ronheywood/PiTrac/docs/3dprint/3dprint_base_layer_piside_floor.md

---
title: 3d Print Base Layer Pi Side Floor
layout: home
parent: 3D Print
nav_order: 3
---

3D Pi Side Floor.. search keyword 123

----
