ronheywood/PiTrac/docs/camera/cameras.md

---
title: Cameras
layout: home
nav_order: 2
---

Camera Parent page..

----
