ronheywood/PiTrac/docs/assets/images/camera/image5.jpg

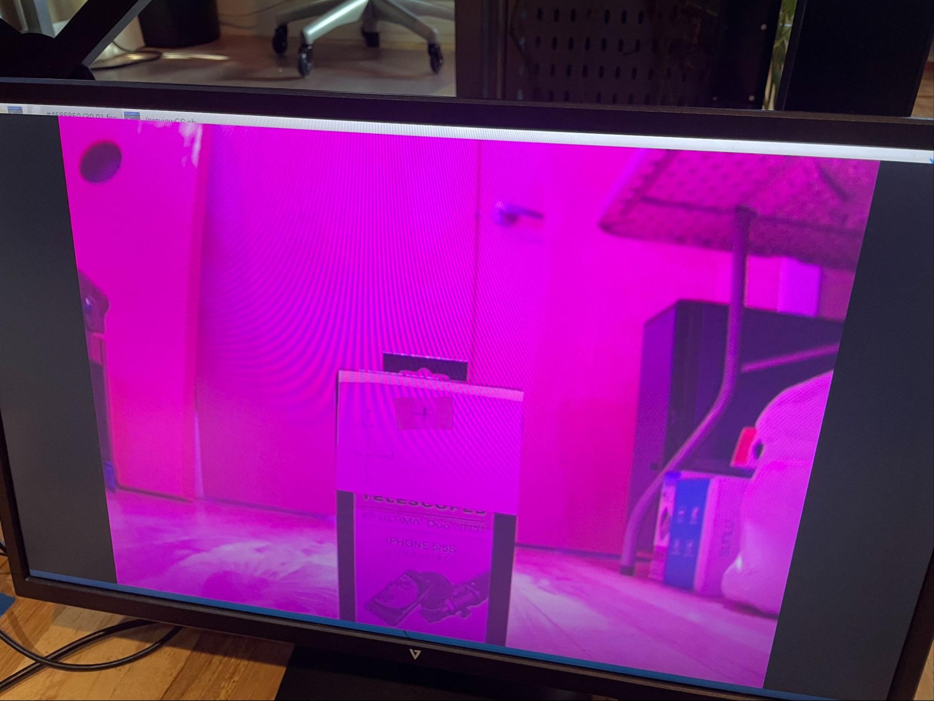
docs/assets/images/camera/image5.jpg
