ronheywood/PiTrac/Documentation/snapshots/index_replace_name.png

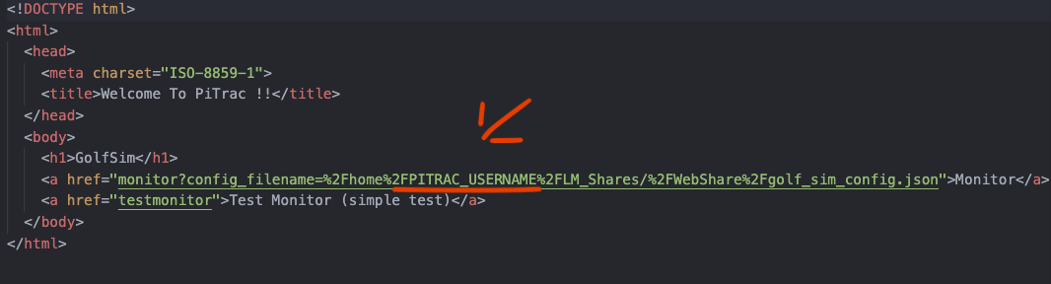
Documentation/snapshots/index_replace_name.png
