ronheywood/PiTrac/Hardware/Connector Board/PCB Board Picture (Both Layers).png

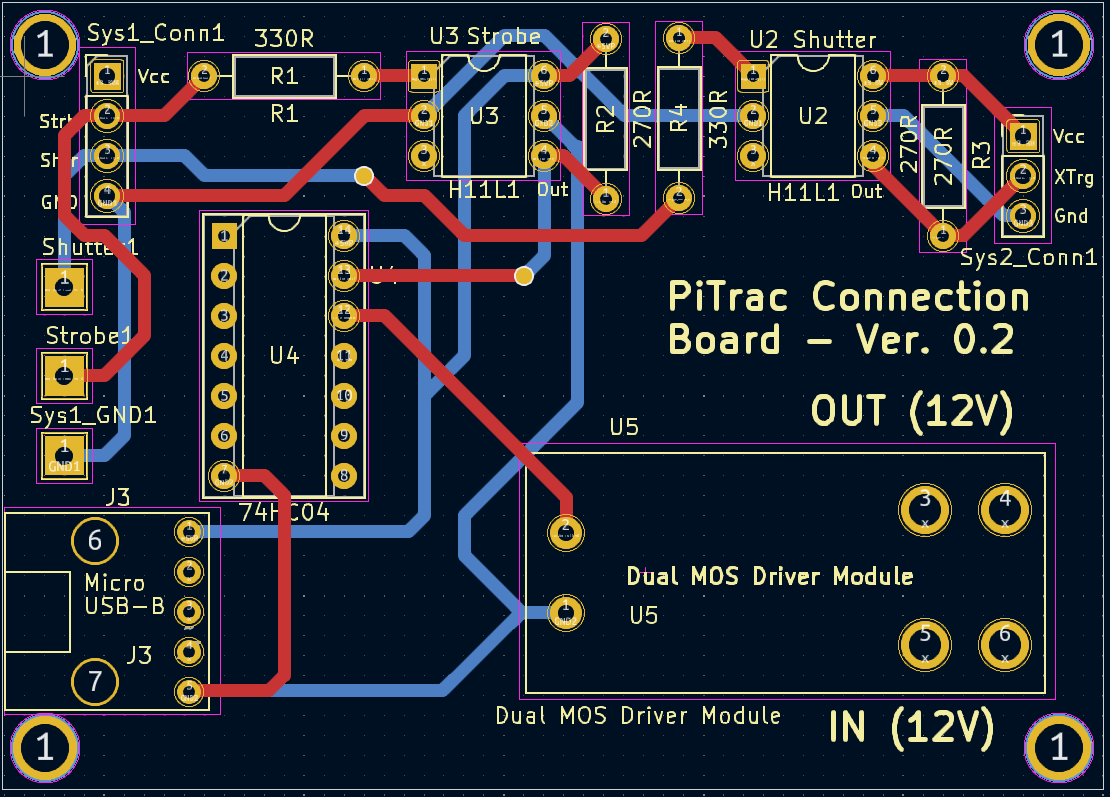
Hardware/Connector Board/PCB Board Picture (Both Layers).png
