ronheywood/PiTrac/Hardware/Connector Board/PiTrac Connector Board - Back.jpg

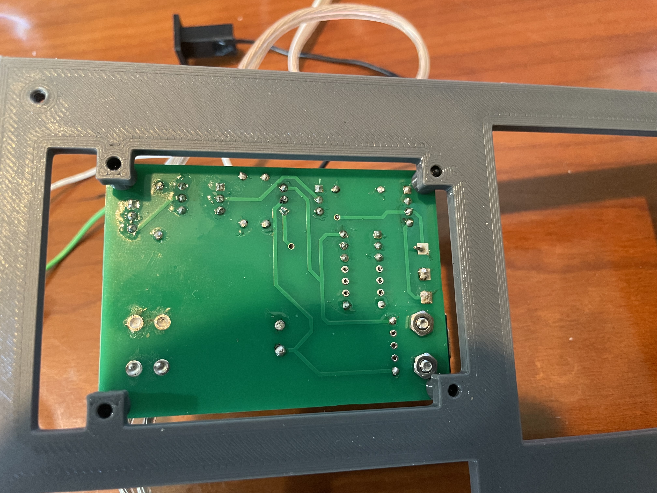
Hardware/Connector Board/PiTrac Connector Board - Back.jpg
