ronheywood/PiTrac/Hardware/Connector Board/PiTrac Connector Board - Front.jpg

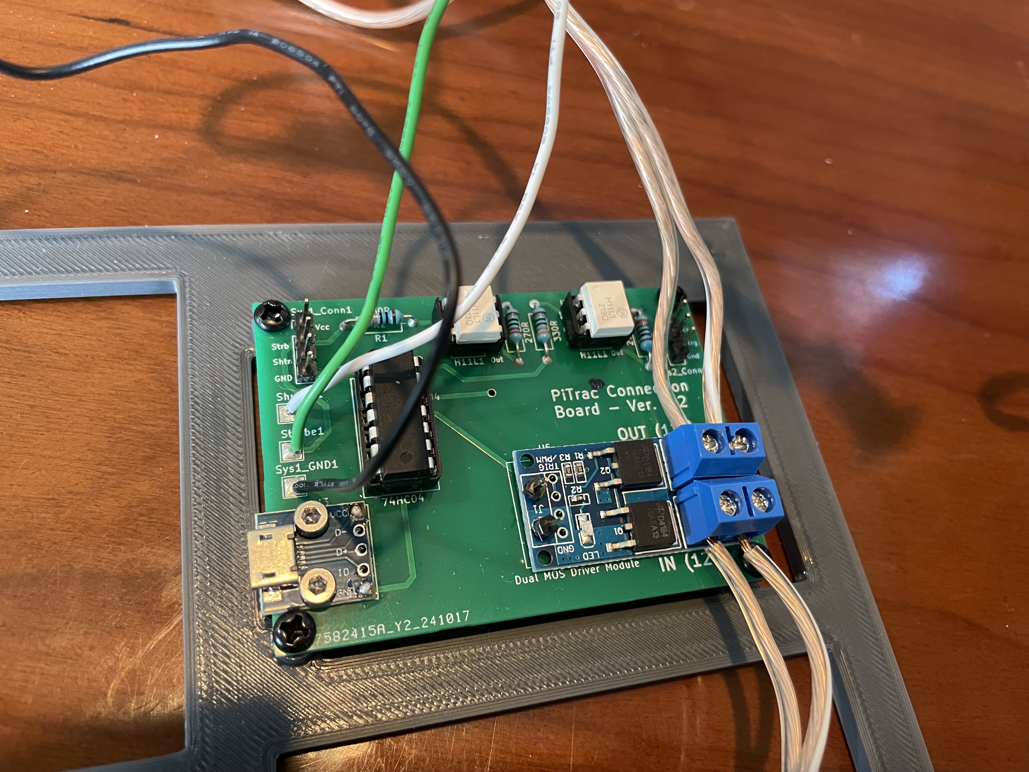
Hardware/Connector Board/PiTrac Connector Board - Front.jpg
