ronheywood/PiTrac/Software/LMSourceCode/Images/gs_log_img__log_ball_final_found_ball_img.png

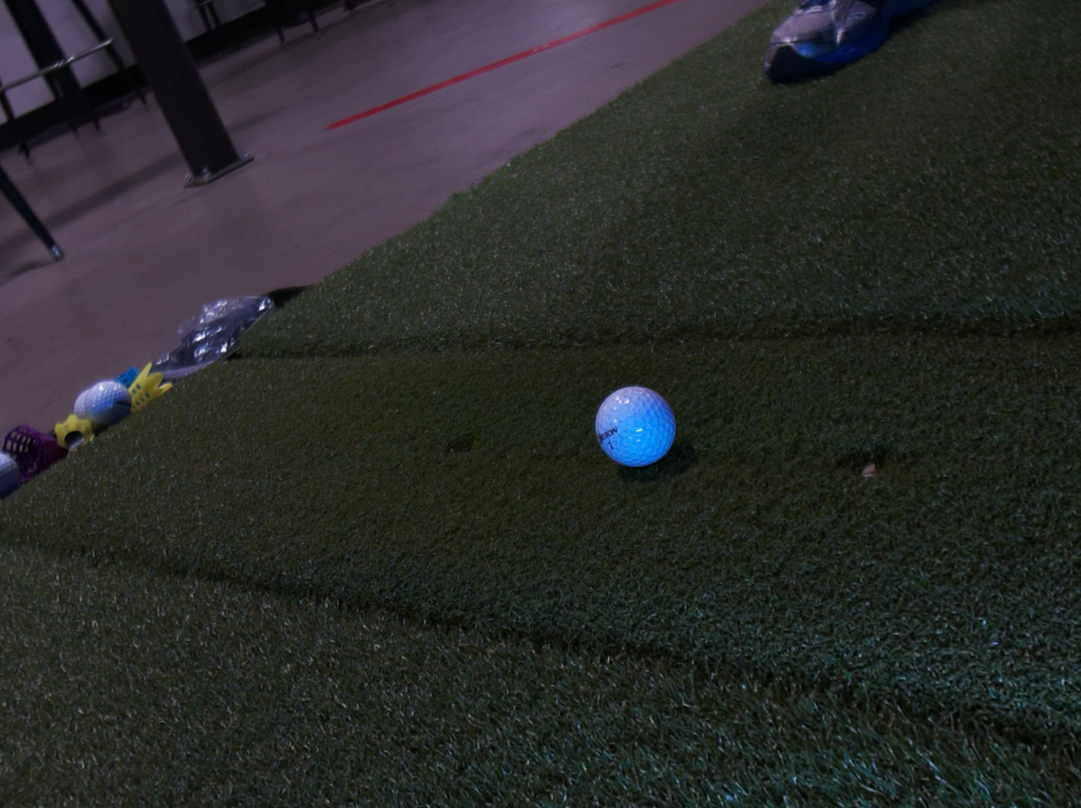
Software/LMSourceCode/Images/gs_log_img__log_ball_final_found_ball_img.png
