ronheywood/PiTrac/Software/LMSourceCode/Images/log_ball_final_found_ball_img.png

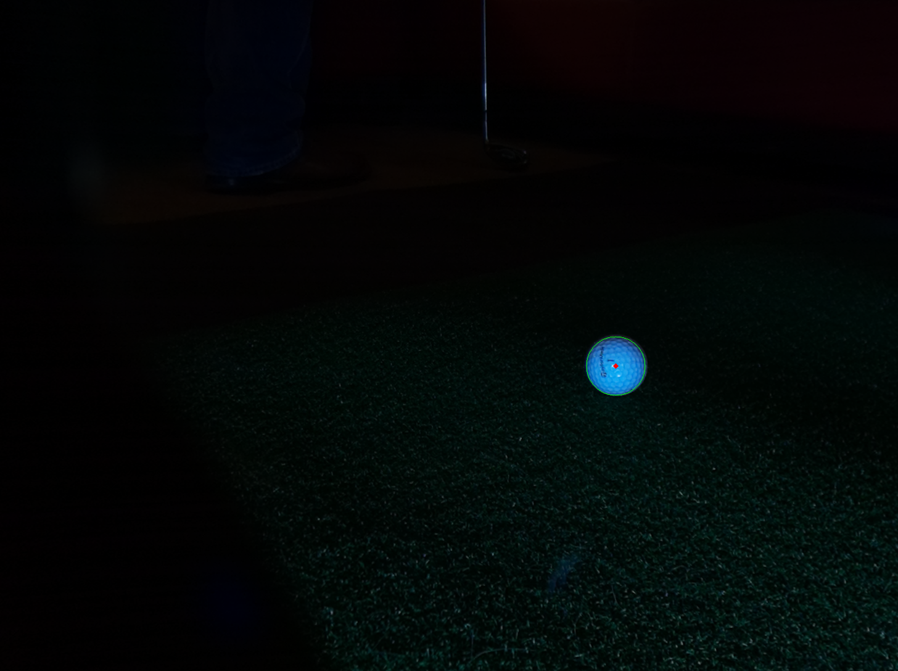
Software/LMSourceCode/Images/log_ball_final_found_ball_img.png
