ronheywood/PiTrac/Software/LMSourceCode/Images/log_ball_final_found_ball_img_232_fast.png

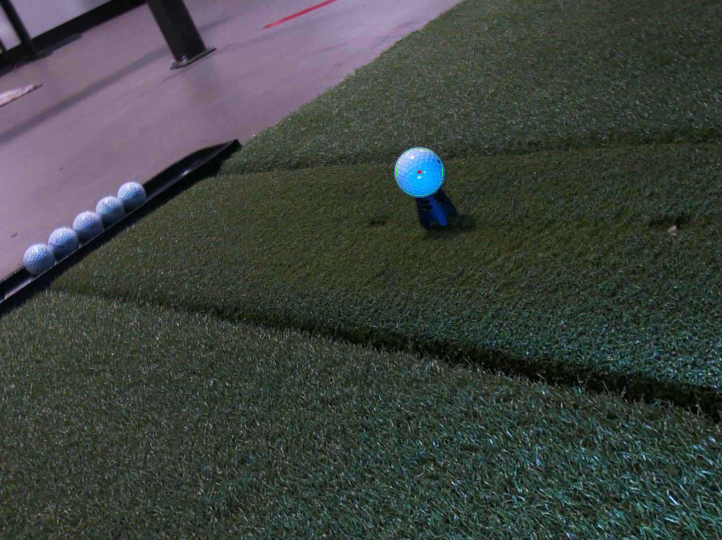
Software/LMSourceCode/Images/log_ball_final_found_ball_img_232_fast.png
