ronheywood/PiTrac/Software/LMSourceCode/Images/log_cam2_last_strobed_img.png

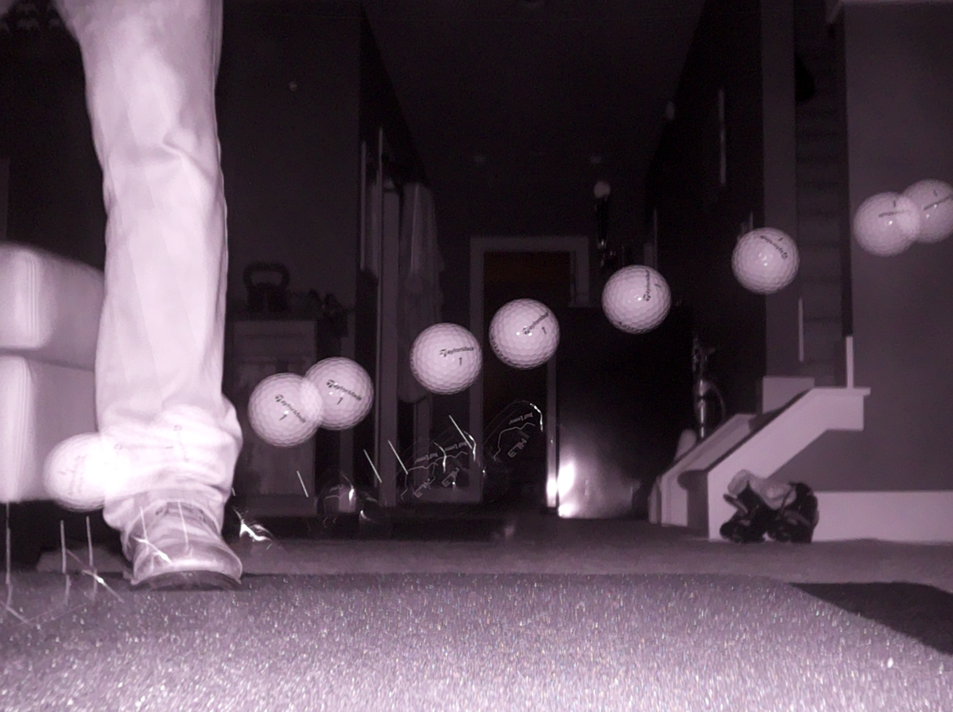
Software/LMSourceCode/Images/log_cam2_last_strobed_img.png
