ronheywood/PiTrac/Software/LMSourceCode/Images/log_cam2_last_strobed_img_232_fast.png

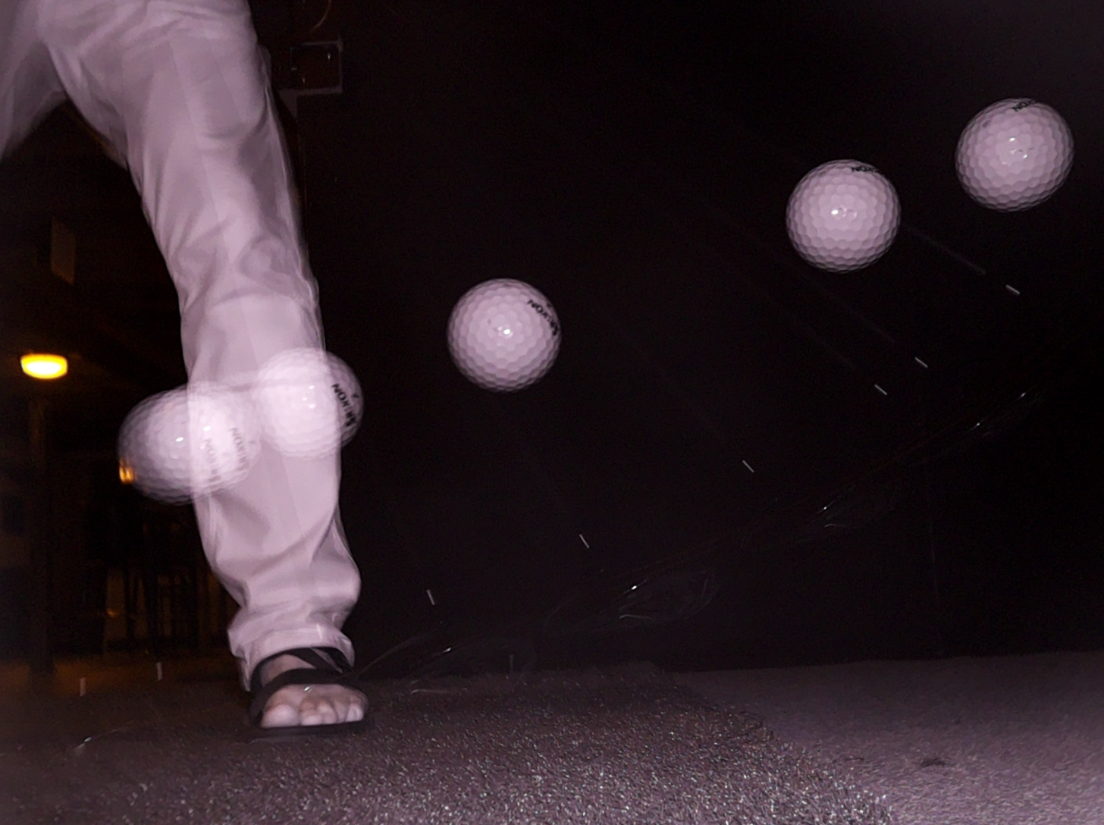
Software/LMSourceCode/Images/log_cam2_last_strobed_img_232_fast.png
