ronheywood/PiTrac/3D Printed Parts/Enclosure Models/Middle Layer - Power Side - Lower Floor/README.md

**Middle Layer – Power Side – Floor - Description:**

Please see the main Enclosure Assembly instructions in the Documentation folder for additional information on this part.

This is the middle-left-most floor portion of the PiTrac Launch Monitor. A [FreeCAD 1.0](https://www.freecad.org/downloads.php) compatible parameterized model is included here along with .stl files. This part a wall to prevent the power supplies and associated wiring from spilling into the area on the Pi side that is reserved for the Pi Camera. There is no “Upper” floor on the power-side in the middle layer.

The model is parameterized for ease of modifications, though the part is complex enough that any changes can sometimes lead to issues in FreeCAD. Modifiable parameters are in the “Master Document” spreadsheet, which is assumed to be in the directory immediately above wherever this part’s FreeCAD file exists.

Please consider supporting this work and the DIY LM project here: <https://ko-fi.com/PiTrac>

**Printing Notes:**

Both PLA or PETG can work for this part. It is a fairly simple part to print successfully.

Recommended print settings: 4 perimeter layers), 15% infill, grid infill patterns, no supports (see Prusa Slicer .3mf file for details).
