ronheywood/PiTrac/3D Printed Parts/Enclosure Models/Base Layer - Pi Side - Floor/Base Layer - Pi Side - Floor - 3D View.png

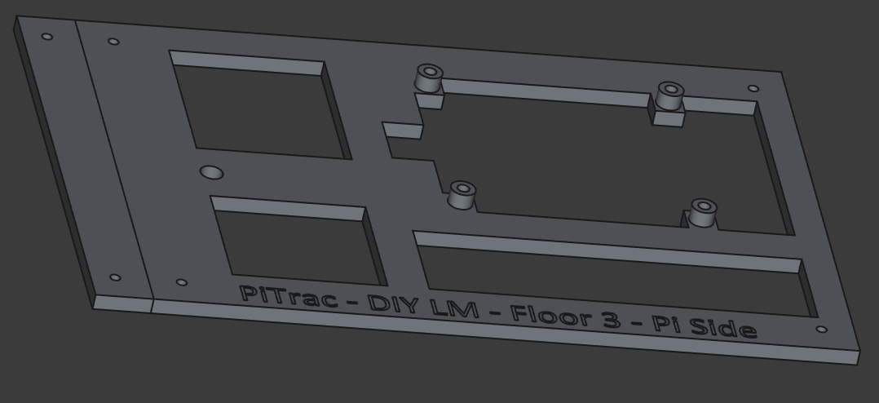
3D Printed Parts/Enclosure Models/Base Layer - Pi Side - Floor/Base Layer - Pi Side - Floor - 3D View.png
