ronheywood/PiTrac/3D Printed Parts/Enclosure Models/Base Layer - Pi Side - Wall/Base Layer - Pi Side - Wall - 3D View.png

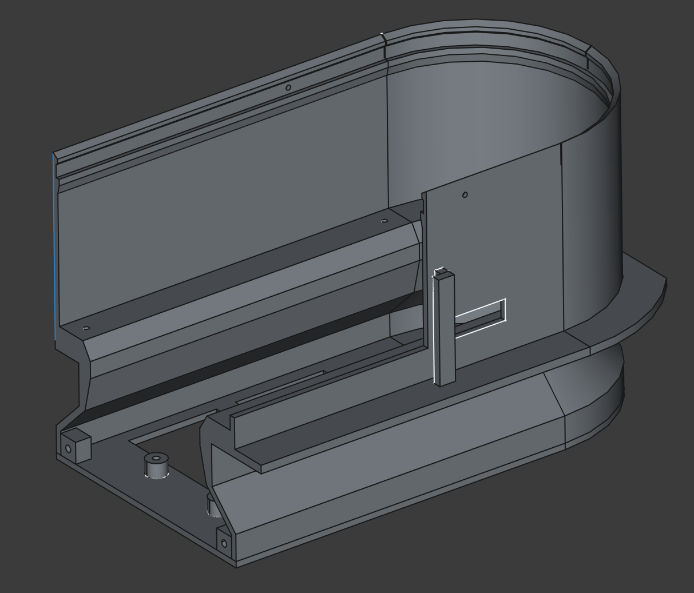
3D Printed Parts/Enclosure Models/Base Layer - Pi Side - Wall/Base Layer - Pi Side - Wall - 3D View.png
