ronheywood/PiTrac/3D Printed Parts/Enclosure Models/Base Layer - Pi Side - Wall/Base Layer - Pi Side - Wall - Slicer Output.png

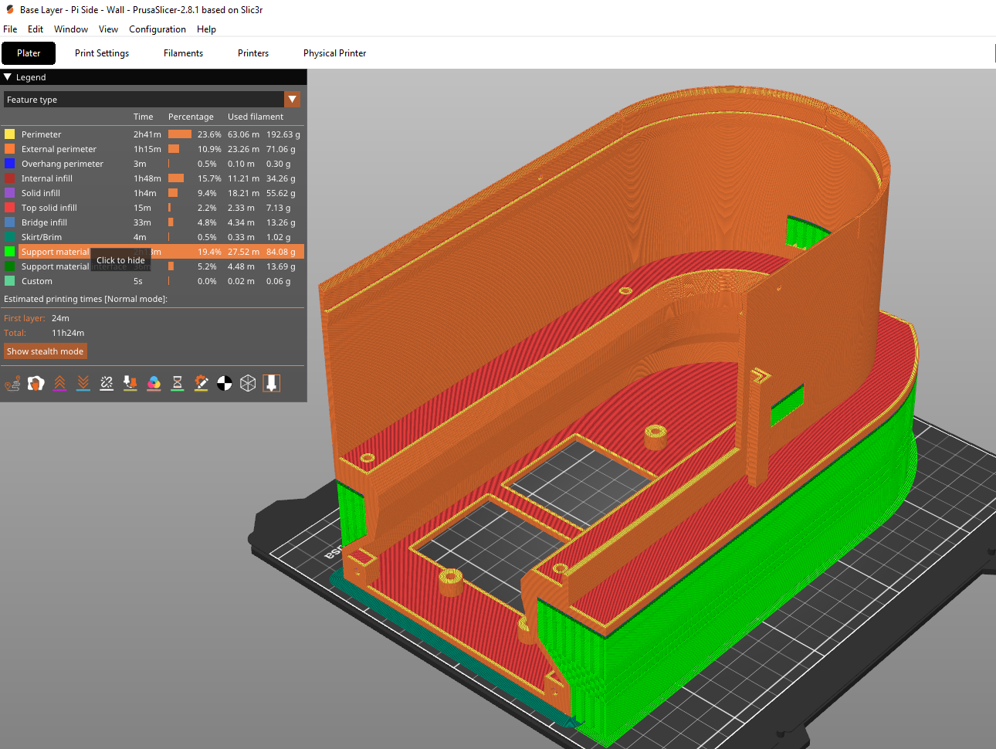
3D Printed Parts/Enclosure Models/Base Layer - Pi Side - Wall/Base Layer - Pi Side - Wall - Slicer Output.png
