ronheywood/PiTrac/3D Printed Parts/Enclosure Models/Base Layer - Power Side - Floor/Base Layer - Power Side - Lower Floor - Slicer Output.png

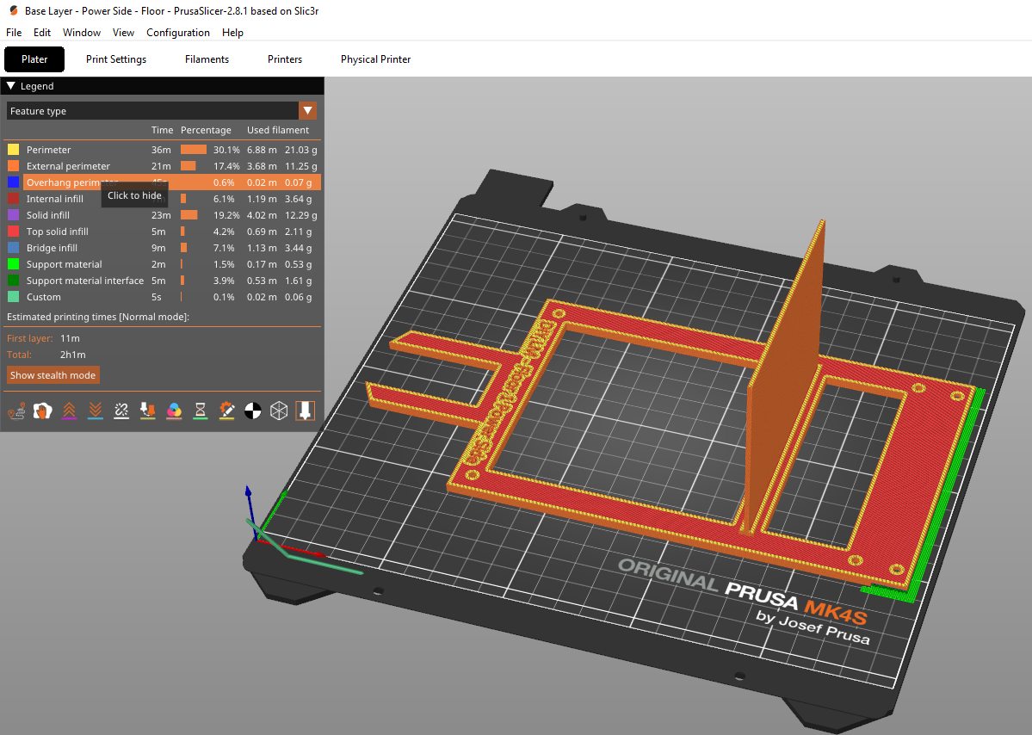
3D Printed Parts/Enclosure Models/Base Layer - Power Side - Floor/Base Layer - Power Side - Lower Floor - Slicer Output.png
