ronheywood/PiTrac/3D Printed Parts/Enclosure Models/Base Layer - Power Side - Wall/Base Layer - Power Side - Wall - 3D View.png

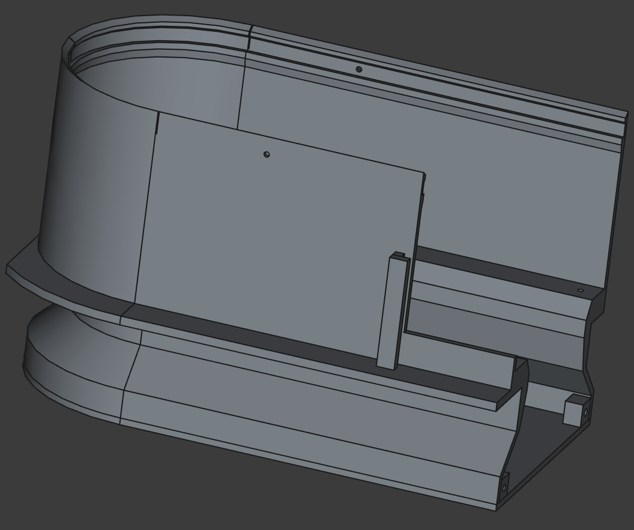
3D Printed Parts/Enclosure Models/Base Layer - Power Side - Wall/Base Layer - Power Side - Wall - 3D View.png
