ronheywood/PiTrac/3D Printed Parts/Enclosure Models/Base Layer - Power Side - Wall/Base Layer - Power Side - Wall - Slicer Output.png

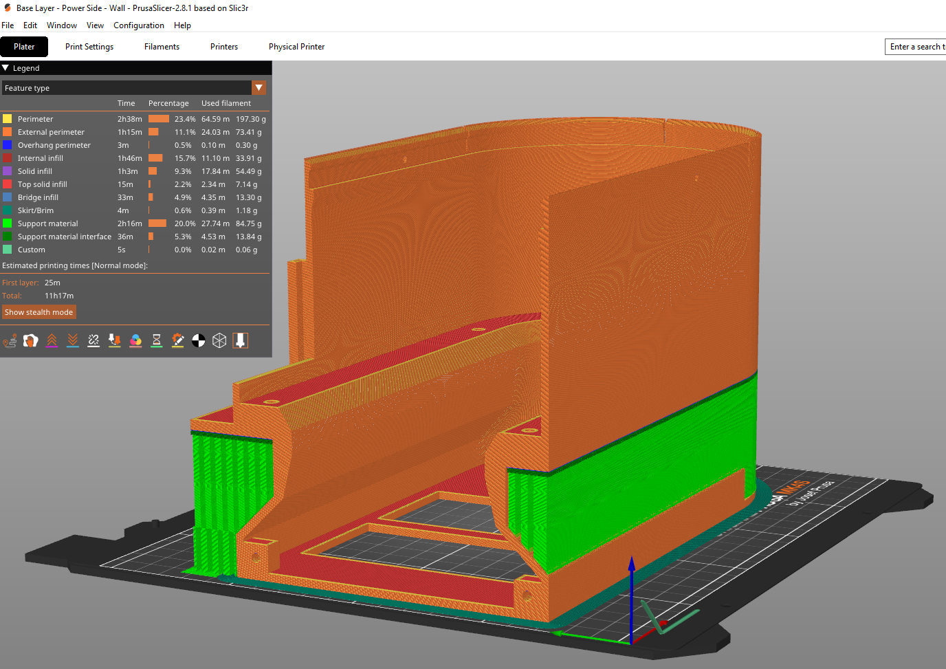
3D Printed Parts/Enclosure Models/Base Layer - Power Side - Wall/Base Layer - Power Side - Wall - Slicer Output.png
