ronheywood/PiTrac/3D Printed Parts/Enclosure Models/Middle Layer - Pi Side - Lower Floor/Middle Layer - Pi Side - Lower Floor - 3D View.png

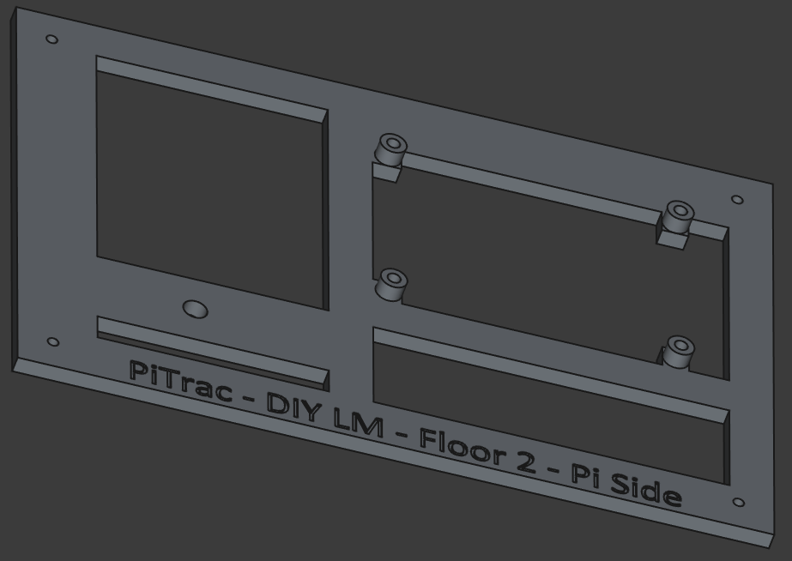
3D Printed Parts/Enclosure Models/Middle Layer - Pi Side - Lower Floor/Middle Layer - Pi Side - Lower Floor - 3D View.png
