ronheywood/PiTrac/3D Printed Parts/Enclosure Models/Middle Layer - Pi Side - Lower Floor/Middle Layer - Pi Side - Lower Floor - Slicer Output.png

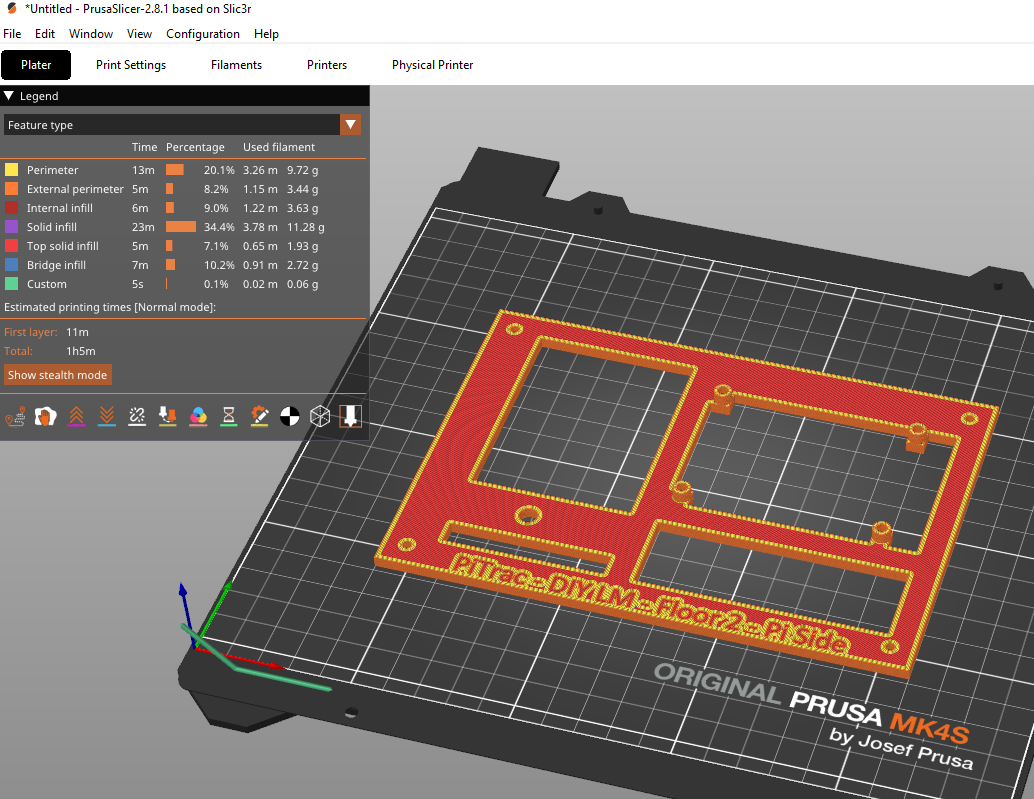
3D Printed Parts/Enclosure Models/Middle Layer - Pi Side - Lower Floor/Middle Layer - Pi Side - Lower Floor - Slicer Output.png
