ronheywood/PiTrac/3D Printed Parts/Enclosure Models/Middle Layer - Pi Side - Upper Floor/Middle Layer - Pi Side - Upper Floor - 3D View.png

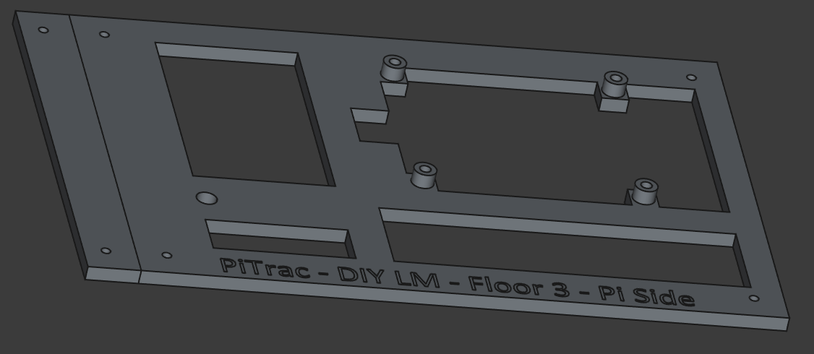
3D Printed Parts/Enclosure Models/Middle Layer - Pi Side - Upper Floor/Middle Layer - Pi Side - Upper Floor - 3D View.png
