ronheywood/PiTrac/3D Printed Parts/Enclosure Models/Middle Layer - Pi Side - Wall/Middle Layer - Pi Side - Wall - 3D View.png

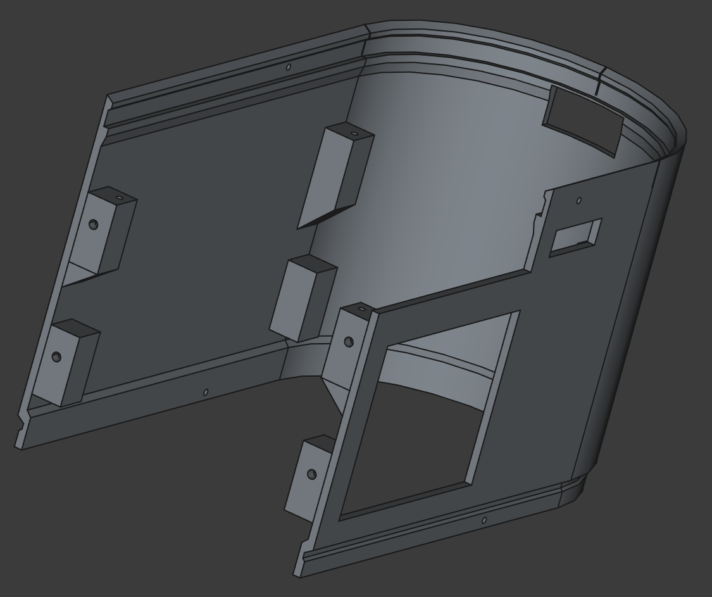
3D Printed Parts/Enclosure Models/Middle Layer - Pi Side - Wall/Middle Layer - Pi Side - Wall - 3D View.png
