ronheywood/PiTrac/3D Printed Parts/Enclosure Models/Middle Layer - Pi Side - Wall/Middle Layer - Pi Side - Wall - Slicer Output.png

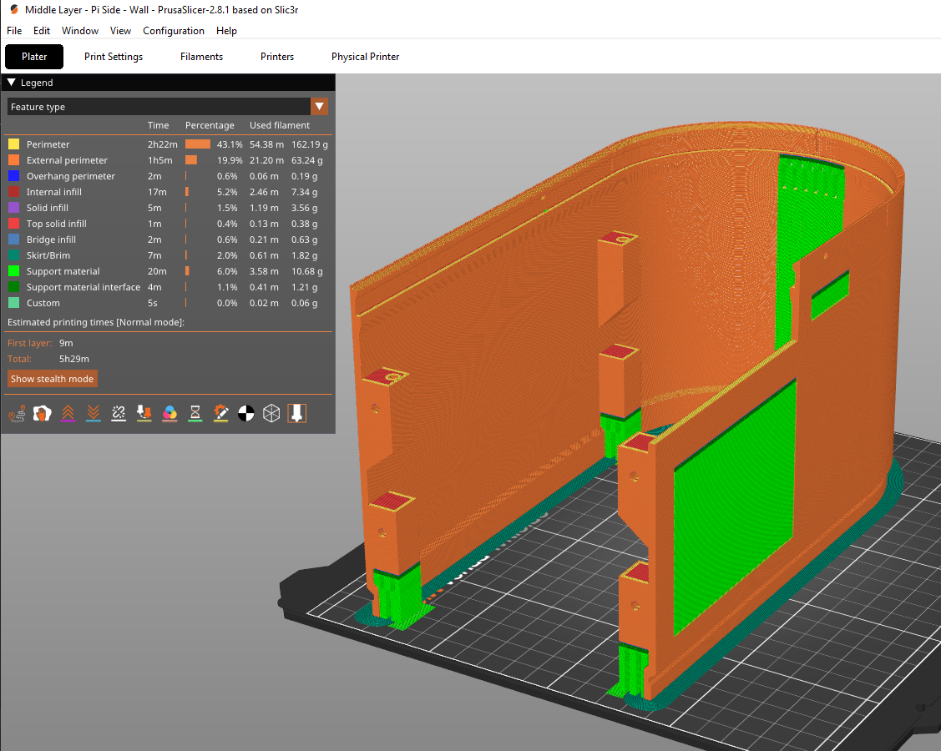
3D Printed Parts/Enclosure Models/Middle Layer - Pi Side - Wall/Middle Layer - Pi Side - Wall - Slicer Output.png
