ronheywood/PiTrac/3D Printed Parts/Enclosure Models/Middle Layer - Power Side - Lower Floor/Middle Layer - Power Side - Lower - Slicer Output.png

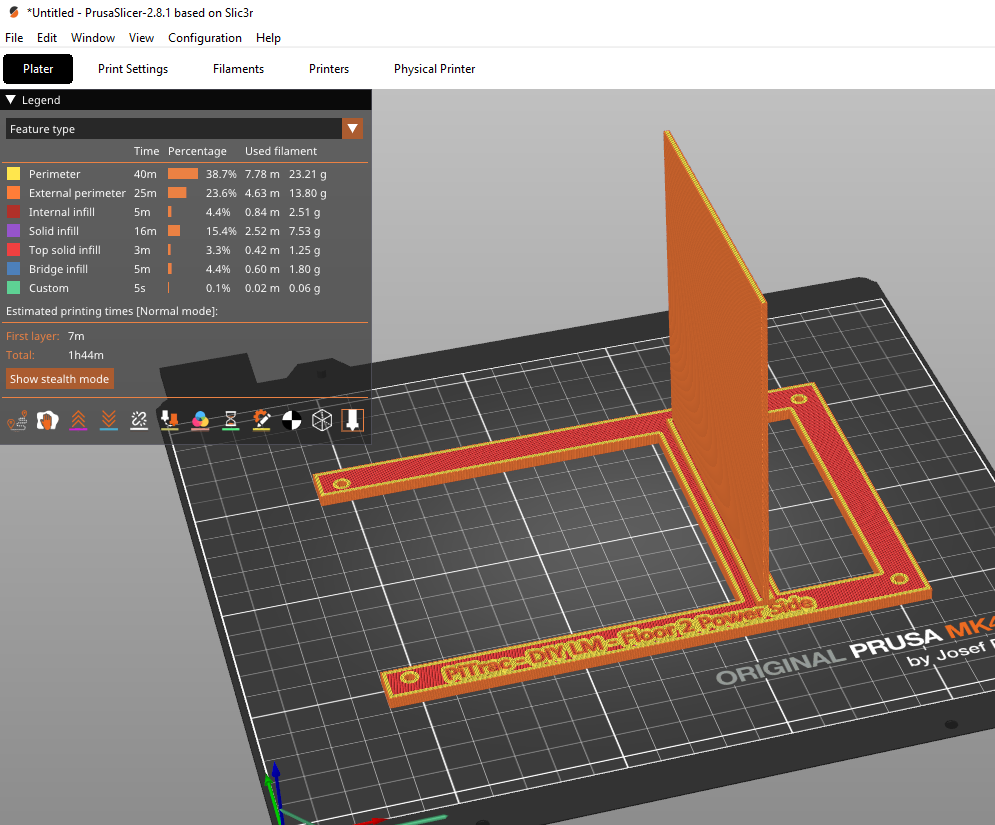
3D Printed Parts/Enclosure Models/Middle Layer - Power Side - Lower Floor/Middle Layer - Power Side - Lower - Slicer Output.png
