ronheywood/PiTrac/3D Printed Parts/Enclosure Models/Middle Layer - Power Side - Wall/Middle Layer - Power Side - Wall - 3D View.docx.png

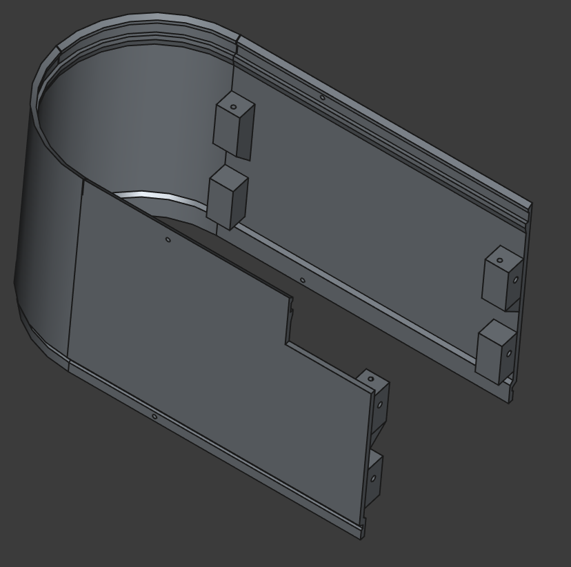
3D Printed Parts/Enclosure Models/Middle Layer - Power Side - Wall/Middle Layer - Power Side - Wall - 3D View.docx.png
