ronheywood/PiTrac/3D Printed Parts/Enclosure Models/Middle Layer - Power Side - Wall/Middle Layer - Power Side - Wall -Slicer Output.png

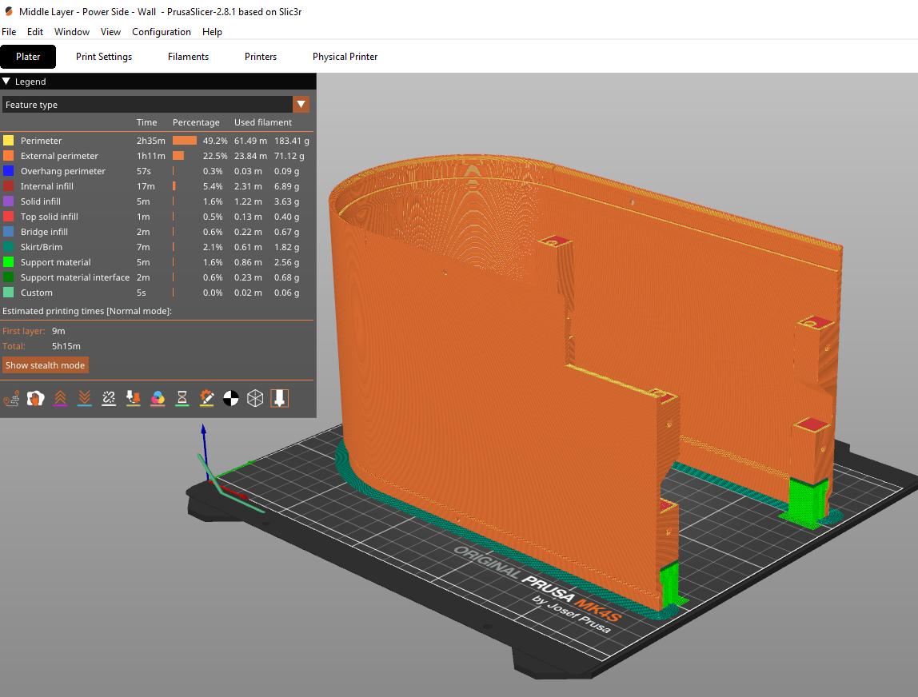
3D Printed Parts/Enclosure Models/Middle Layer - Power Side - Wall/Middle Layer - Power Side - Wall -Slicer Output.png
