ronheywood/PiTrac/3D Printed Parts/Enclosure Models/Top Layer - Pi Side - Wall/Top Layer - Pi Side - Wall - 3D View.png

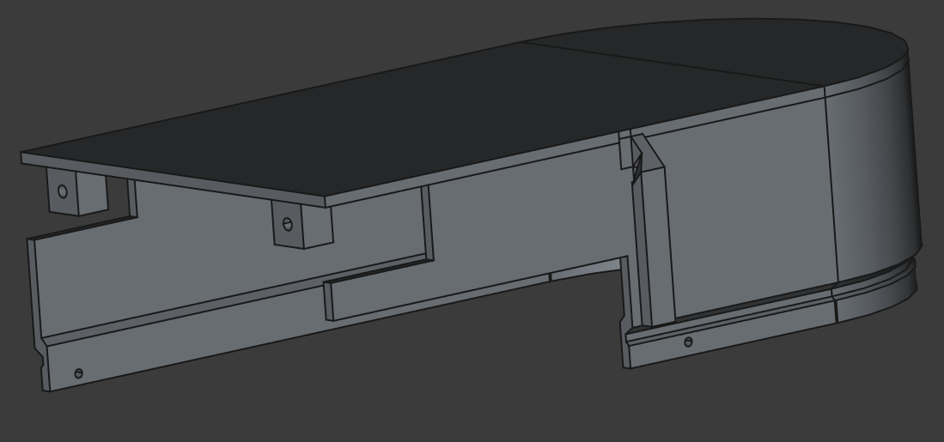
3D Printed Parts/Enclosure Models/Top Layer - Pi Side - Wall/Top Layer - Pi Side - Wall - 3D View.png
