ronheywood/PiTrac/3D Printed Parts/Enclosure Models/Top Layer - Pi Side - Wall/Top Layer - Pi Side - Wall - Slicer Output.png

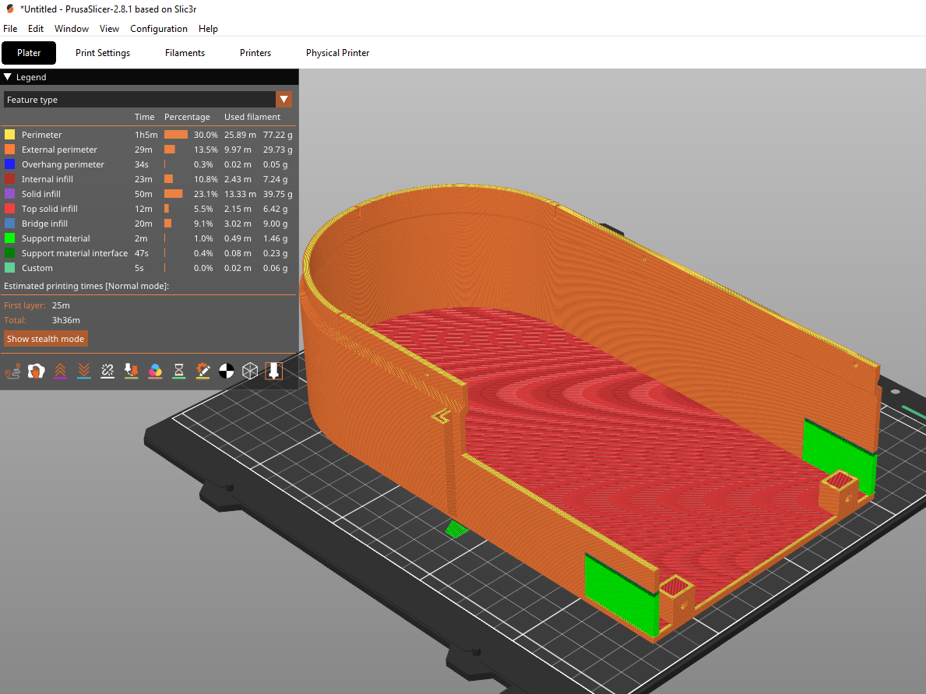
3D Printed Parts/Enclosure Models/Top Layer - Pi Side - Wall/Top Layer - Pi Side - Wall - Slicer Output.png
