ronheywood/PiTrac/3D Printed Parts/Enclosure Models/Top Layer - Power Side - Wall/Top Layer - Power Side - Wall - 3D View.png

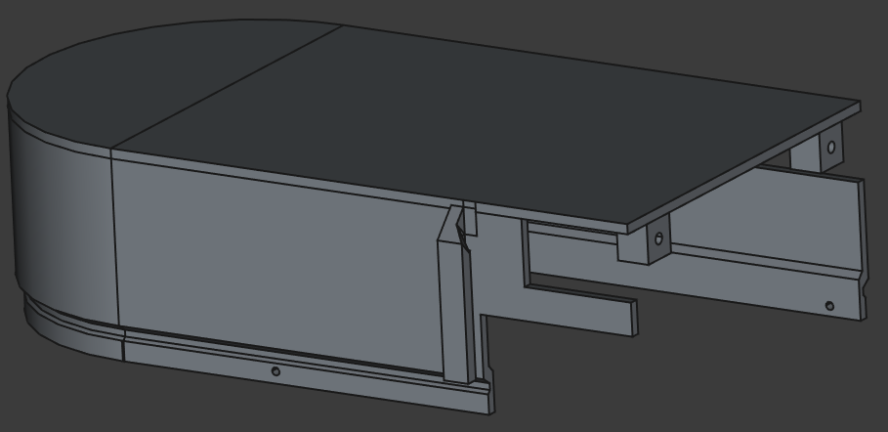
3D Printed Parts/Enclosure Models/Top Layer - Power Side - Wall/Top Layer - Power Side - Wall - 3D View.png
