ronheywood/PiTrac/3D Printed Parts/Enclosure Models/Top Layer - Power Side - Wall/Top Layer - Power Side - Wall - Slicer Output.png

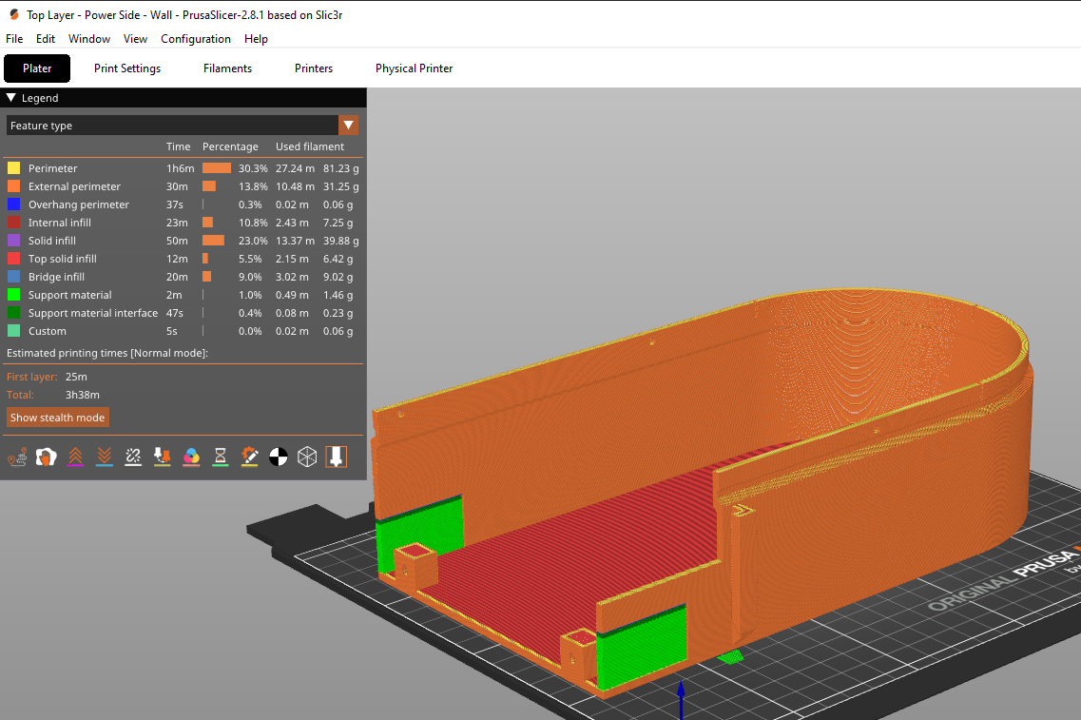
3D Printed Parts/Enclosure Models/Top Layer - Power Side - Wall/Top Layer - Power Side - Wall - Slicer Output.png
