ronheywood/PiTrac/3D Printed Parts/Enclosure Version 2/BaseBox/BaseBox - 3D Model.png

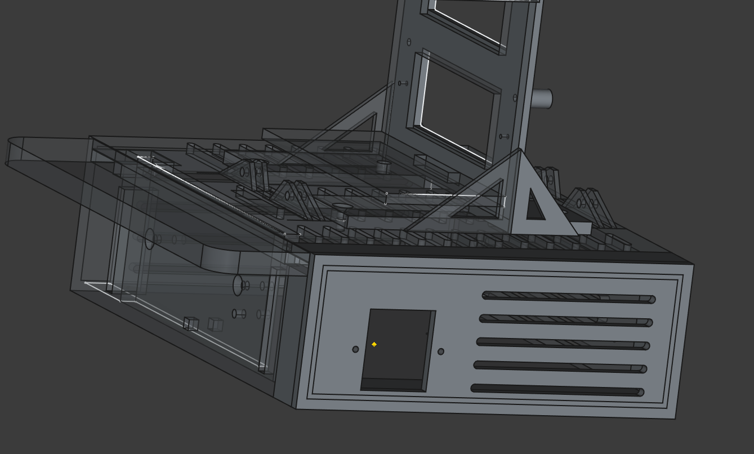
3D Printed Parts/Enclosure Version 2/BaseBox/BaseBox - 3D Model.png
