ronheywood/PiTrac/3D Printed Parts/Enclosure Version 2/BaseBox/BaseBox - End Cap - Slicer Output.png

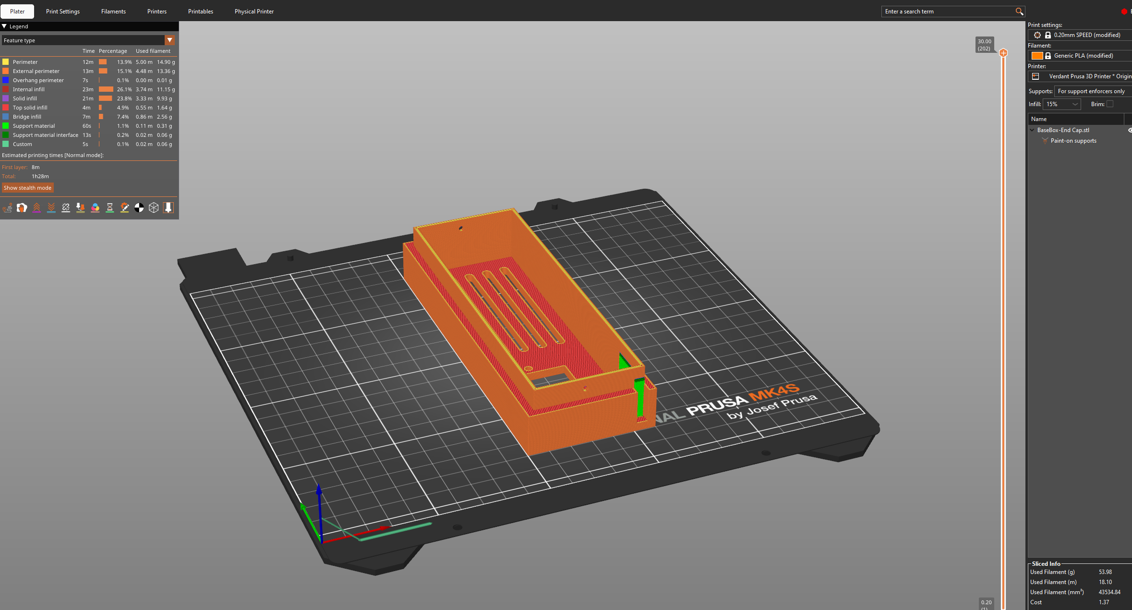
3D Printed Parts/Enclosure Version 2/BaseBox/BaseBox - End Cap - Slicer Output.png
