ronheywood/PiTrac/3D Printed Parts/Enclosure Version 2/BaseBox/BaseBox - Main Body - Slicer Output.png

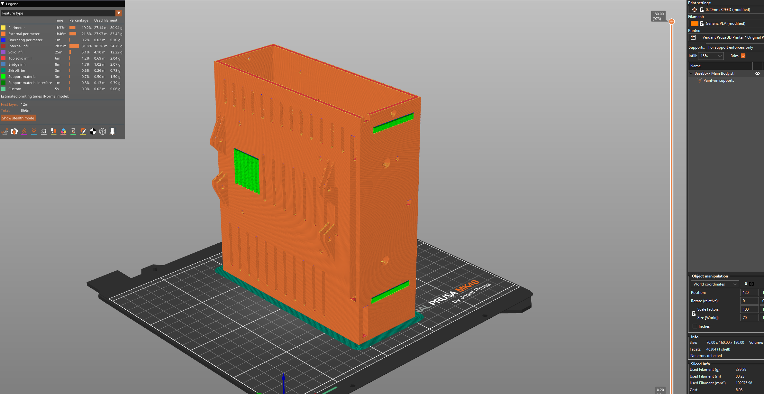
3D Printed Parts/Enclosure Version 2/BaseBox/BaseBox - Main Body - Slicer Output.png
