ronheywood/PiTrac/3D Printed Parts/Enclosure Version 2/LED-Array-Strobe-Light-Mount/Strobe Mount - Back View.jpg

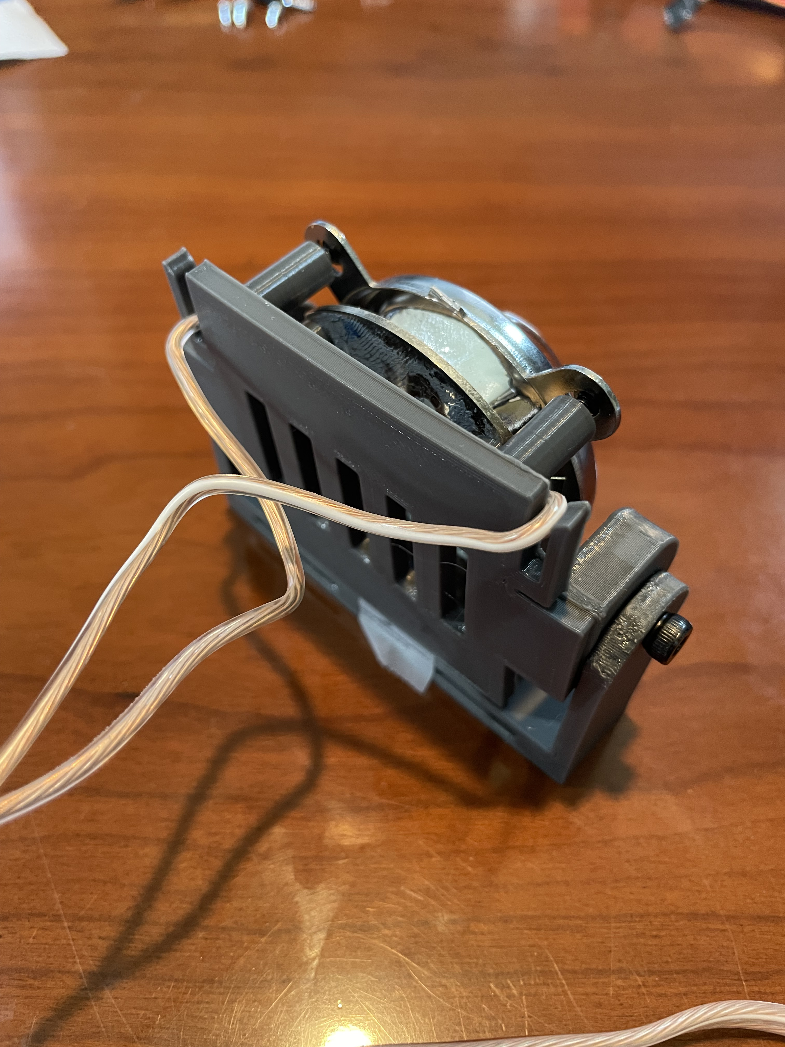
3D Printed Parts/Enclosure Version 2/LED-Array-Strobe-Light-Mount/Strobe Mount - Back View.jpg
