ronheywood/PiTrac/3D Printed Parts/Enclosure Version 2/Pi-Camera-Light-Filter-Holder - M12/Filter Holder - Annotated 3D Model.png

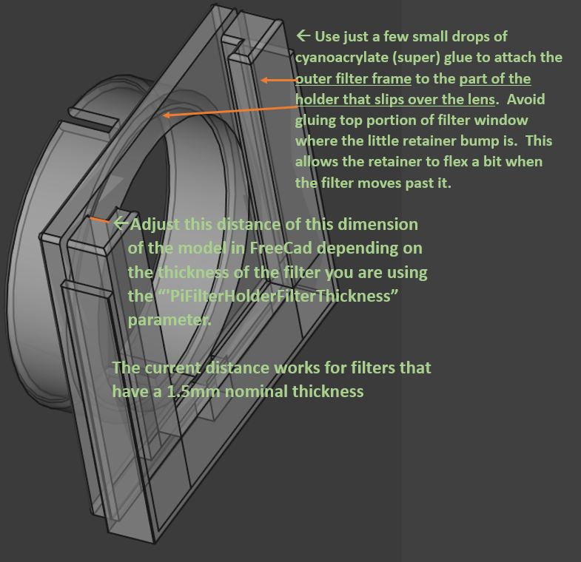
3D Printed Parts/Enclosure Version 2/Pi-Camera-Light-Filter-Holder - M12/Filter Holder - Annotated 3D Model.png
