ronheywood/PiTrac/3D Printed Parts/Enclosure Version 2/Pi-Camera-Light-Filter-Holder - M12/Filter Holder - Prusa Slicer Output.png

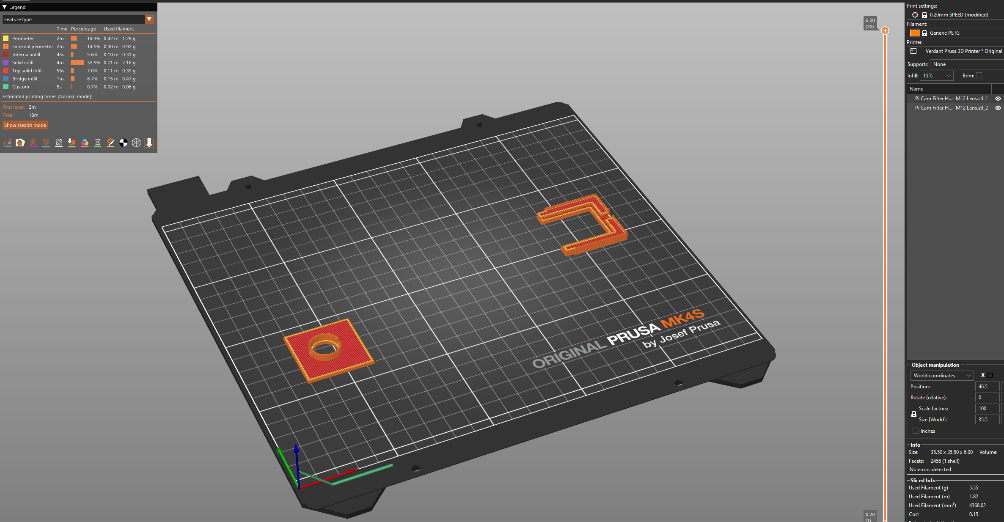
3D Printed Parts/Enclosure Version 2/Pi-Camera-Light-Filter-Holder - M12/Filter Holder - Prusa Slicer Output.png
