ronheywood/PiTrac/3D Printed Parts/Enclosure Version 2/Pi-Camera-Light-Filter-Holder - M12/Filter Holder on Camera.jpg

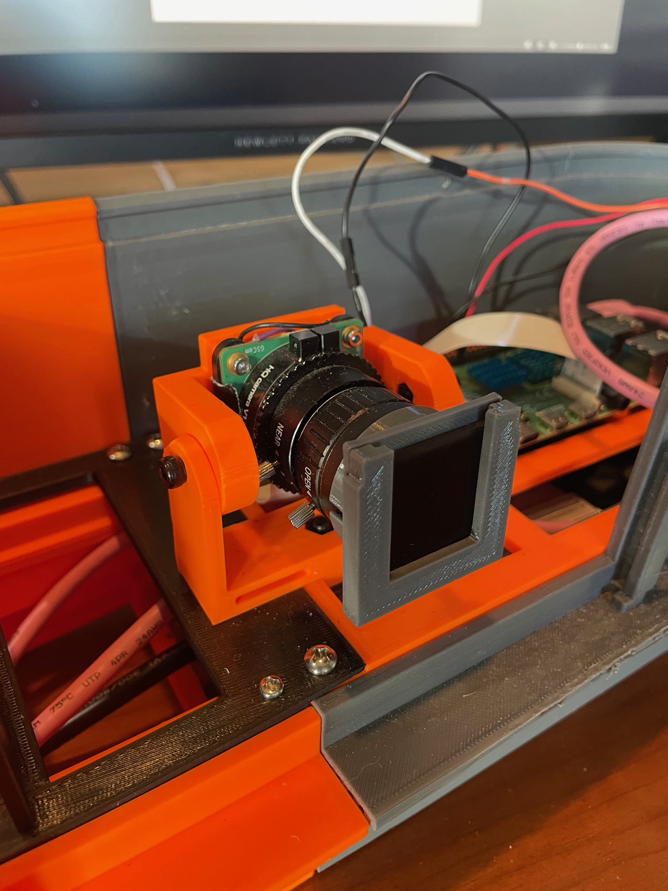
3D Printed Parts/Enclosure Version 2/Pi-Camera-Light-Filter-Holder - M12/Filter Holder on Camera.jpg
