ronheywood/PiTrac/3D Printed Parts/Enclosure Version 2/Pi-Camera-Mounts - Innomaker CAM-IMX296/Pi Camera Mount -  Innomaker IMX296 - Example - Back.jpg

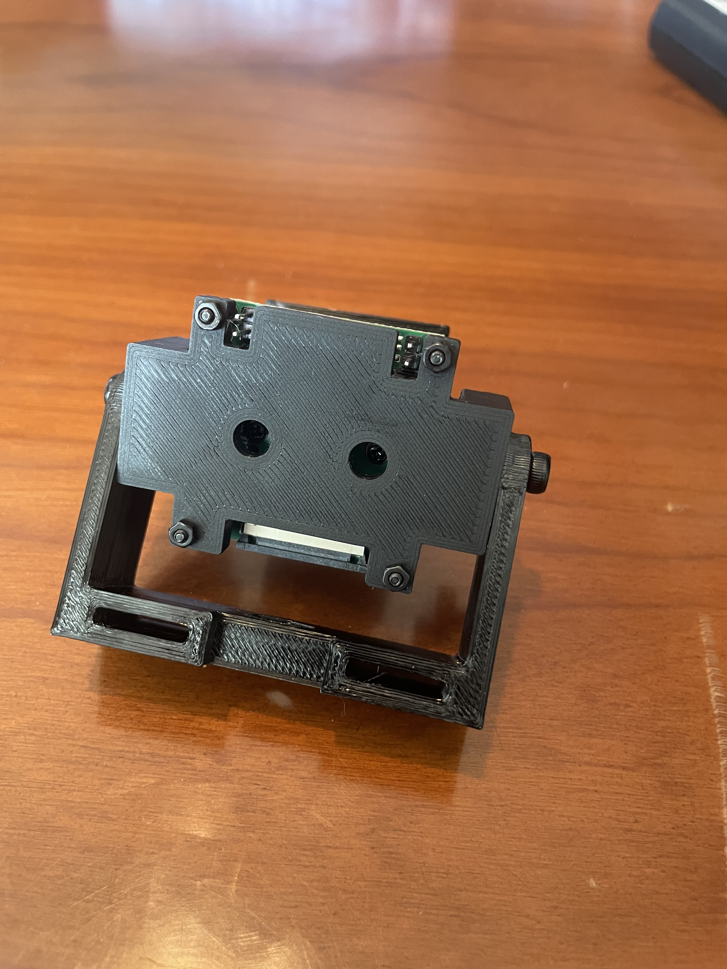
3D Printed Parts/Enclosure Version 2/Pi-Camera-Mounts - Innomaker CAM-IMX296/Pi Camera Mount - Innomaker IMX296 - Example - Back.jpg
