ronheywood/PiTrac/3D Printed Parts/Enclosure Version 2/Pi-Camera-Mounts - Innomaker CAM-IMX296/Pi Camera Mount - Example Variations.png

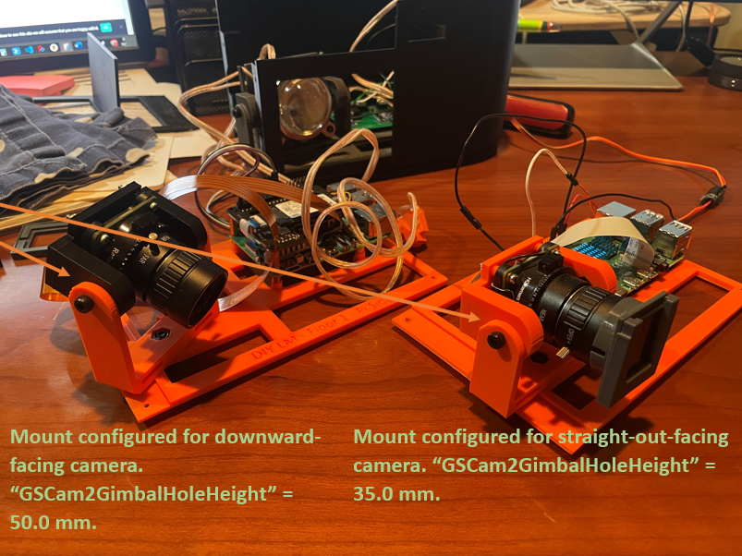
3D Printed Parts/Enclosure Version 2/Pi-Camera-Mounts - Innomaker CAM-IMX296/Pi Camera Mount - Example Variations.png
