ronheywood/PiTrac/3D Printed Parts/Enclosure Version 2/Tower/Tower - 3D Model.png

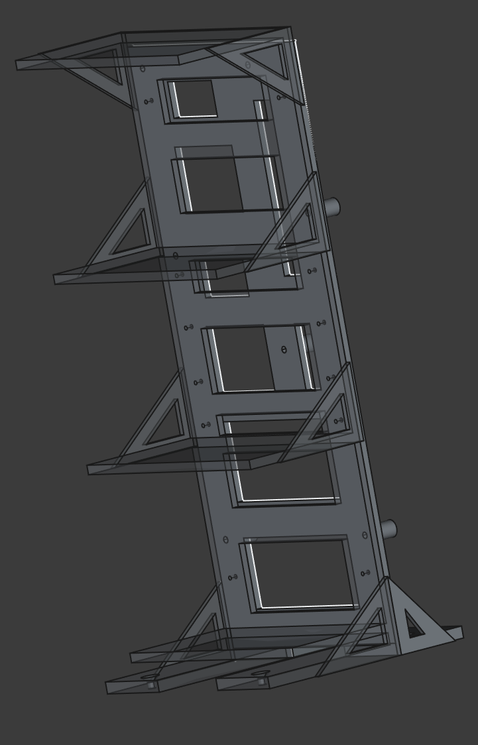
3D Printed Parts/Enclosure Version 2/Tower/Tower - 3D Model.png
