ronheywood/PiTrac/3D Printed Parts/Enclosure Version 2/Tower/Tower - Backplate - Slicer Output.png

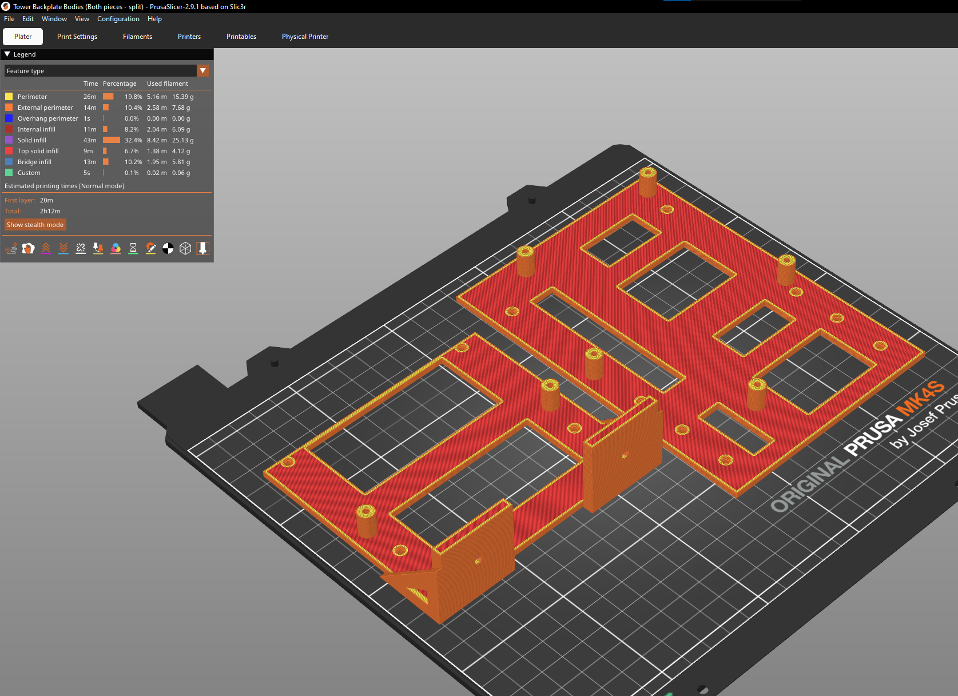
3D Printed Parts/Enclosure Version 2/Tower/Tower - Backplate - Slicer Output.png
