ronheywood/PiTrac/3D Printed Parts/Enclosure Version 2/CaseCover/CaseCover.FCStd

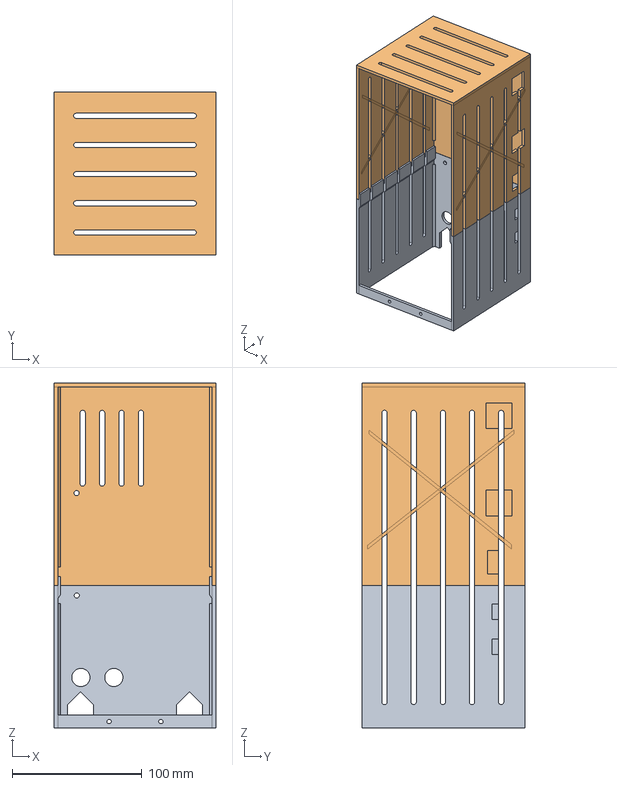
[picture p82: CAD file, 2025-05-21]
3D Printed Parts/Enclosure Version 2/CaseCover/CaseCover.FCStd
124.6 x 126.0 x 266.1 mm
Lower Case Cover Body
Upper Case Cover Body
