ronheywood/PiTrac/3D Printed Parts/Enclosure Version 2/Integrated Enclosure (DO NOT PRINT)/C14 Panel Mount Power Plug Adapter w Fuse - JR-101-1F.FCStd

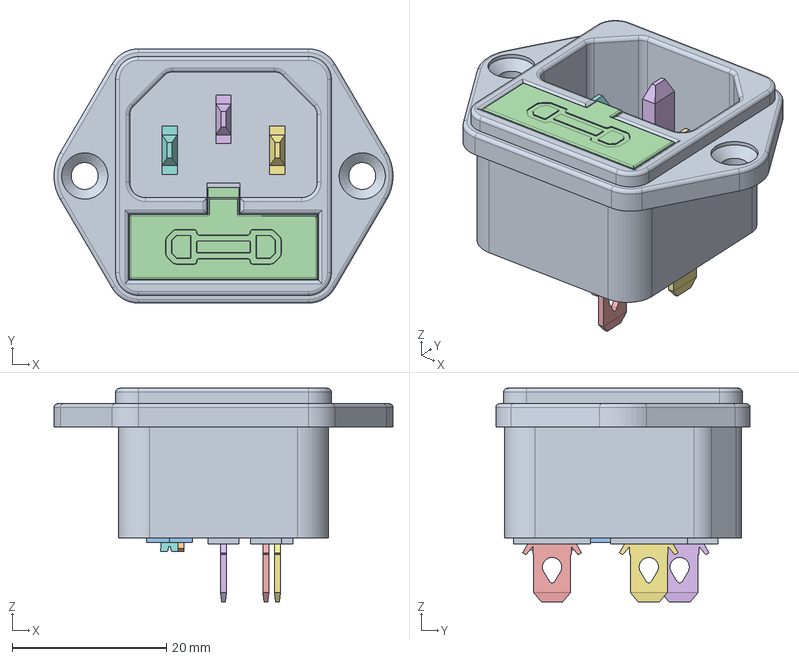
[picture p83: CAD file, 2025-03-30]
3D Printed Parts/Enclosure Version 2/Integrated Enclosure (DO NOT PRINT)/C14 Panel Mount Power Plug Adapter w Fuse - JR-101-1F.FCStd
44.0 x 33.0 x 27.7 mm
JR-101-1F
JR-101-1F001
JR-101-1F002
JR-101-1F003
JR-101-1F004
JR-101-1F005
JR-101-1F006
JR-101-1F007
