ronheywood/PiTrac/3D Printed Parts/Enclosure Version 2/LED-Array-Strobe-Light-Mount/LED Light Mount.FCStd

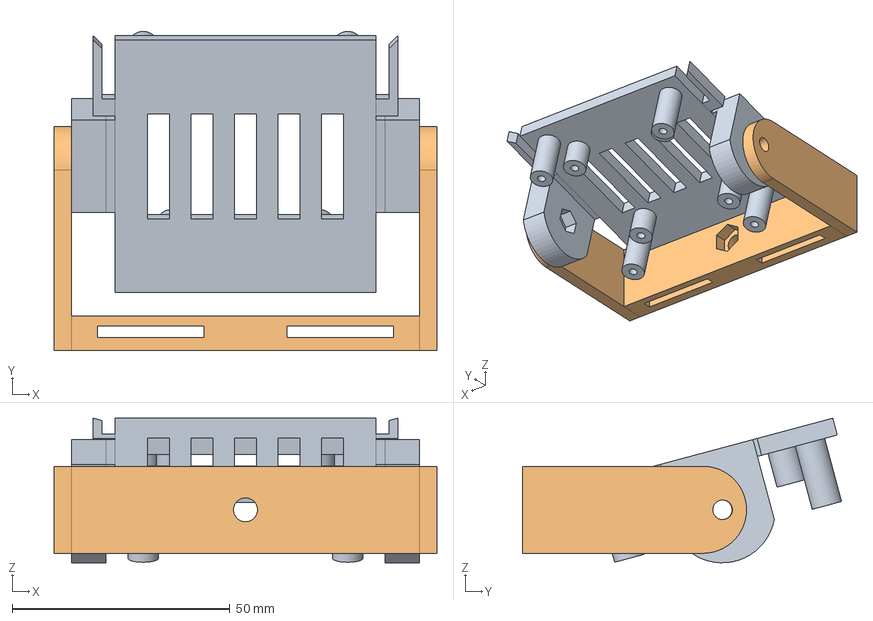
[picture p84: CAD file, 2025-05-07]
3D Printed Parts/Enclosure Version 2/LED-Array-Strobe-Light-Mount/LED Light Mount.FCStd
88.0 x 73.3 x 33.2 mm
LED Back Plate
LED Gimbal
