ronheywood/PiTrac/3D Printed Parts/Enclosure Version 2/Pi-Camera-Light-Filter-Holder - M12/Pi Cam Filter Holder - M12 Lens - Both Halves Split.stl

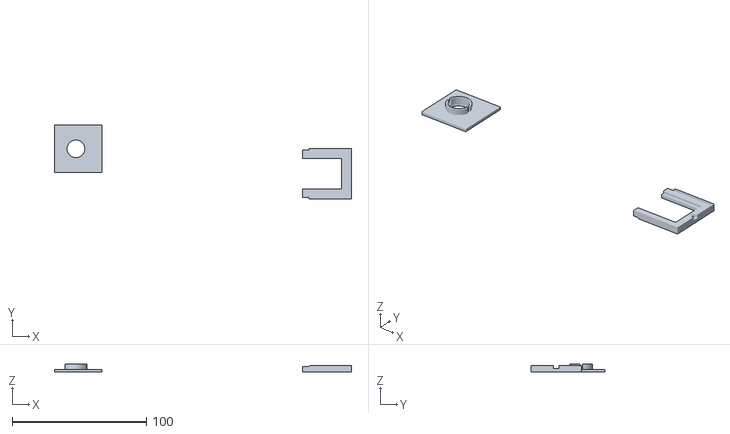
[picture p85: CAD file, 2025-07-09]
3D Printed Parts/Enclosure Version 2/Pi-Camera-Light-Filter-Holder - M12/Pi Cam Filter Holder - M12 Lens - Both Halves Split.stl
221.3 x 55.1 x 6.00
