ronheywood/PiTrac/3D Printed Parts/Enclosure Version 2/Pi-Camera-Light-Filter-Holder/Pi Cam Filter Holder v1.00.FCStd

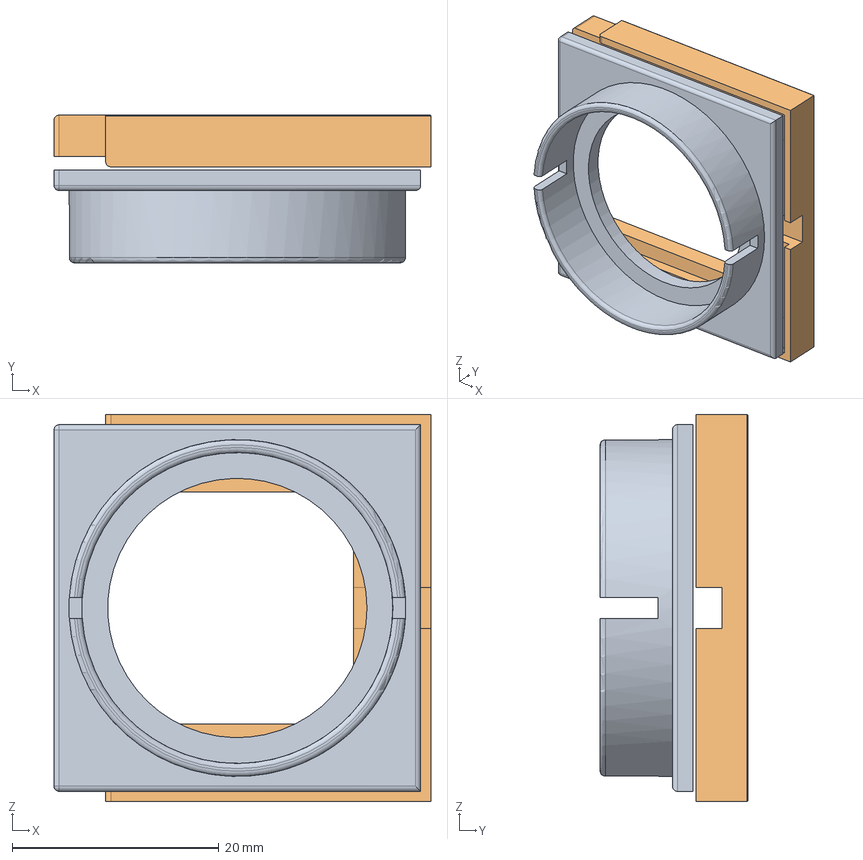
[picture p86: CAD file, 2025-03-30]
3D Printed Parts/Enclosure Version 2/Pi-Camera-Light-Filter-Holder/Pi Cam Filter Holder v1.00.FCStd
36.5 x 14.3 x 37.5 mm
Filter Holder Body
Holder Wings Body
