ronheywood/PiTrac/3D Printed Parts/Enclosure Version 2/Pi-Camera-Mounts - Innomaker CAM-IMX296/Camera Mount - Bottom Variation - Both Parts Separated.stl

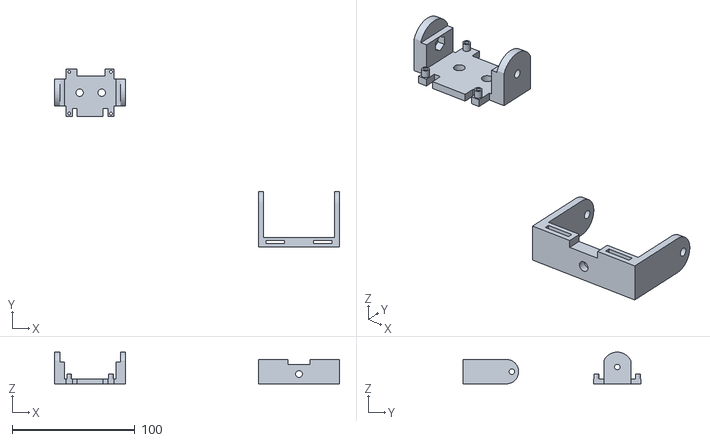
[picture p87: CAD file, 2025-06-30]
3D Printed Parts/Enclosure Version 2/Pi-Camera-Mounts - Innomaker CAM-IMX296/Camera Mount - Bottom Variation - Both Parts Separated.stl
232.2 x 145.3 x 25.9
