ronheywood/PiTrac/3D Printed Parts/Enclosure Version 2/Pi-Camera-Mounts/Camera Mount - Bottom Variation.3mf

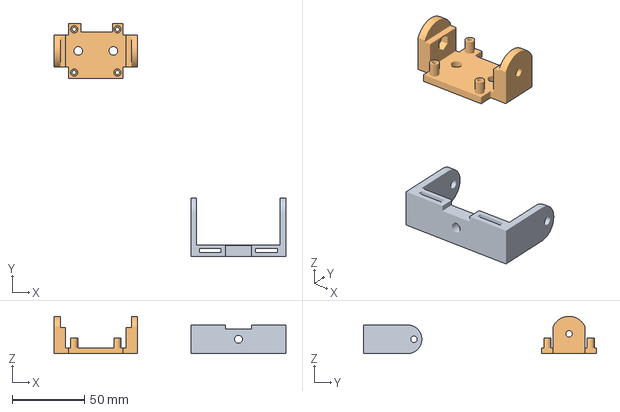
[picture p88: CAD file, 2025-03-30]
3D Printed Parts/Enclosure Version 2/Pi-Camera-Mounts/Camera Mount - Bottom Variation.3mf
161.0 x 161.6 x 25.9 mm
Camera Mount - Bottom Variation.stl_1
Camera Mount - Bottom Variation.stl_2
