ronheywood/PiTrac/3D Printed Parts/Enclosure Version 2/Tower-Connector-Board-Variant/Tower.FCStd

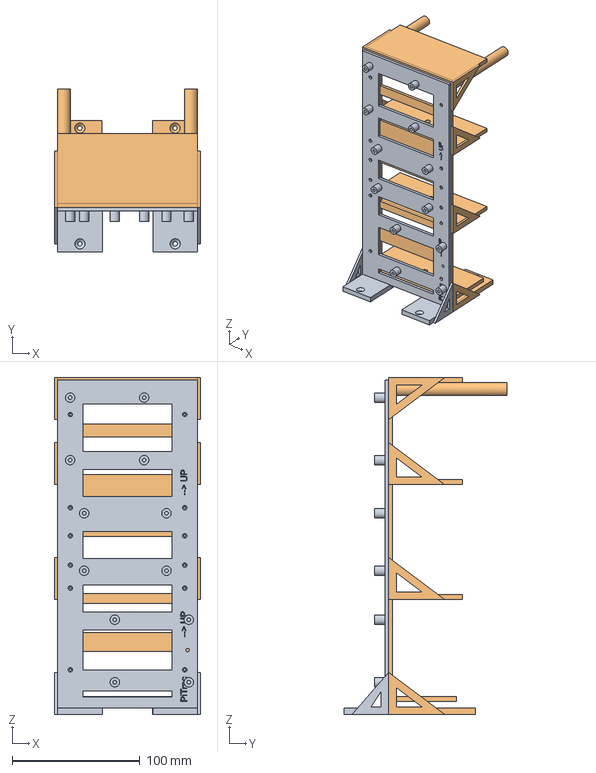
[picture p89: CAD file, 2025-06-27]
3D Printed Parts/Enclosure Version 2/Tower-Connector-Board-Variant/Tower.FCStd
114.7 x 127.7 x 264.0 mm
Backplate Body - Connector Board Variant
Frontplate Body (same as other variant)
