ronheywood/PiTrac/3D Printed Parts/Enclosure Models/Logo Badge/PiTrac Logo-Logo - Back Plate Object.stl

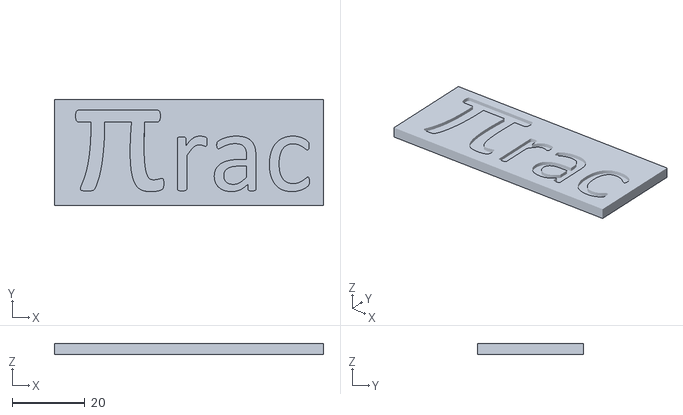
[picture p90: CAD file, 2025-01-06]
3D Printed Parts/Enclosure Models/Logo Badge/PiTrac Logo-Logo - Back Plate Object.stl
73.9 x 29.2 x 3.00
