ronheywood/PiTrac/3D Printed Parts/Enclosure Version 2/BaseBox/BaseBox-Shank Shield Body.dxf

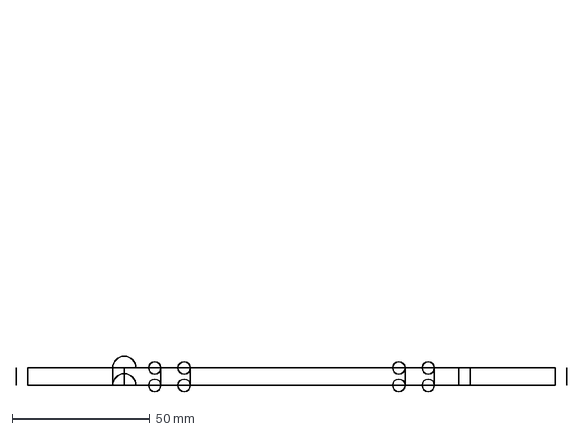
[picture p91: CAD file, 2025-06-30]
3D Printed Parts/Enclosure Version 2/BaseBox/BaseBox-Shank Shield Body.dxf
200.0 x 136.3 mm
