ronheywood/PiTrac/3D Printed Parts/Enclosure Version 2/Calibration Rig/Calibration Rig - Pieces Laid Out.stl

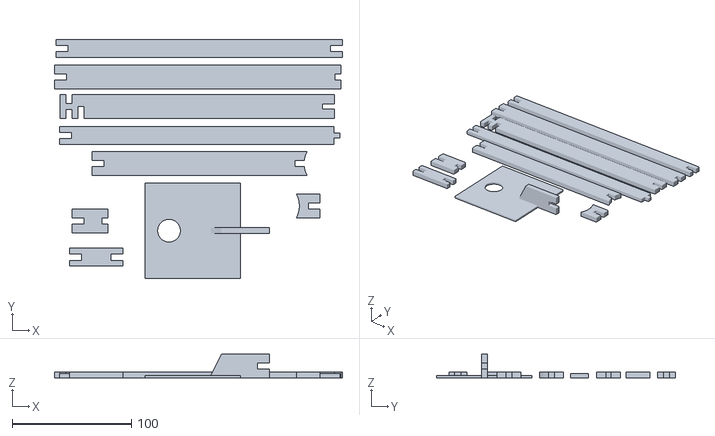
[picture p92: CAD file, 2025-06-13]
3D Printed Parts/Enclosure Version 2/Calibration Rig/Calibration Rig - Pieces Laid Out.stl
241.1 x 200.0 x 20.0
