ronheywood/PiTrac/3D Printed Parts/Enclosure Version 2/Pi-Camera-Light-Filter-Holder - M12/Pi Cam Filter Holder - M12 Lens.3mf

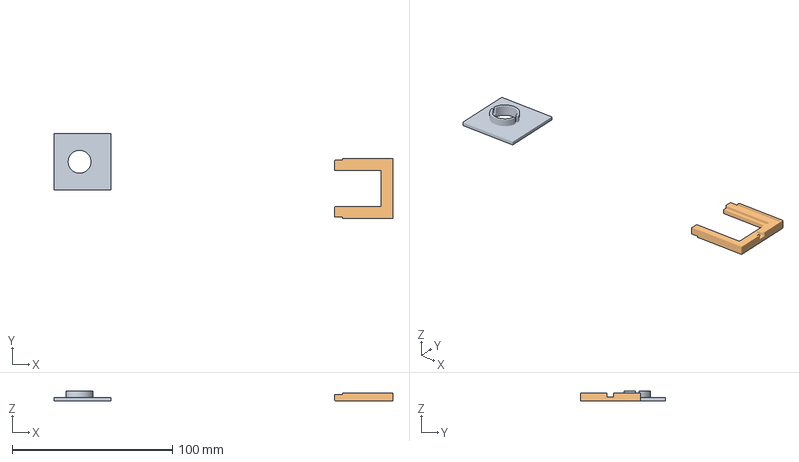
[picture p95: CAD file, 2025-07-09]
3D Printed Parts/Enclosure Version 2/Pi-Camera-Light-Filter-Holder - M12/Pi Cam Filter Holder - M12 Lens.3mf
211.7 x 53.3 x 6.00 mm
Pi Cam Filter Holder - M12 Lens.stl_1
Pi Cam Filter Holder - M12 Lens.stl_2
