ronheywood/PiTrac/3D Printed Parts/Enclosure Version 2/Pi-Camera-Mounts - Innomaker CAM-IMX296/Camera Mount - Top Variation - Both Parts Separated.stl

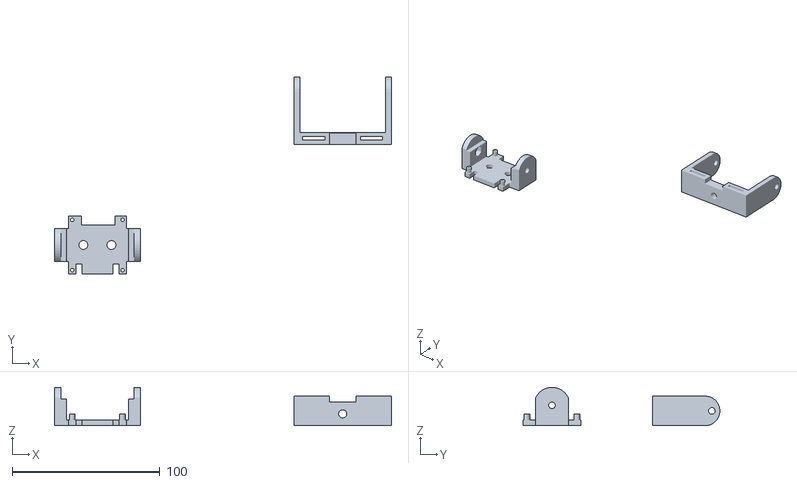
[picture p96: CAD file, 2025-06-30]
3D Printed Parts/Enclosure Version 2/Pi-Camera-Mounts - Innomaker CAM-IMX296/Camera Mount - Top Variation - Both Parts Separated.stl
227.8 x 133.0 x 25.9
