ronheywood/PiTrac/3D Printed Parts/Enclosure Version 2/Tower-Connector-Board-Variant/Tower Frontplate Body.stl

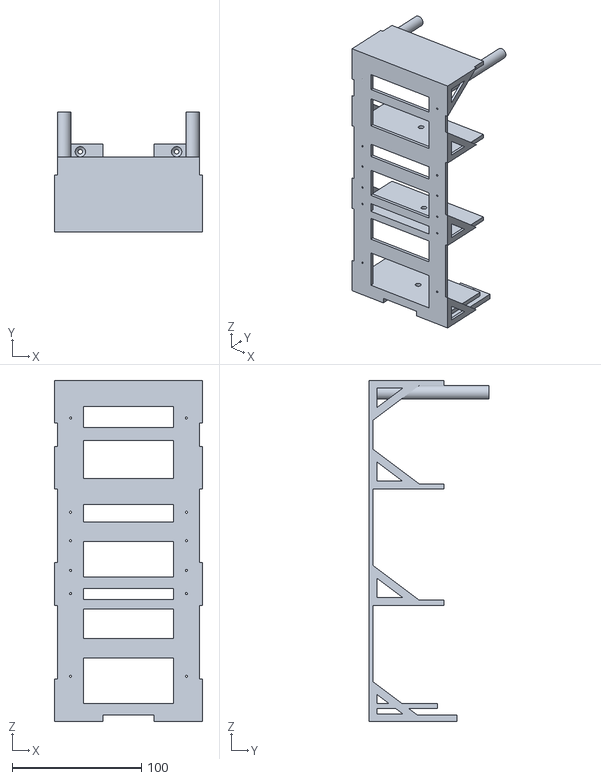
[picture p98: CAD file, 2025-06-27]
3D Printed Parts/Enclosure Version 2/Tower-Connector-Board-Variant/Tower Frontplate Body.stl
114.6 x 92.7 x 264.0
