ronheywood/PiTrac/3D Printed Parts/Enclosure Models/Combined Enclosure Model (DO NOT PRINT)/Pi HQ Camera.FCStd

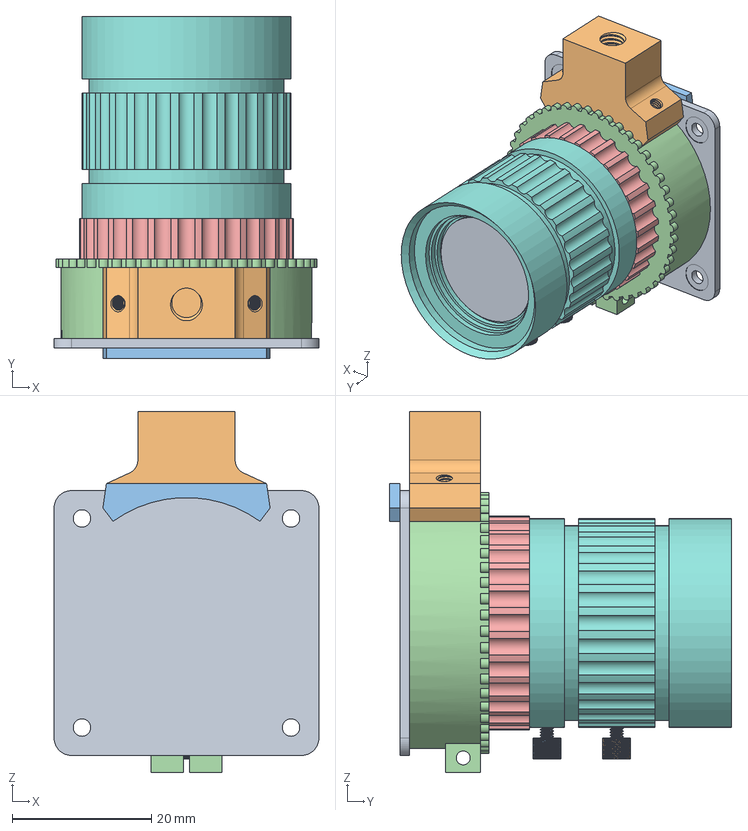
[picture p99: CAD file, 2025-01-06]
3D Printed Parts/Enclosure Models/Combined Enclosure Model (DO NOT PRINT)/Pi HQ Camera.FCStd
38.0 x 49.1 x 51.8 mm
Raspberry Pi HQ Camera with cs mount lens v3
Raspberry Pi HQ Camera with cs mount lens v004
Raspberry Pi HQ Camera with cs mount lens v005
Raspberry Pi HQ Camera with cs mount lens v006
Raspberry Pi HQ Camera with cs mount lens v007
Raspberry Pi HQ Camera with cs mount lens v008
Raspberry Pi HQ Camera with cs mount lens v009
Raspberry Pi HQ Camera with cs mount lens v010
Raspberry Pi HQ Camera with cs mount lens v011
Raspberry Pi HQ Camera with cs mount lens v012
Raspberry Pi HQ Camera with cs mount lens v013
