ronheywood/PiTrac/3D Printed Parts/Enclosure Models/Logo Badge/PiTrac Logo.FCStd

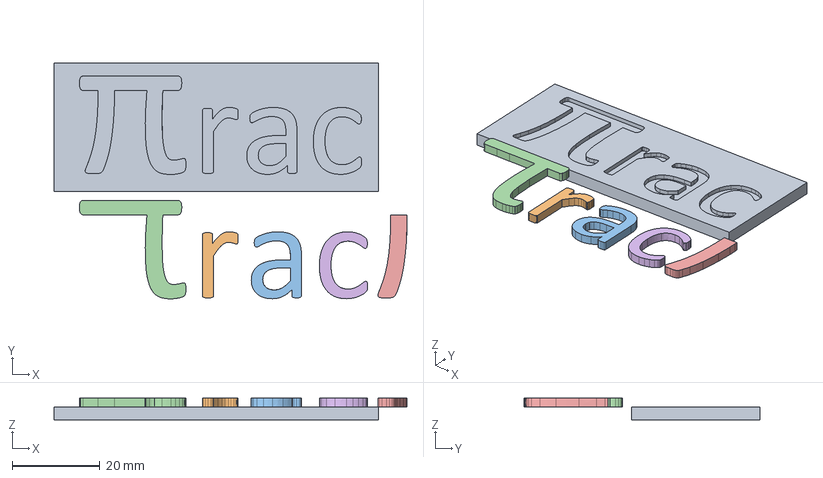
[picture p100: CAD file, 2024-12-17]
3D Printed Parts/Enclosure Models/Logo Badge/PiTrac Logo.FCStd
80.3 x 53.6 x 5.00 mm
Logo - Back Plate Body
r Character
a Character Body
Pi Character
Pi Stem Body
c Body
