ronheywood/PiTrac/3D Printed Parts/Enclosure Version 2/BaseBox/BaseBox- Light Shield Body.3mf

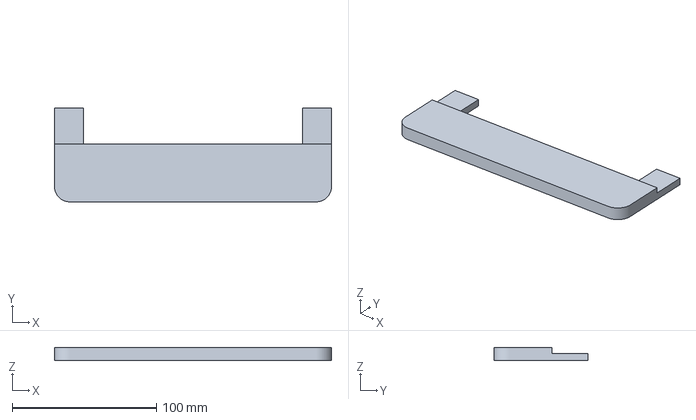
[picture p101: CAD file, 2025-06-26]
3D Printed Parts/Enclosure Version 2/BaseBox/BaseBox- Light Shield Body.3mf
192.0 x 65.0 x 9.00 mm
