ronheywood/PiTrac/3D Printed Parts/Enclosure Version 2/CaseCover/UpperCase Cover Body.3mf

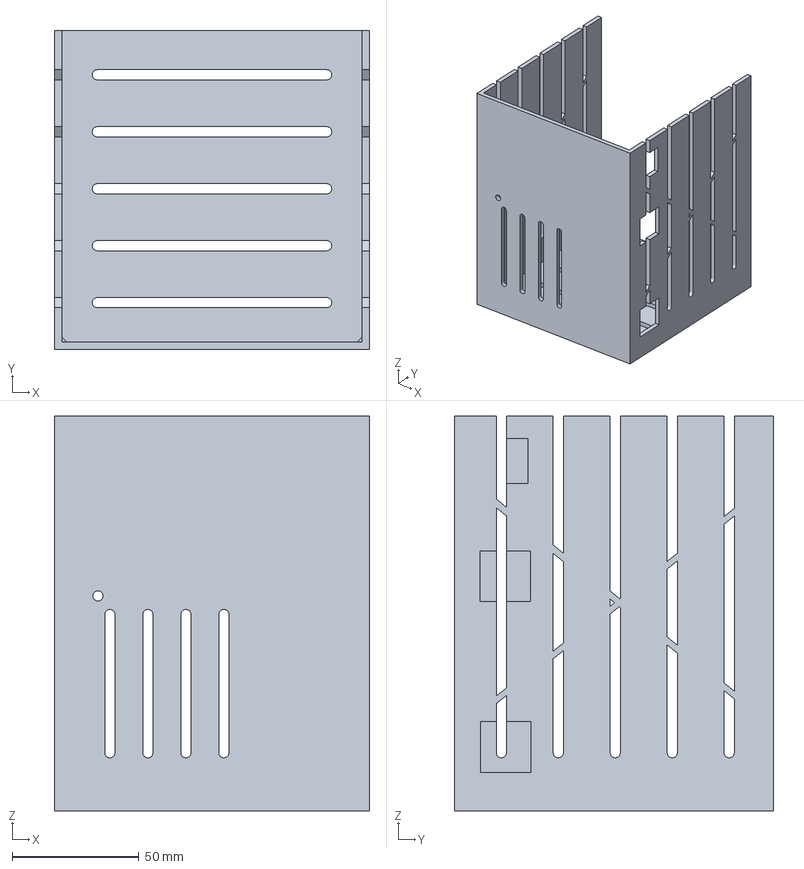
[picture p102: CAD file, 2025-04-07]
3D Printed Parts/Enclosure Version 2/CaseCover/UpperCase Cover Body.3mf
124.6 x 126.0 x 156.0 mm
