ronheywood/PiTrac/3D Printed Parts/Enclosure Version 2/Integrated Enclosure (DO NOT PRINT)/Cree LED Lens.FCStd

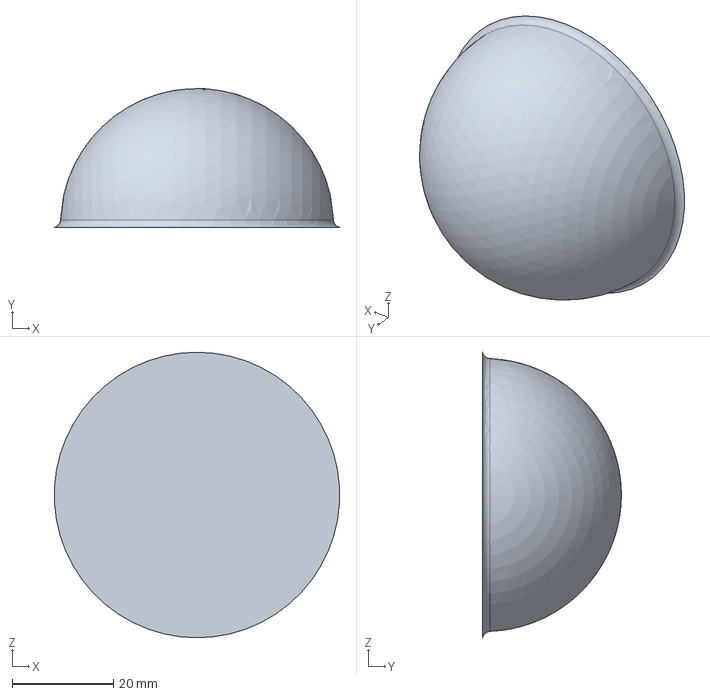
[picture p103: CAD file, 2025-03-30]
3D Printed Parts/Enclosure Version 2/Integrated Enclosure (DO NOT PRINT)/Cree LED Lens.FCStd
56.3 x 27.4 x 56.4 mm
