ronheywood/PiTrac/3D Printed Parts/Enclosure Version 2/Pi-Camera-Light-Filter-Holder - M12/Pi Cam Filter Holder - M12.FCStd

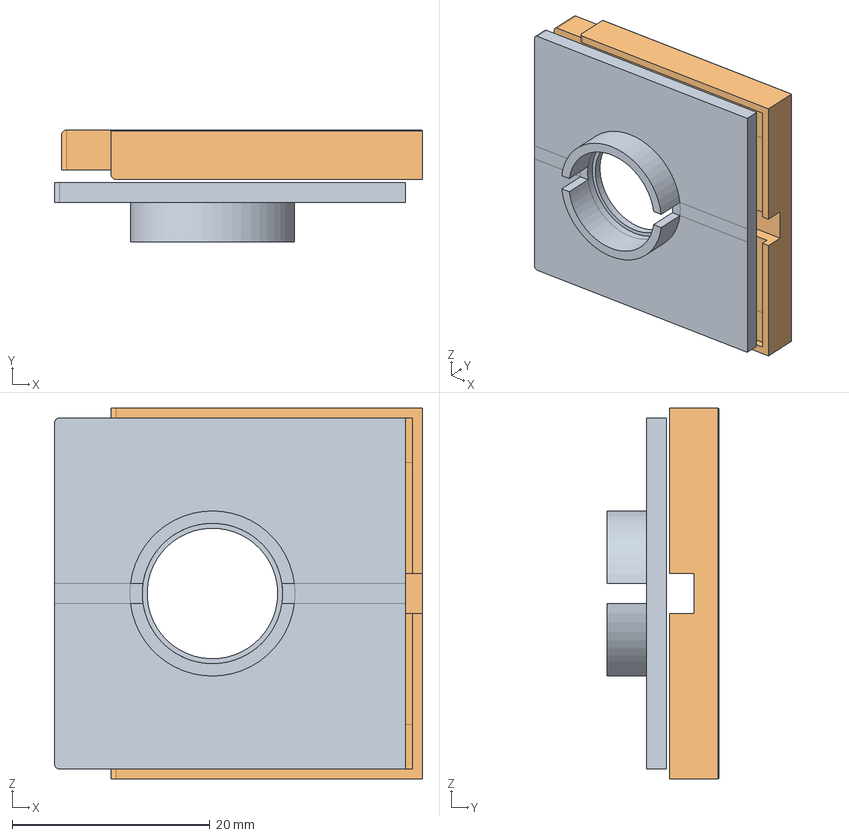
[picture p104: CAD file, 2025-07-09]
3D Printed Parts/Enclosure Version 2/Pi-Camera-Light-Filter-Holder - M12/Pi Cam Filter Holder - M12.FCStd
37.2 x 11.3 x 37.5 mm
Filter Holder Body
Holder Wings Body
