ronheywood/PiTrac/3D Printed Parts/Enclosure Version 2/Pi-Camera-Mounts - Innomaker CAM-IMX296/Camera Mount - Innomaker Bottom.FCStd

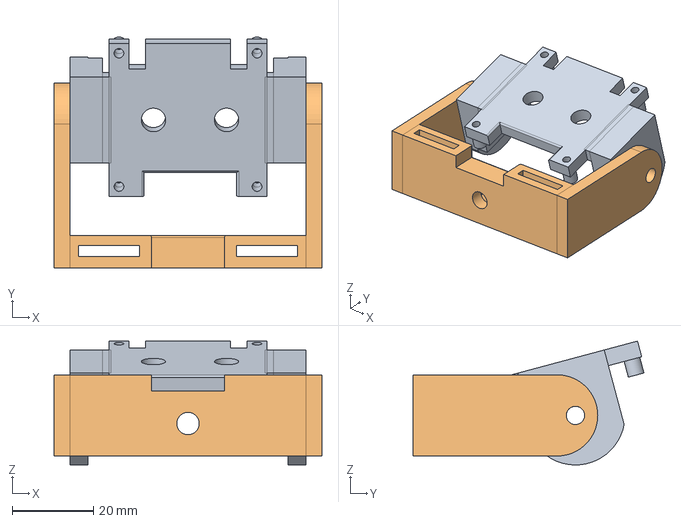
[picture p105: CAD file, 2025-06-30]
3D Printed Parts/Enclosure Version 2/Pi-Camera-Mounts - Innomaker CAM-IMX296/Camera Mount - Innomaker Bottom.FCStd
66.0 x 56.9 x 30.5 mm
Back Plate Body
Gimbal Base Body
