ronheywood/PiTrac/3D Printed Parts/Enclosure Version 2/Tower-Connector-Board-Variant/Tower Frontplate Body - Connector Board Variant - Split Pieces.3mf

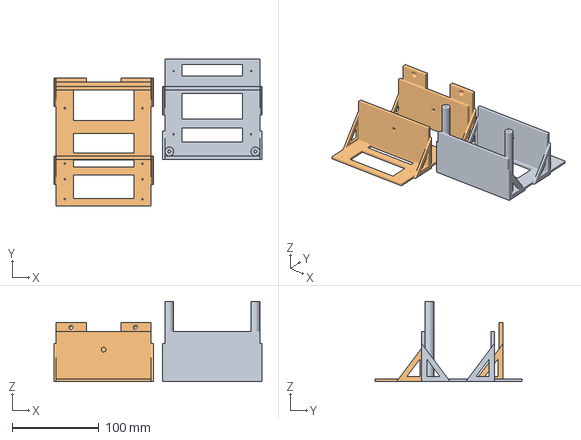
[picture p107: CAD file, 2025-06-27]
3D Printed Parts/Enclosure Version 2/Tower-Connector-Board-Variant/Tower Frontplate Body - Connector Board Variant - Split Pieces.3mf
240.2 x 169.9 x 92.6 mm
Tower Frontplate Body.stl x 2
