ronheywood/PiTrac/3D Printed Parts/Enclosure Version 2/Tower/Tower Frontplate - (Both Pieces - split).3mf

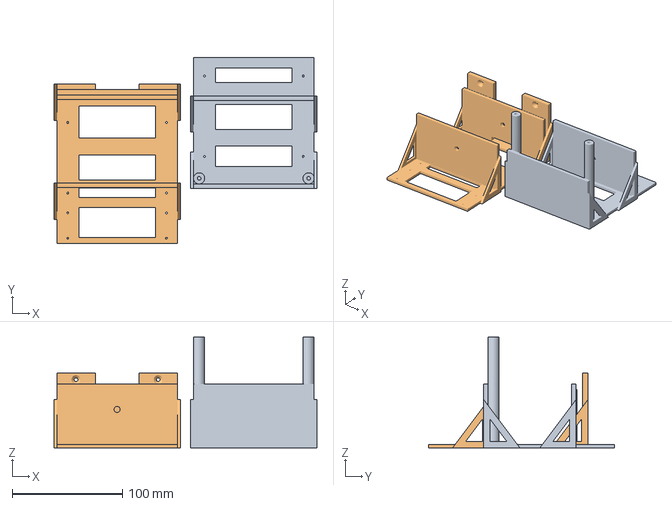
[picture p108: CAD file, 2025-06-20]
3D Printed Parts/Enclosure Version 2/Tower/Tower Frontplate - (Both Pieces - split).3mf
238.7 x 169.2 x 100.7 mm
Tower Frontplate Body.stl x 2
