ronheywood/PiTrac/3D Printed Parts/Enclosure Models/Combined Enclosure Model (DO NOT PRINT)/PiTrac - Combined Parts.FCStd

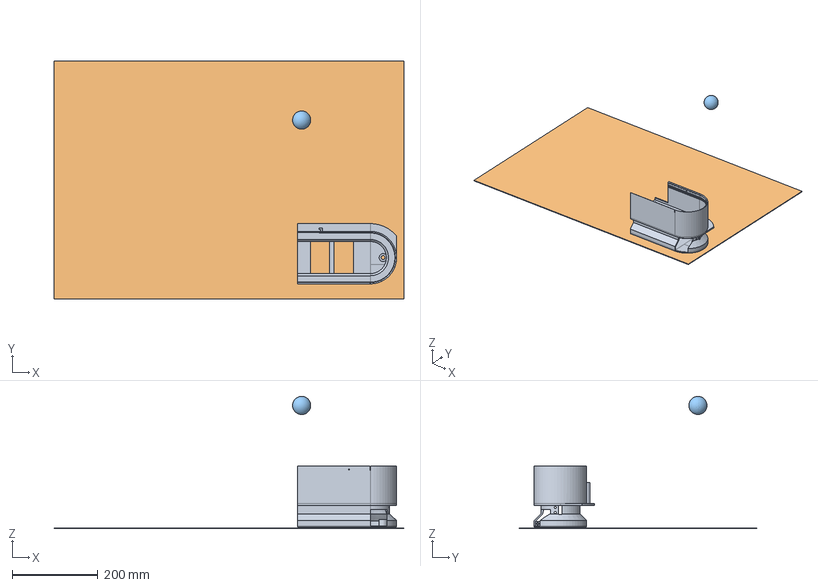
[picture p109: CAD file, 2025-01-06]
3D Printed Parts/Enclosure Models/Combined Enclosure Model (DO NOT PRINT)/PiTrac - Combined Parts.FCStd
818.6 x 555.6 x 309.5 mm
Wall 1 - Power Side Body Mirror
Ground Body
