ronheywood/PiTrac/3D Printed Parts/Enclosure Version 2/Integrated Enclosure (DO NOT PRINT)/LRS-150 Meanwell.FCStd

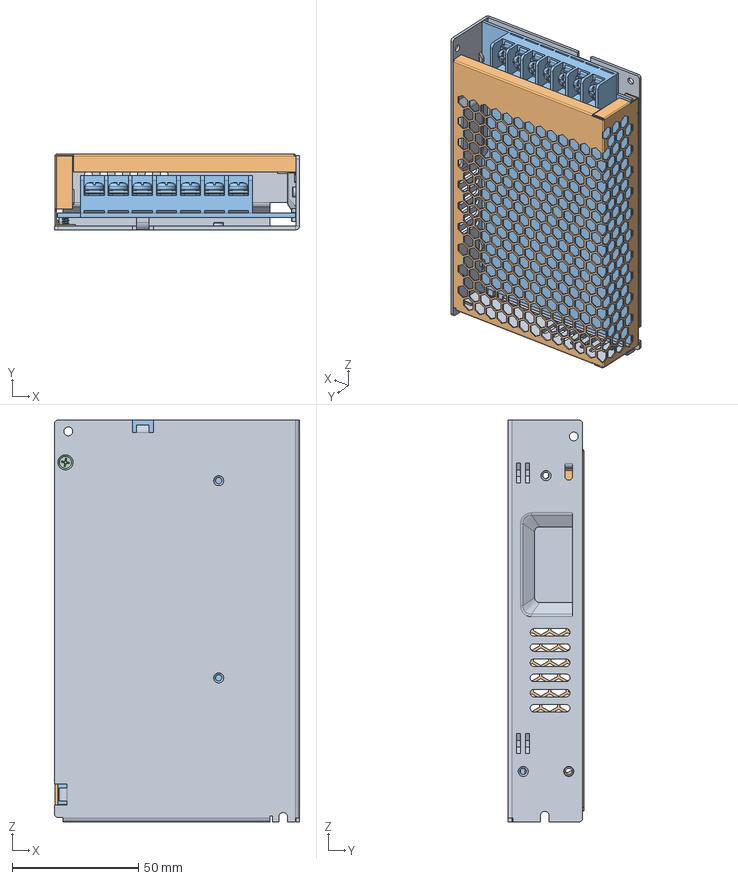
[picture p110: CAD file, 2025-03-30]
3D Printed Parts/Enclosure Version 2/Integrated Enclosure (DO NOT PRINT)/LRS-150 Meanwell.FCStd
97.0 x 30.0 x 159.0 mm
LRS-150
LRS-151
LRS-152
LRS-153
