ronheywood/PiTrac/3D Printed Parts/Enclosure Version 2/Pi-Camera-Mounts - Innomaker CAM-IMX296/Camera Mount - Innomaker Top.FCStd

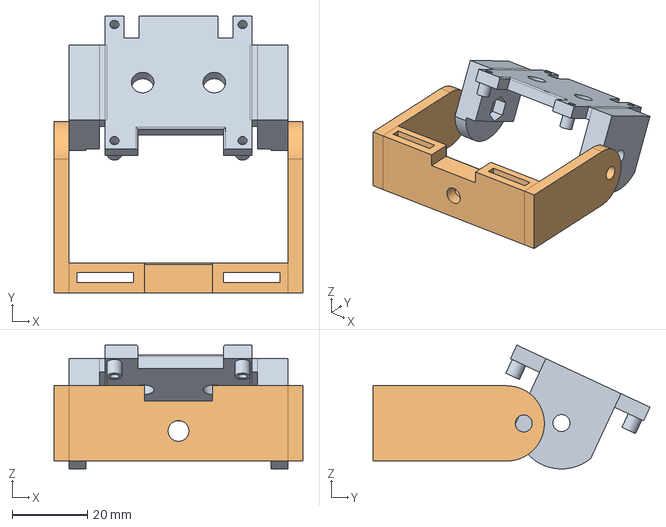
[picture p111: CAD file, 2025-06-30]
3D Printed Parts/Enclosure Version 2/Pi-Camera-Mounts - Innomaker CAM-IMX296/Camera Mount - Innomaker Top.FCStd
66.0 x 73.5 x 32.9 mm
Back Plate Body
Gimbal Base Body
