ronheywood/PiTrac/3D Printed Parts/Enclosure Version 2/Tower-Connector-Board-Variant/Tower Backplate Body - Connector Board Variant - Split Pieces.3mf

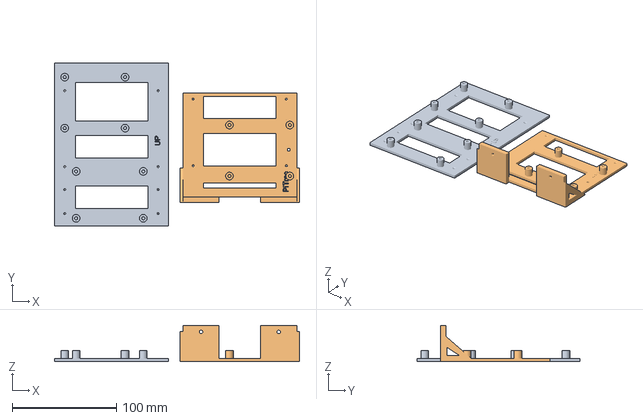
[picture p113: CAD file, 2025-06-27]
3D Printed Parts/Enclosure Version 2/Tower-Connector-Board-Variant/Tower Backplate Body - Connector Board Variant - Split Pieces.3mf
235.4 x 157.0 x 35.0 mm
Tower Backplate Body.stl x 2
