ronheywood/PiTrac/3D Printed Parts/Enclosure Version 2/Tower/Tower Backplate Body (Split Parts).stl

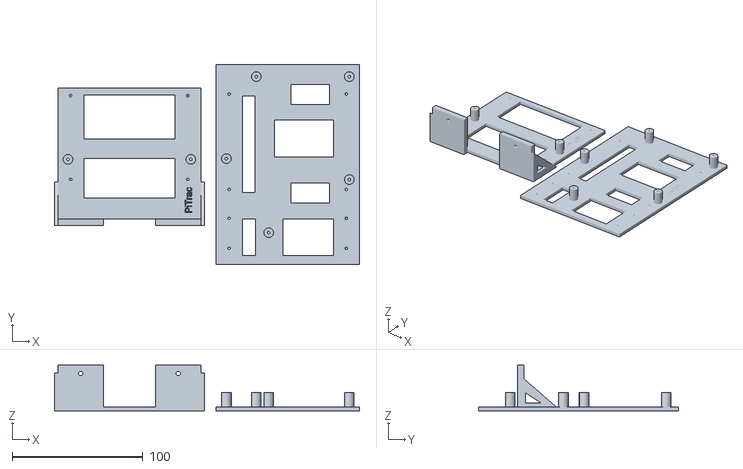
[picture p114: CAD file, 2025-06-20]
3D Printed Parts/Enclosure Version 2/Tower/Tower Backplate Body (Split Parts).stl
233.3 x 152.6 x 35.0
