ronheywood/PiTrac/3D Printed Parts/Enclosure Models/Combined Enclosure Model (DO NOT PRINT)/Camera Mount Top v1.0.FCStd

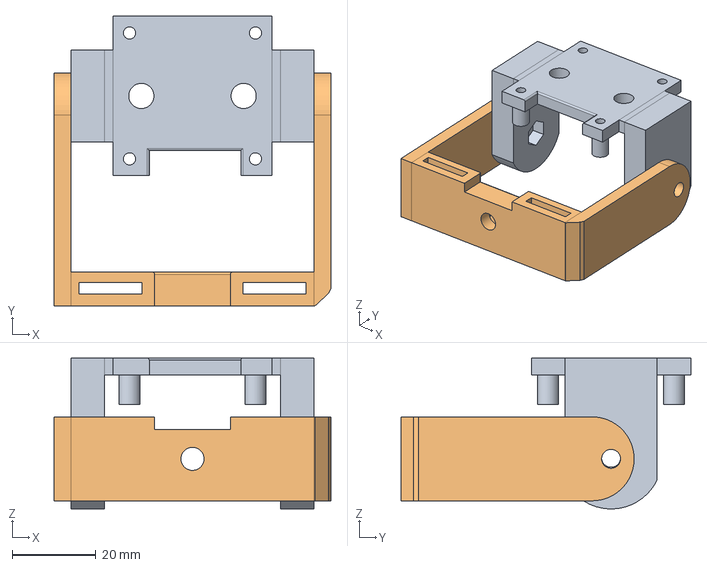
[picture p115: CAD file, 2025-01-06]
3D Printed Parts/Enclosure Models/Combined Enclosure Model (DO NOT PRINT)/Camera Mount Top v1.0.FCStd
66.0 x 69.0 x 35.9 mm
BackPlate001
Gimbal
