ronheywood/PiTrac/3D Printed Parts/Enclosure Version 2/BaseBox/BaseBox-End Cap.3mf

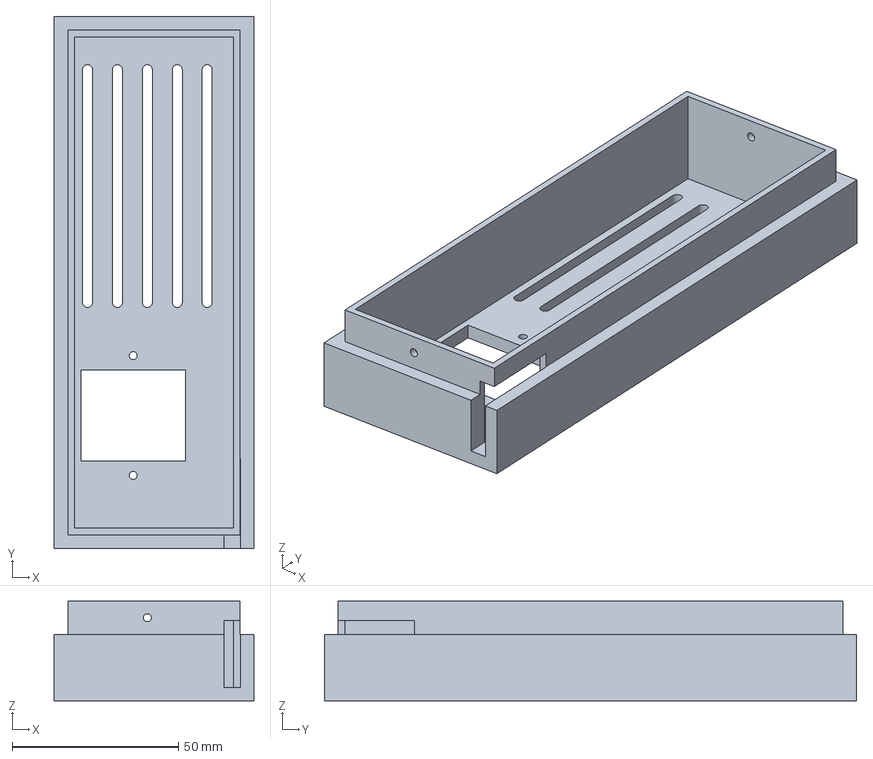
[picture p116: CAD file, 2025-06-26]
3D Printed Parts/Enclosure Version 2/BaseBox/BaseBox-End Cap.3mf
60.0 x 160.0 x 30.0 mm
