ronheywood/PiTrac/3D Printed Parts/Enclosure Version 2/Pi-Camera-Mounts - Innomaker CAM-IMX296/Camera Mount - Top Variation.3mf

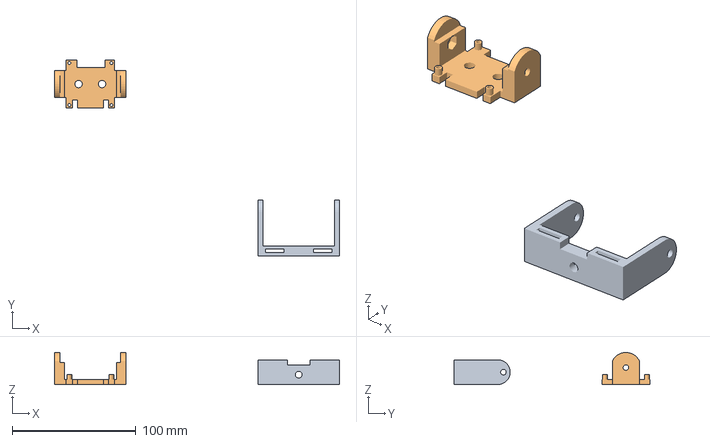
[picture p117: CAD file, 2025-06-27]
3D Printed Parts/Enclosure Version 2/Pi-Camera-Mounts - Innomaker CAM-IMX296/Camera Mount - Top Variation.3mf
230.6 x 158.6 x 25.9 mm
Camera Mount - Top Variation.stl_1
Camera Mount - Top Variation.stl_2
