ronheywood/PiTrac/3D Printed Parts/Enclosure Version 2/Integrated Enclosure (DO NOT PRINT)/Cree LED.FCStd

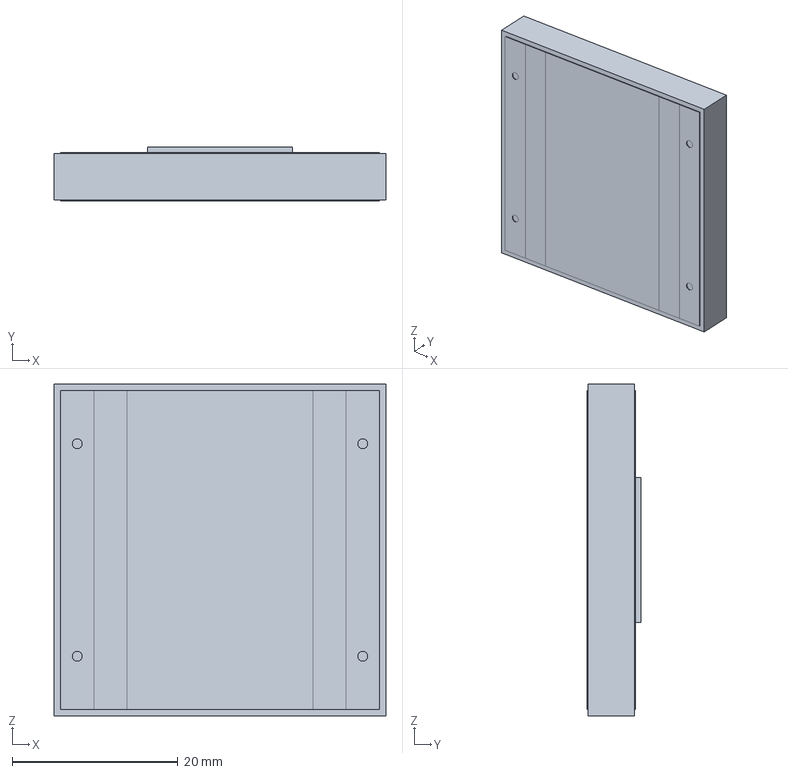
[picture p119: CAD file, 2025-01-06]
3D Printed Parts/Enclosure Version 2/Integrated Enclosure (DO NOT PRINT)/Cree LED.FCStd
40.0 x 6.52 x 40.0 mm
