ronheywood/PiTrac/3D Printed Parts/Enclosure Version 2/Pi-Camera-Mounts - Innomaker CAM-IMX296/Camera Mount - Bottom Variation.3mf

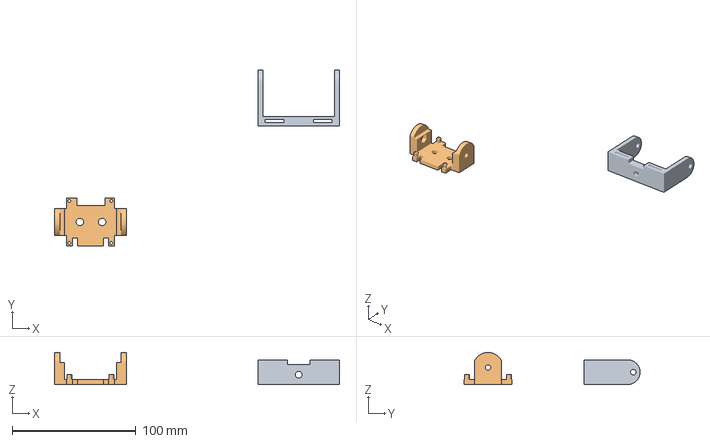
[picture p120: CAD file, 2025-06-26]
3D Printed Parts/Enclosure Version 2/Pi-Camera-Mounts - Innomaker CAM-IMX296/Camera Mount - Bottom Variation.3mf
230.3 x 142.4 x 25.9 mm
Camera Mount - Bottom Variation.stl_1
Camera Mount - Bottom Variation.stl_2
