ronheywood/PiTrac/3D Printed Parts/Enclosure Models/Combined Enclosure Model (DO NOT PRINT)/Camera Mount - Bottom.FCStd

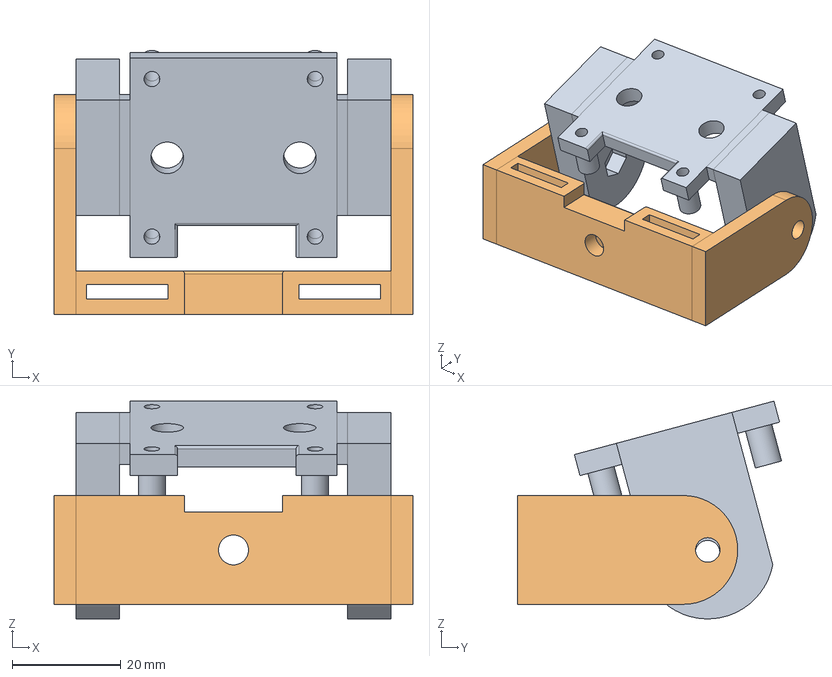
[picture p121: CAD file, 2025-01-06]
3D Printed Parts/Enclosure Models/Combined Enclosure Model (DO NOT PRINT)/Camera Mount - Bottom.FCStd
66.0 x 48.6 x 40.0 mm
BackPlate Body
Gimbal
