ronheywood/PiTrac/3D Printed Parts/Enclosure Version 2/BaseBox/C14 Panel Mount Power Plug Adapter.FCStd

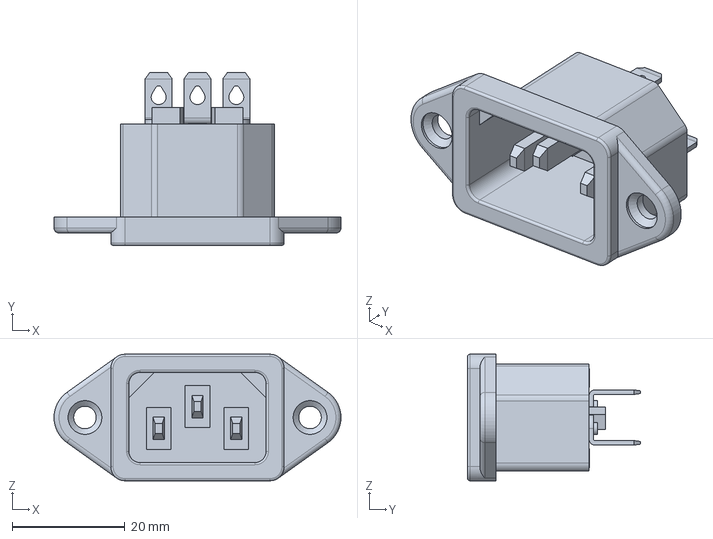
[picture p122: CAD file, 2025-03-30]
3D Printed Parts/Enclosure Version 2/BaseBox/C14 Panel Mount Power Plug Adapter.FCStd
51.0 x 30.7 x 22.5 mm
