ronheywood/PiTrac/3D Printed Parts/Enclosure Version 2/BaseBox/CaseCover-BaseBox Part.stl

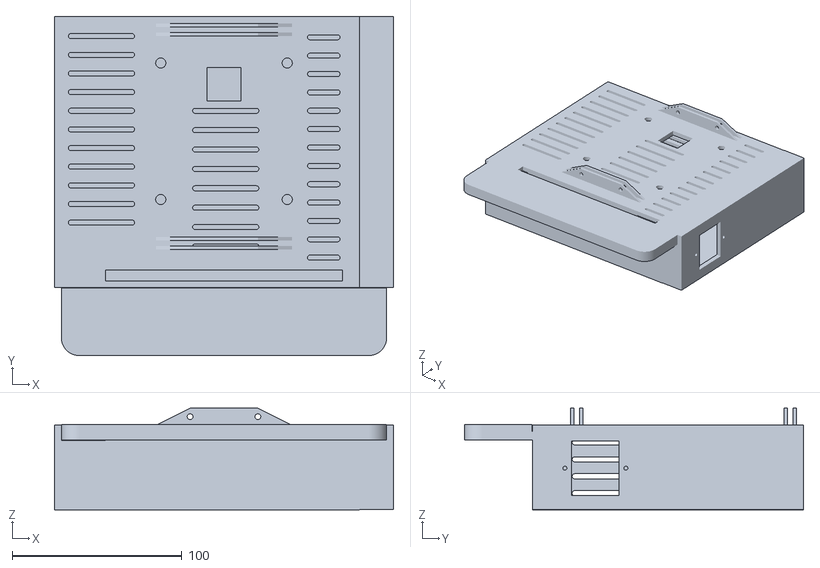
[picture p123: CAD file, 2025-03-30]
3D Printed Parts/Enclosure Version 2/BaseBox/CaseCover-BaseBox Part.stl
200.0 x 200.1 x 60.0
