ronheywood/PiTrac/3D Printed Parts/Enclosure Models/Combined Enclosure Model (DO NOT PRINT)/Connector Board.FCStd

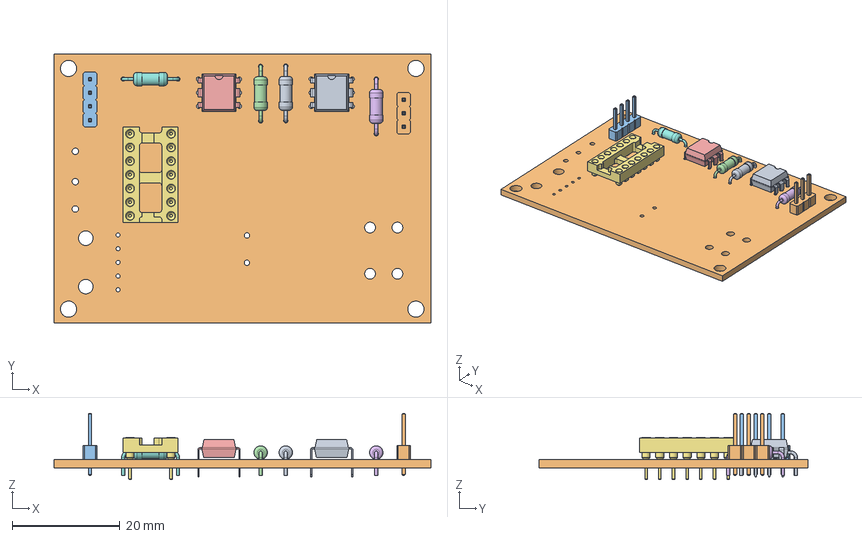
[picture p124: CAD file, 2025-01-06]
3D Printed Parts/Enclosure Models/Combined Enclosure Model (DO NOT PRINT)/Connector Board.FCStd
70.0 x 50.0 x 12.3 mm
DIP-6_W7.62mm
PinHeader_1x03_P254mm_Vertical
PinHeader_1x04_P254mm_Vertical
R_Axial_DIN0207_L63mm_D25mm_P1016mm_Horizontal
DIP-6_W7.62mm002
R_Axial_DIN0207_L63mm_D25mm_P1016mm_Horizontal001
DIP_14_W762mm_Socket
R_Axial_DIN0207_L63mm_D25mm_P1016mm_Horizontal002
R_Axial_DIN0207_L63mm_D25mm_P1016mm_Horizontal003
GolfSim Connector Board PCB
