ronheywood/PiTrac/3D Printed Parts/Enclosure Models/Combined Enclosure Model (DO NOT PRINT)/Front View - Combined 3D Model.png

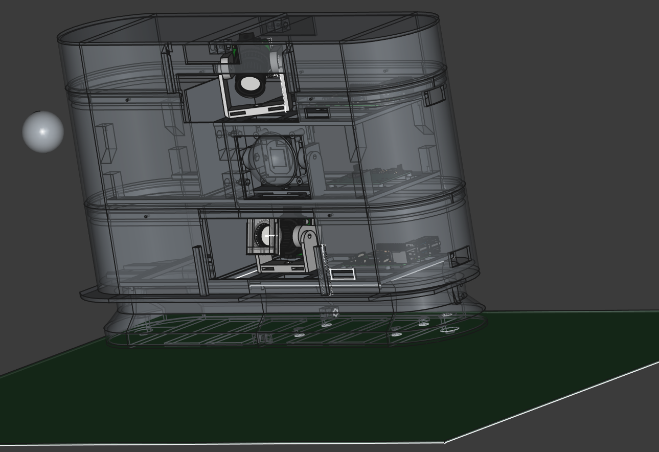
3D Printed Parts/Enclosure Models/Combined Enclosure Model (DO NOT PRINT)/Front View - Combined 3D Model.png
