ronheywood/PiTrac/3D Printed Parts/Enclosure Models/Middle Layer - Pi Side - Wall/Middle Layer - Pi Side - Wall - Printed Part with Bottom Floor.png

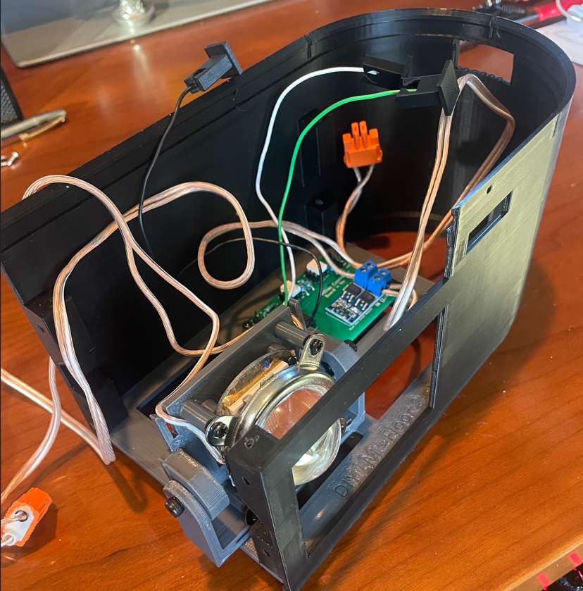
3D Printed Parts/Enclosure Models/Middle Layer - Pi Side - Wall/Middle Layer - Pi Side - Wall - Printed Part with Bottom Floor.png
