ronheywood/PiTrac/Software/LMSourceCode/Testing/TestSuite_2025_02_07/comparison template.csv

Shot ID |  | Comparison (Uneekor value minus PiTrac) |  |  |  |  | System Data
Ball | PiTrac Shot | Speed ? (mph) | VLA ? | HLA ?° | Back Spin ? (rpm) | Side Spin ? (rpm) | Uneekor Speed | PiTrac Speed | Uneekor VLA° | PiTrac VLA° | Uneekor HLA° | PiTrac HLA° | Uneekor Back Spin | PiTrac Back Spin | Uneekor Side Spin | PiTrac Side Spin | Ball ID Picture | Spin Ball 1 | Spin Ball 2 | Test Result Ball | Notes
11:03:17 | 2 | 3.0 | 0.0 | -1.2 | 99 | 41 | 66.6 | 63.6 | 19.1 | 19.1 | -5.6 | -4.4 | 3987 | 3888 | -355 | -396 |  | Fixed
11:04:27 | 4 | -0.5 | -1.5 | -0.9 | 179 | -1206 | 54.5 | 55.0 | 10.9 | 12.4 | -4.0 | -3.1 | 1686 | 1507 | -1048 | 158 |  | Fixed |  |  | Uneekor's side spin appears incorrect.
11:05:14 | 6 | 2.4 | -1.0 | -1.7 | 52 | -2143 | 70.2 | 70.2 | 9.9 | 10.9 | -4.4 | -2.7 | 3226 | 3174 | -953 | 1190 |  |  |  |  | Uneekor's side spin appears incorrect.
11:05:43 | 7 | 5.1 | -1.1 | -5.0 | 783 | 294 | 75.3 | 70.2 | 18.5 | 19.6 | -6.9 | -1.9 | 4880 | 4097 | -85 | -379 |  | Final Fixed
11:06:19 | 8 | 5.0 | -0.5 | -4.8 | 672 | 1043 | 78.7 | 73.7 | 18.7 | 19.2 | -5.1 | -0.3 | 4507 | 3835 | -279 | -1322
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
