ronheywood/PiTrac/Software/CalibrateCameraDistortions/caliResult1.png

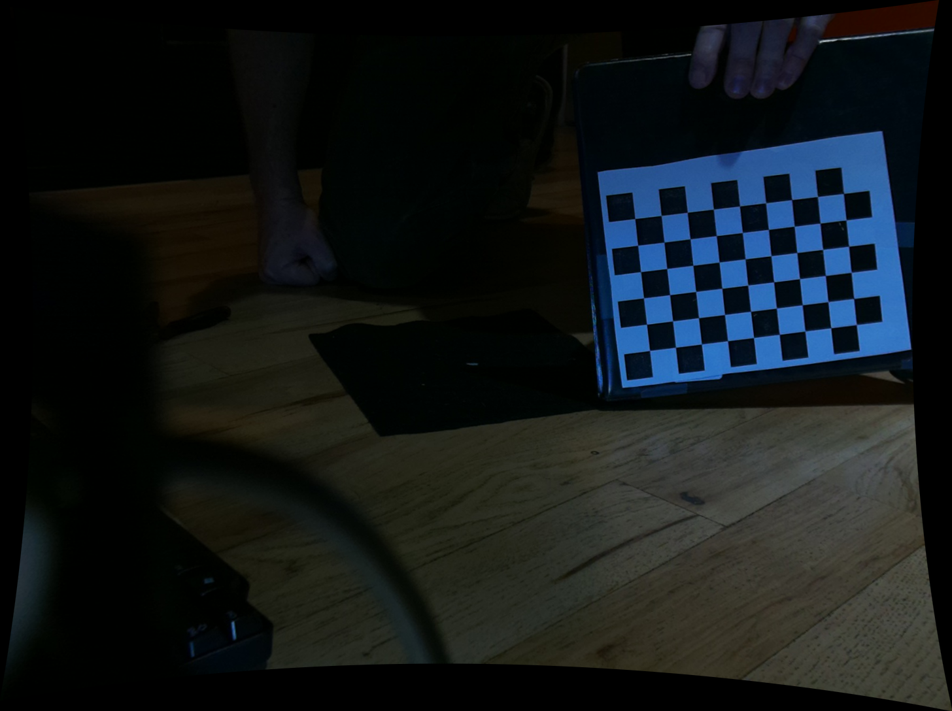
Software/CalibrateCameraDistortions/caliResult1.png
