ronheywood/PiTrac/Software/CalibrateCameraDistortions/caliResult2.png

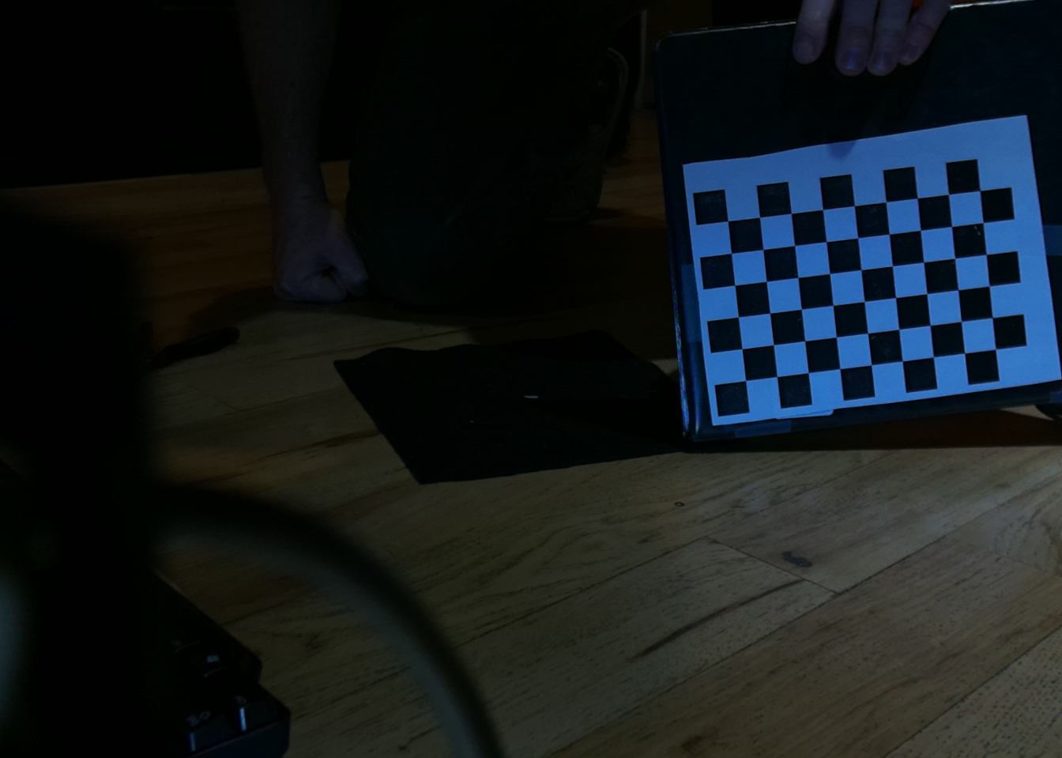
Software/CalibrateCameraDistortions/caliResult2.png
