ronheywood/PiTrac/Software/LMSourceCode/Testing/TestSuite_2025_02_07/gs_log_img__log_ball_final_found_ball_img_Shot_2_2025-Feb-07_11.04.38.png

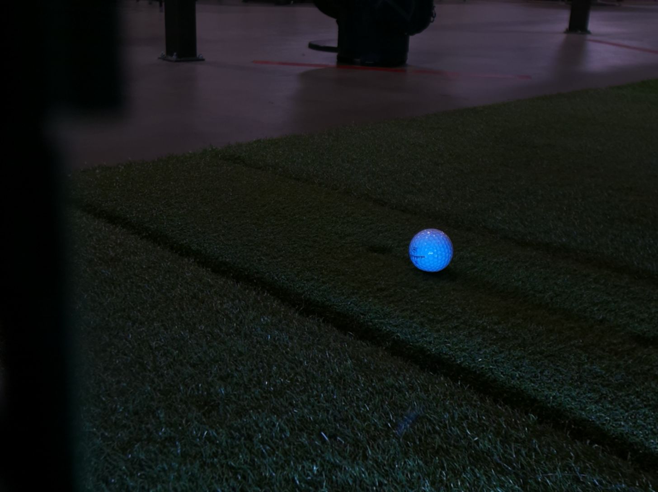
Software/LMSourceCode/Testing/TestSuite_2025_02_07/gs_log_img__log_ball_final_found_ball_img_Shot_2_2025-Feb-07_11.04.38.png
