ronheywood/PiTrac/Software/CalibrateCameraDistortions/images/ProblemPix/gs_calibation_3.png

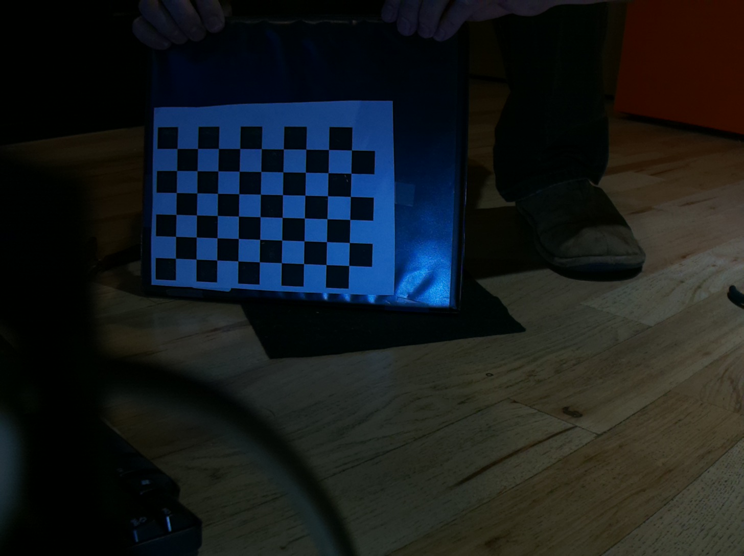
Software/CalibrateCameraDistortions/images/ProblemPix/gs_calibation_3.png
