ronheywood/PiTrac/Software/CalibrateCameraDistortions/images/ProblemPix/gs_calibation_5.png

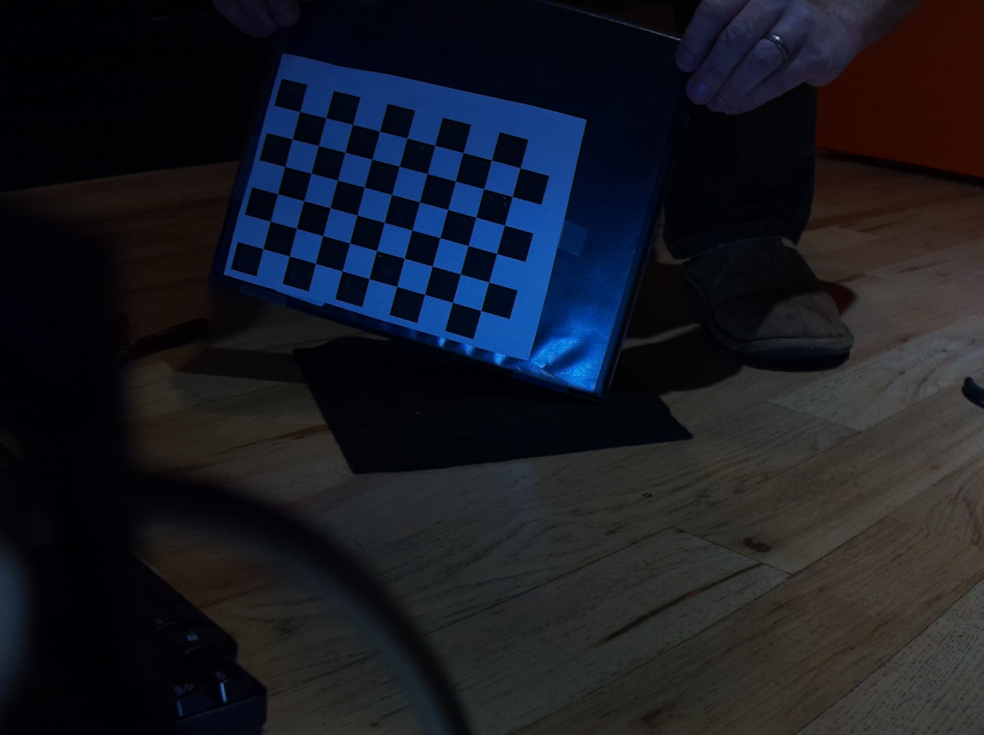
Software/CalibrateCameraDistortions/images/ProblemPix/gs_calibation_5.png
