ronheywood/PiTrac/Software/LMSourceCode/ImageProcessing/gs_camera.cpp

/* SPDX-License-Identifier: GPL-2.0-only */
/*
 * Copyright (C) 2022-2025, Verdant Consultants, LLC.
 */

#include <algorithm>

#include "gs_options.h"
#include "ball_image_proc.h"
#include "pulse_strobe.h"
#include "gs_ui_system.h"
#include "gs_config.h"
#include "gs_clubs.h"

#include "libcamera_interface.h"

#include "gs_camera.h"


namespace golf_sim {

    // Constants used by this class
    bool GolfSimCamera::kLogIntermediateExposureImagesToFile = false;
    bool GolfSimCamera::kLogWebserverImagesToFile = true;
    bool GolfSimCamera::kLogDiagnosticImagesToUniqueFiles = false;
    
    int GolfSimCamera::kMaximumOffTrajectoryDistance = 5;
    unsigned int GolfSimCamera::kNumberHighQualityBallsToRetain = 2;
    double GolfSimCamera::kMaxStrobedBallColorDifferenceRelaxed = 35000.;
    double GolfSimCamera::kMaxPuttingBallColorDifferenceRelaxed = 35000.;
    double GolfSimCamera::kMaxStrobedBallColorDifferenceStrict = 15000.;
    double GolfSimCamera::kBallProximityMarginPercentRelaxed = 50.;
    double GolfSimCamera::kBallProximityMarginPercentStrict = 5.;

    // These constants may be used before this class's constructor is called.
    // For that reason, they are initialized in the GsConfiguration startup
    cv::Vec3d GolfSimCamera::kCamera1PositionsFromExpectedBallMeters;
    cv::Vec3d GolfSimCamera::kCamera2PositionsFromExpectedBallMeters;
    cv::Vec3d GolfSimCamera::kCamera2OffsetFromCamera1OriginMeters;

    double GolfSimCamera::kColorDifferenceRgbPostMultiplierForDarker = 5.0;
    double GolfSimCamera::kColorDifferenceRgbPostMultiplierForLighter = 10.0;
    double GolfSimCamera::kColorDifferenceStdPostMultiplierForDarker = 3.0;
    double GolfSimCamera::kColorDifferenceStdPostMultiplierForLighter = 2.0;

    double GolfSimCamera::kMaxDistanceFromTrajectory = 20.;

    int GolfSimCamera::kClosestBallPairEdgeBackoffPixels = 200;

    double GolfSimCamera::kMaxIntermediateBallRadiusChangePercent = 10.0;
    double GolfSimCamera::kMaxPuttingIntermediateBallRadiusChangePercent = 10.0;
    double GolfSimCamera::kMaxOverlappedBallRadiusChangeRatio = 1.3;
    double GolfSimCamera::kMaxRadiusDifferencePercentageFromBest = 20;

    bool GolfSimCamera::kUsePreImageSubtraction = false;  // Ultimately, this concept was not as helpful as hoped for
    double GolfSimCamera::kPreImageWeightingOverall = 1.0;
    double GolfSimCamera::kPreImageWeightingBlue = 1.0;
    double GolfSimCamera::kPreImageWeightingGreen = 1.0;
    double GolfSimCamera::kPreImageWeightingRed = 1.0;

    float GolfSimCamera::kTeedBallSearchAreaMaskRadiusRatio = 5.0f;
    double GolfSimCamera::kCamera1CalibrationDistanceToBall = 0.5;
    double GolfSimCamera::kCamera2CalibrationDistanceToBall = 0.5;

    double GolfSimCamera::kCamera1XOffsetForTilt = 0.0;
    double GolfSimCamera::kCamera1YOffsetForTilt = 0.0;
    double GolfSimCamera::kCamera2XOffsetForTilt = 0.0;
    double GolfSimCamera::kCamera2YOffsetForTilt = 0.0;

    double GolfSimCamera::kExpectedBallPositionXcm = -50.0;
    double GolfSimCamera::kExpectedBallPositionYcm = -28.0;
    double GolfSimCamera::kExpectedBallPositionZcm = 50.0;
    double GolfSimCamera::kExpectedBallRadiusPixelsAt40cm = 50;
    float GolfSimCamera::kMaxMovedBallRadiusRatio = 1.40f;
    float GolfSimCamera::kMinMovedBallRadiusRatio = 0.50f;
    double GolfSimCamera::kMinRadiusRatio = 0.7;
    double GolfSimCamera::kMaxRadiusRatio = 1.2;
    // Fixed amount to subtract or add to an expected radius to produce a reasonable range
    int GolfSimCamera::kMinRadiusOffset = 10;
    int GolfSimCamera::kMaxRadiusOffset = 10;

    double GolfSimCamera::kUnlikelyAngleMinimumDistancePixels = 40;
    double GolfSimCamera::kMaxQualityExposureLaunchAngle = 45.0;
    double GolfSimCamera::kMinQualityExposureLaunchAngle = -5.0;
    double GolfSimCamera::kMaxPuttingQualityExposureLaunchAngle = +10.0;
    double GolfSimCamera::kMinPuttingQualityExposureLaunchAngle = -10.0;
    int GolfSimCamera::kNumberAngleCheckExposures = 3;

    double GolfSimCamera::kStandardBallSpeedSlowdownPercentage = 0.5;
    double GolfSimCamera::kPracticeBallSpeedSlowdownPercentage = 2.0;
    double GolfSimCamera::kPuttingBallSpeedSlowdownPercentage = 5.0;
    bool GolfSimCamera::kCameraRequiresFlushPulse = true;

    int GolfSimCamera::kMaxBallsToRetain = 18;

    bool GolfSimCamera::kExternallyStrobedEnvFilterImage = true;
    int GolfSimCamera::kExternallyStrobedEnvBottomIgnoreHeight = 70;
    int GolfSimCamera::kExternallyStrobedEnvFilterHsvLowerH = 14;
    int GolfSimCamera::kExternallyStrobedEnvFilterHsvUpperH = 48;
    int GolfSimCamera::kExternallyStrobedEnvFilterHsvLowerS = 26;
    int GolfSimCamera::kExternallyStrobedEnvFilterHsvUpperS = 255;
    int GolfSimCamera::kExternallyStrobedEnvFilterHsvLowerV = 114;
    int GolfSimCamera::kExternallyStrobedEnvFilterHsvUpperV = 255;
    int GolfSimCamera::kExternallyStrobedEnvCannyLower = 156;
    int GolfSimCamera::kExternallyStrobedEnvCannyUpper = 337;
    int GolfSimCamera::kExternallyStrobedEnvPreHoughBlurSize = 13;  // 6 for External Strobe, 9 for normal
    int GolfSimCamera::kExternallyStrobedEnvPreCannyBlurSize = 3;
    
    int GolfSimCamera::kExternallyStrobedEnvHoughLineIntersections = 235;
    int GolfSimCamera::kExternallyStrobedEnvLinesAngleLower = 140;
    int GolfSimCamera::kExternallyStrobedEnvLinesAngleUpper = 180;
    int GolfSimCamera::kExternallyStrobedEnvMaximumHoughLineGap = 7;
    int GolfSimCamera::kExternallyStrobedEnvMinimumHoughLineLength = 23;

    bool GolfSimCamera::kPlacedBallUseLargestBall = true;

    CameraHardware::CameraModel GolfSimCamera::kSystemSlot1CameraType = CameraHardware::CameraModel::PiGSCam6mmWideLens;
    CameraHardware::CameraModel GolfSimCamera::kSystemSlot2CameraType = CameraHardware::CameraModel::PiGSCam6mmWideLens;

    BallImageProc* get_image_processor() {
        static BallImageProc* ip = nullptr;

        if (ip == nullptr) {
            ip = new BallImageProc;
        }

        return ip;
    }


    GolfSimCamera::GolfSimCamera() {

        // TBD - Probably shouldn't be doing all of this in the constructor

        GS_LOG_TRACE_MSG(trace, "GolfSimCamera reading constants from JSON file.");
        // The following constants are only used internal to the GolfSimCamera class, and so can be initialized in the constructor
        GolfSimConfiguration::SetConstant("gs_config.logging.kLogIntermediateExposureImagesToFile", kLogIntermediateExposureImagesToFile);
        GolfSimConfiguration::SetConstant("gs_config.logging.kLogWebserverImagesToFile", kLogWebserverImagesToFile);
        GolfSimConfiguration::SetConstant("gs_config.logging.kLogDiagnosticImagesToUniqueFiles", kLogDiagnosticImagesToUniqueFiles);


        GolfSimConfiguration::SetConstant("gs_config.ball_exposure_selection.kMaximumOffTrajectoryDistance", kMaximumOffTrajectoryDistance);
        GolfSimConfiguration::SetConstant("gs_config.ball_exposure_selection.kNumberHighQualityBallsToRetain", kNumberHighQualityBallsToRetain);
        GolfSimConfiguration::SetConstant("gs_config.ball_exposure_selection.kMaxStrobedBallColorDifferenceStrict", kMaxStrobedBallColorDifferenceStrict);
        GolfSimConfiguration::SetConstant("gs_config.ball_exposure_selection.kMaxStrobedBallColorDifferenceRelaxed", kMaxStrobedBallColorDifferenceRelaxed);
        GolfSimConfiguration::SetConstant("gs_config.ball_exposure_selection.kBallProximityMarginPercentRelaxed", kBallProximityMarginPercentRelaxed);
        GolfSimConfiguration::SetConstant("gs_config.ball_exposure_selection.kMaxPuttingBallColorDifferenceRelaxed", kMaxPuttingBallColorDifferenceRelaxed);
        GolfSimConfiguration::SetConstant("gs_config.ball_exposure_selection.kBallProximityMarginPercentStrict", kBallProximityMarginPercentStrict);

        GolfSimConfiguration::SetConstant("gs_config.ball_exposure_selection.kColorDifferenceRgbPostMultiplierForDarker", kColorDifferenceRgbPostMultiplierForDarker);
        GolfSimConfiguration::SetConstant("gs_config.ball_exposure_selection.kColorDifferenceRgbPostMultiplierForLighter", kColorDifferenceRgbPostMultiplierForLighter);
        GolfSimConfiguration::SetConstant("gs_config.ball_exposure_selection.kColorDifferenceStdPostMultiplierForDarker", kColorDifferenceStdPostMultiplierForDarker);
        GolfSimConfiguration::SetConstant("gs_config.ball_exposure_selection.kColorDifferenceStdPostMultiplierForLighter", kColorDifferenceStdPostMultiplierForLighter);

        GolfSimConfiguration::SetConstant("gs_config.ball_exposure_selection.kMaxDistanceFromTrajectory", kMaxDistanceFromTrajectory);

        GolfSimConfiguration::SetConstant("gs_config.ball_exposure_selection.kClosestBallPairEdgeBackoffPixels", kClosestBallPairEdgeBackoffPixels);
        GolfSimConfiguration::SetConstant("gs_config.ball_exposure_selection.kMaxBallsToRetain", kMaxBallsToRetain);
        
        GolfSimConfiguration::SetConstant("gs_config.strobing.kStandardBallSpeedSlowdownPercentage", kStandardBallSpeedSlowdownPercentage);
        GolfSimConfiguration::SetConstant("gs_config.strobing.kPracticeBallSpeedSlowdownPercentage", kPracticeBallSpeedSlowdownPercentage);
        GolfSimConfiguration::SetConstant("gs_config.strobing.kPuttingBallSpeedSlowdownPercentage", kPuttingBallSpeedSlowdownPercentage);
        GolfSimConfiguration::SetConstant("gs_config.strobing.kCameraRequiresFlushPulse", kCameraRequiresFlushPulse);
        

        GolfSimConfiguration::SetConstant("gs_config.ball_exposure_selection.kMaxIntermediateBallRadiusChangePercent", kMaxIntermediateBallRadiusChangePercent);
        GolfSimConfiguration::SetConstant("gs_config.ball_exposure_selection.kMaxPuttingIntermediateBallRadiusChangePercent", kMaxPuttingIntermediateBallRadiusChangePercent);
        GolfSimConfiguration::SetConstant("gs_config.ball_exposure_selection.kMaxOverlappedBallRadiusChangeRatio", kMaxOverlappedBallRadiusChangeRatio);
        GolfSimConfiguration::SetConstant("gs_config.ball_exposure_selection.kMaxRadiusDifferencePercentageFromBest", kMaxRadiusDifferencePercentageFromBest);
        
        GolfSimConfiguration::SetConstant("gs_config.calibration.kCamera1CalibrationDistanceToBall", kCamera1CalibrationDistanceToBall);
        GolfSimConfiguration::SetConstant("gs_config.calibration.kCamera2CalibrationDistanceToBall", kCamera2CalibrationDistanceToBall);

        GolfSimConfiguration::SetConstant("gs_config.ball_position.kTeedBallSearchAreaMaskRadiusRatio", kTeedBallSearchAreaMaskRadiusRatio);
        
        GolfSimConfiguration::SetConstant("gs_config.cameras.kCamera1XOffsetForTilt", kCamera1XOffsetForTilt);
        GolfSimConfiguration::SetConstant("gs_config.cameras.kCamera1YOffsetForTilt", kCamera1YOffsetForTilt);
        GolfSimConfiguration::SetConstant("gs_config.cameras.kCamera2XOffsetForTilt", kCamera2XOffsetForTilt);
        GolfSimConfiguration::SetConstant("gs_config.cameras.kCamera2YOffsetForTilt", kCamera2YOffsetForTilt);

        GolfSimConfiguration::SetConstant("gs_config.ball_position.kExpectedBallPositionXcm", kExpectedBallPositionXcm);
        GolfSimConfiguration::SetConstant("gs_config.ball_position.kExpectedBallPositionYcm", kExpectedBallPositionYcm);
        GolfSimConfiguration::SetConstant("gs_config.ball_position.kExpectedBallPositionZcm", kExpectedBallPositionZcm);
        GolfSimConfiguration::SetConstant("gs_config.ball_position.kExpectedBallRadiusPixelsAt40cm", kExpectedBallRadiusPixelsAt40cm);
        GolfSimConfiguration::SetConstant("gs_config.ball_position.kMaxMovedBallRadiusRatio", kMaxMovedBallRadiusRatio);
        GolfSimConfiguration::SetConstant("gs_config.ball_position.kMinMovedBallRadiusRatio", kMinMovedBallRadiusRatio);
        GolfSimConfiguration::SetConstant("gs_config.ball_position.kMinRadiusRatio", kMinRadiusRatio);
        GolfSimConfiguration::SetConstant("gs_config.ball_position.kMaxRadiusRatio", kMaxRadiusRatio);
        GolfSimConfiguration::SetConstant("gs_config.ball_position.kMinRadiusOffset", kMinRadiusOffset);
        GolfSimConfiguration::SetConstant("gs_config.ball_position.kMaxRadiusOffset", kMaxRadiusOffset);

        
        GolfSimConfiguration::SetConstant("gs_config.ball_exposure_selection.kUnlikelyAngleMinimumDistancePixels", kUnlikelyAngleMinimumDistancePixels);
        GolfSimConfiguration::SetConstant("gs_config.ball_exposure_selection.kMaxQualityExposureLaunchAngle", kMaxQualityExposureLaunchAngle);
        GolfSimConfiguration::SetConstant("gs_config.ball_exposure_selection.kMinQualityExposureLaunchAngle", kMinQualityExposureLaunchAngle);
        GolfSimConfiguration::SetConstant("gs_config.ball_exposure_selection.kMaxPuttingQualityExposureLaunchAngle", kMaxPuttingQualityExposureLaunchAngle);
        GolfSimConfiguration::SetConstant("gs_config.ball_exposure_selection.kMinPuttingQualityExposureLaunchAngle", kMinPuttingQualityExposureLaunchAngle);
        GolfSimConfiguration::SetConstant("gs_config.ball_exposure_selection.kNumberAngleCheckExposures", kNumberAngleCheckExposures);

        GolfSimConfiguration::SetConstant("gs_config.ball_exposure_selection.kUsePreImageSubtraction", kUsePreImageSubtraction);

        GolfSimConfiguration::SetConstant("gs_config.testing.kExternallyStrobedEnvFilterImage", kExternallyStrobedEnvFilterImage);
        GolfSimConfiguration::SetConstant("gs_config.testing.kExternallyStrobedEnvBottomIgnoreHeight", kExternallyStrobedEnvBottomIgnoreHeight);

        GolfSimConfiguration::SetConstant("gs_config.testing.kExternallyStrobedEnvFilterHsvLowerH", kExternallyStrobedEnvFilterHsvLowerH);
        GolfSimConfiguration::SetConstant("gs_config.testing.kExternallyStrobedEnvFilterHsvUpperH", kExternallyStrobedEnvFilterHsvUpperH);
        GolfSimConfiguration::SetConstant("gs_config.testing.kExternallyStrobedEnvFilterHsvLowerS", kExternallyStrobedEnvFilterHsvLowerS);
        GolfSimConfiguration::SetConstant("gs_config.testing.kExternallyStrobedEnvFilterHsvUpperS", kExternallyStrobedEnvFilterHsvUpperS);
        GolfSimConfiguration::SetConstant("gs_config.testing.kExternallyStrobedEnvFilterHsvLowerV", kExternallyStrobedEnvFilterHsvLowerV);
        GolfSimConfiguration::SetConstant("gs_config.testing.kExternallyStrobedEnvFilterHsvUpperV", kExternallyStrobedEnvFilterHsvUpperV);
        GolfSimConfiguration::SetConstant("gs_config.testing.kExternallyStrobedEnvCannyLower", kExternallyStrobedEnvCannyLower);
        GolfSimConfiguration::SetConstant("gs_config.testing.kExternallyStrobedEnvCannyUpper", kExternallyStrobedEnvCannyUpper);
        GolfSimConfiguration::SetConstant("gs_config.testing.kExternallyStrobedEnvPreHoughBlurSize", kExternallyStrobedEnvPreHoughBlurSize);
        GolfSimConfiguration::SetConstant("gs_config.testing.kExternallyStrobedEnvPreCannyBlurSize", kExternallyStrobedEnvPreCannyBlurSize);
        GolfSimConfiguration::SetConstant("gs_config.testing.kExternallyStrobedEnvHoughLineIntersections", kExternallyStrobedEnvHoughLineIntersections);
        GolfSimConfiguration::SetConstant("gs_config.testing.kExternallyStrobedEnvLinesAngleLower", kExternallyStrobedEnvLinesAngleLower);
        GolfSimConfiguration::SetConstant("gs_config.testing.kExternallyStrobedEnvLinesAngleUpper", kExternallyStrobedEnvLinesAngleUpper);
        GolfSimConfiguration::SetConstant("gs_config.testing.kExternallyStrobedEnvMaximumHoughLineGap", kExternallyStrobedEnvMaximumHoughLineGap);
        GolfSimConfiguration::SetConstant("gs_config.testing.kExternallyStrobedEnvMinimumHoughLineLength", kExternallyStrobedEnvMinimumHoughLineLength);

        GolfSimConfiguration::SetConstant("gs_config.ball_identification.kPlacedBallUseLargestBall", kPlacedBallUseLargestBall);

    }

    GolfSimCamera::~GolfSimCamera() {
    }

    bool GolfSimCamera::DetermineHandedness(const std::vector<GolfBall>& input_balls,
                                            GolferOrientation& handedness) {

        GS_LOG_TRACE_MSG(trace, "DetermineHandedness called with " + std::to_string(input_balls.size()) + " balls.");
        LoggingTools::Trace("Input Balls: ", input_balls);

        if (input_balls.size() < 2) {
            GS_LOG_TRACE_MSG(warning, "DetermineHandedness - balls vector was empty.Exiting function.");
            return false;
        }

        // Get a copy of the input balls so that we can sort it ourselves.
        std::vector<GolfBall> balls(input_balls);

        // Sort by x-position, with the first balls being the left-most
        std::sort(balls.begin(), balls.end(), [](const GolfBall& a, const GolfBall& b)
            { return (a.x() < b.x()); });

        LoggingTools::Trace("Sorted Balls: ", balls);

        // Counts the pairs of balls where the left ball is lower than the right ball
        int positive_slope_count = 0;

        for (int i = 0; i < (int)balls.size() - 1; i++) {
            const GolfBall& ball1 = balls[i];
            const GolfBall& ball2 = balls[i + 1];

            // Don't compare concentric balls
            if (ball1.x() == ball2.x() && ball1.y() == ball2.y()) {
                continue;
            }

            if (ball1.y() >= ball2.y()) {
                positive_slope_count++;
            }
            else {
                positive_slope_count--;
            }
        }

        handedness = (positive_slope_count >= 0) ? GolferOrientation::kRightHanded : GolferOrientation::kLeftHanded;
        std::string handedness_string = (handedness == GolferOrientation::kRightHanded) ? "right_handed" : "left_handed";
        GS_LOG_TRACE_MSG(trace, "DetermineHandedness result: " + handedness_string + ", with positive_slope_count = " + std::to_string(positive_slope_count));

        return true;
    }

    int GolfSimCamera::getExpectedBallRadiusPixels(const CameraHardware& camera_hardware, const int resolution_x_, const double distance) {

        if (!camera_hardware.cameraInitialized || resolution_x_ <= 0) {
            GS_LOG_MSG(warning, "Camera hardware (or resolution x value) not initialized in getExpectedBallRadiusPixels!");
            // TBD - For now, just ignore.    return false;
        }

        // Get a reasonable default in case (for some reason), the camera's expected radius has not been set
        double radius = kExpectedBallRadiusPixelsAt40cm;

        // Get the camera's expected ball radius.  There might be two different cameras, or two different
        // lenses (e.g., one wide, one telephoto), with different respective radii.
        if (camera_hardware.expected_ball_radius_pixels_at_40cm_ > 0) {
            radius = camera_hardware.expected_ball_radius_pixels_at_40cm_;
        }
        else {
            GS_LOG_TRACE_MSG(warning, "expected_ball_radius_pixels_at_40cm_ not set in camera in GolfSimCamera::getExpectedBallRadiusPixels().  Setting to default instead.");
        }

        GS_LOG_TRACE_MSG(trace, "getExpectedBallRadiusPixels called with resolution: " + std::to_string(resolution_x_) + 
                        ", distance: " + std::to_string(distance) + ", and with expected radius at 40cm of: " + std::to_string(radius));

        if (std::abs(distance) < 0.0001) {
            GS_LOG_MSG(error, "getExpectedBallRadiusPixels called with 0 distance.");
            return 0;
        }

        radius *= (0.40 / distance);

        // Scale to our current resolution
        radius *= ((double)resolution_x_ / 1456.0);

        GS_LOG_TRACE_MSG(trace, "getExpectedBallRadiusPixels returning: " + std::to_string(std::round(radius)));

        return (int)std::round(radius);
    }


    std::vector<GsColorTriplet> GolfSimCamera::GetBallHSVRange(const GsColorTriplet& ball_color_RGB) {

        // Create an HSV range around the average color that will be broad enough to encompass
        // any expected HSV values of pixes in the golf ball as it moves through the frame
        //hsv = cs.rgb_to_hsv(ball_color_[2], ball_color_[1], ball_color_[0])
        GsColorTriplet hsvAvg = CvUtils::ConvertRgbToHsv(ball_color_RGB);

        //GS_LOG_TRACE_MSG(trace, "GetBallHSVRange COLORSYS computed HSV of: " + std::to_string(hsvAvg))

        // Note that the consumer of this function will need to loop around the 360 degree circle if the widened hue numbers
        // go belore zero
        float hmin = (float)hsvAvg[0] - H_MIN_CAL_COLOR_WIDENING_AMOUNT;
        float hmax = (float)hsvAvg[0] + H_MAX_CAL_COLOR_WIDENING_AMOUNT;
        float smin = (float)std::max(0, (int)hsvAvg[1] - (int)(S_MIN_CAL_COLOR_WIDENING_AMOUNT));
        float vmin = (float)std::max(0, (int)hsvAvg[2] - (int)(V_MIN_CAL_COLOR_WIDENING_AMOUNT * 0.9));

        float smax = (float)std::min((int)CvUtils::kOpenCvSatMax, (int)hsvAvg[1] + S_MAX_CAL_COLOR_WIDENING_AMOUNT);
        float vmax = (float)std::min((int)CvUtils::kOpenCvValMax, (int)hsvAvg[2] + V_MAX_CAL_COLOR_WIDENING_AMOUNT);

        GsColorTriplet hsvMin{ hmin, smin, vmin };
        GsColorTriplet hsvMax{ hmax, smax, vmax };

        std::vector<GsColorTriplet> r;
        r.push_back(hsvMin);
        r.push_back(hsvMax);

        GS_LOG_TRACE_MSG(trace, "GetBallHSVRange for average (" + LoggingTools::FormatGsColorTriplet(hsvAvg) + ") = "
            + LoggingTools::FormatGsColorTriplet(hsvMin) + " | " + LoggingTools::FormatGsColorTriplet(hsvMax));

        return r;
    }

    // Expects a single ball to be placed near the expectedBallCenter at a certain
    // distance from the camera.
    // Returns true iff the input ball was successfully calibrated
    bool GolfSimCamera::GetCalibratedBall(const GolfSimCamera& camera,
        const cv::Mat& rgbImg,
        GolfBall& b,
        const cv::Vec2i& expectedBallCenter,
        const bool expectBall) {

        GS_LOG_TRACE_MSG(trace, "GetCalibratedBall");

        BallImageProc* ip = get_image_processor();
        ip->image_name_ = "Calibration Photo";

        if (rgbImg.empty()) {
            GS_LOG_MSG(error, "GetCalibratedBall received an empty photo.");
            return false;
        }

        if (!camera_hardware_.cameraInitialized) {
            GS_LOG_MSG(error, "Camera hardware not initialized in GetCalibratedBall!");
            return false;
        }

        // Make sure the image we got is the dimensions that we are expecting
        // TBD - NEED TO REFACTOR SO THAT RESOLUTION IS NOT COMING FROM THE CAMERA!
        if (rgbImg.rows != camera_hardware_.resolution_y_ || rgbImg.cols != camera_hardware_.resolution_x_) {
            GS_LOG_MSG(error, "Returned photo does not match camera resolution!");
            return false;
        }


        LoggingTools::DebugShowImage("Calibration Photo", rgbImg);

        // We expect the ball to be near the origin, so will assume that distance
        double expected_distance = 0;

        if (GolfSimOptions::GetCommandLineOptions().GetCameraNumber() == GsCameraNumber::kGsCamera1) {
            expected_distance = CvUtils::GetDistance(kCamera1PositionsFromExpectedBallMeters);
        }
        else {
            expected_distance = CvUtils::GetDistance(kCamera2PositionsFromExpectedBallMeters);
            GS_LOG_TRACE_MSG(trace, "GetCalibratedBall called for camera2 (usually used for camera1 images).");
        }

        // If we are calibrating the focal length, then override the distance to that specified in 
        // the JSON file
        if (GolfSimOptions::GetCommandLineOptions().system_mode_ == SystemMode::kCamera1Calibrate ||
            GolfSimOptions::GetCommandLineOptions().system_mode_ == SystemMode::kCamera2Calibrate ||
            GolfSimOptions::GetCommandLineOptions().system_mode_ == SystemMode::kCamera1BallLocation ||
            GolfSimOptions::GetCommandLineOptions().system_mode_ == SystemMode::kCamera2BallLocation ||
            GolfSimOptions::GetCommandLineOptions().system_mode_ == SystemMode::kCamera1TestStandalone ||
            GolfSimOptions::GetCommandLineOptions().system_mode_ == SystemMode::kCamera2TestStandalone) {

            if (kCamera1CalibrationDistanceToBall > 0.01) {
                if (GolfSimOptions::GetCommandLineOptions().GetCameraNumber() == GsCameraNumber::kGsCamera1) {
                    expected_distance = kCamera1CalibrationDistanceToBall;
                }
                else {
                    expected_distance = kCamera2CalibrationDistanceToBall;
                }
                GS_LOG_TRACE_MSG(trace, "GetCalibratedBall overriding expected_distance.  Setting to: " + std::to_string(expected_distance));
            }
        }

        GS_LOG_TRACE_MSG(trace, "GetCalibratedBall using expected ball distance of: " + std::to_string(expected_distance));

        // TBD - Will want to be able to vary the calibration distance later
        double expectedRadius = getExpectedBallRadiusPixels(camera.camera_hardware_, rgbImg.cols, expected_distance);
        int min = std::max(0, (int)std::round(expectedRadius) - kMinRadiusOffset);
        int max = int((int)expectedRadius + kMaxRadiusOffset);

        ip->min_ball_radius_ = min;
        ip->max_ball_radius_ = max;
        GS_LOG_TRACE_MSG(trace, "GetCalibratedBall Looking for a ball with min/max radius (pixels) of: " + std::to_string(min) + ", " + std::to_string(max));

        // Expect the ball in the center of the image if not otherwise specified
        int expected_ball_X = expectedBallCenter[0];
        int expected_ball_Y = expectedBallCenter[1];

        cv::Rect roi;

        if (expected_ball_X == 0 && expected_ball_Y == 0) {
            expected_ball_X = int(rgbImg.cols / 2);
            expected_ball_Y = int(rgbImg.rows / 2);

            // Limit the search area if we know where it should be
            double search_area_radius = max * 1.1;  // add a little buffer to make sure we can find things at the edge
            roi = cv::Rect{ (int)(expected_ball_X - search_area_radius), (int)(expected_ball_Y - search_area_radius),
                           (int)(2. * search_area_radius), (int)(2. * search_area_radius) };
        }

        int mask_radius = 0;

        if (kTeedBallSearchAreaMaskRadiusRatio > 0.01) {
            mask_radius = int(expectedRadius * kTeedBallSearchAreaMaskRadiusRatio);
            GS_LOG_TRACE_MSG(trace, "GetCalibratedBall using search mask_radius (computed using kTeedBallSearchAreaMaskRadiusRatio=" + std::to_string(kTeedBallSearchAreaMaskRadiusRatio) + " of: " + std::to_string(mask_radius));
            ip->area_mask_image_ = CvUtils::GetAreaMaskImage(rgbImg.cols, rgbImg.rows, expected_ball_X, expected_ball_Y, mask_radius, roi);
            LoggingTools::DebugShowImage("AreaMaskImage Photo", ip->area_mask_image_);
        }
        else {
            cv::Mat nullAreaMaskImage;
            ip->area_mask_image_ = nullAreaMaskImage;
            GS_LOG_TRACE_MSG(trace, "GetCalibratedBall not using a search mask_radius (because kTeedBallSearchAreaMaskRadiusRatio was = " + std::to_string(kTeedBallSearchAreaMaskRadiusRatio));
        }

        // The whole point here is that we don't know the color until we calibrate, so force a 
        // very broad color range mask
        // NOTE - the entire color thing is pretty much deprecated now - signal that we don't know the color
        ip->ball_.ball_color_ = GolfBall::BallColor::kUnknown;

        // This is more useful when using the Hough Circle search technique.
        // Lately has been producing the wrong results
        bool useLargestFoundBall = false;

        std::vector<GolfBall> return_balls;
        bool result = ip->GetBall(rgbImg, b, return_balls, roi, BallImageProc::BallSearchMode::kFindPlacedBall, useLargestFoundBall, expectBall);

        if (!result || return_balls.empty()) {
            if (expectBall) {
                GS_LOG_MSG(error, "GetBall() failed to get a ball.");
            }

            // Pass the information about where the system searched for the ball
            // So that the caller can (potentially) indicate where it was
            // supposed to be (given that it was not found).
            b.search_area_center_[0] = expected_ball_X;
            b.search_area_center_[1] = expected_ball_Y;
            b.search_area_radius_ = mask_radius;

            return false;
        }

        GS_LOG_MSG(trace, "GetBall() returned " + std::to_string(return_balls.size()) + " ball(s).");
        ShowAndLogBalls("GetBallReturnedBalls", rgbImg, return_balls, kLogIntermediateExposureImagesToFile);


        // Assign the returned ball's information to the ball this function will return
        if (kPlacedBallUseLargestBall) {

            int largest_index = 0;
            double largest_radius = -1.0;

            for (size_t i = 0; i < return_balls.size(); i++) {

                double found_radius = return_balls[i].measured_radius_pixels_;

                if (found_radius > largest_radius) {
                    largest_radius = found_radius;
                    largest_index = (int)i;
                }
            }

            b = return_balls[largest_index];
        }
        else {
            b = return_balls.front();
        }

        std::vector<GolfBall> final_ball{ (b) };
        GS_LOG_TRACE_MSG(trace, "GetBallReturnedBalls Final Ball (calibrated):" + b.Format());
        ShowAndLogBalls("GetBallReturnedBalls Final Ball:", rgbImg, final_ball, kLogIntermediateExposureImagesToFile);



        // We were able to discern a circle that the system thinks is a ball - return the ball with the information corresponding to it inside

        // Setup a ball to return with all the pertinent information
        b.measured_radius_pixels_ = b.ball_circle_[2];

        // We might also try to force the user to put the ball at a specific distance from the camera and calibrate from that
        // Note that the distance being calculated here is not the Z-axis only distance, but instead it is the distance
        // directly to the ball, as the crow flies.

        double distance_direct_to_ball = -1.0;

        if (GolfSimOptions::GetCommandLineOptions().system_mode_ == SystemMode::kCamera1Calibrate ||
            GolfSimOptions::GetCommandLineOptions().system_mode_ == SystemMode::kCamera2Calibrate) {

            if (GolfSimOptions::GetCommandLineOptions().GetCameraNumber() == GsCameraNumber::kGsCamera1) {
                distance_direct_to_ball = kCamera1CalibrationDistanceToBall;
            }
            else {
                distance_direct_to_ball = kCamera2CalibrationDistanceToBall;
            }
            
            b.distance_to_z_plane_from_lens_ = distance_direct_to_ball;

            // Note - since we are measuring the ball using the standard focal length of the camera hardware,
            // when we compute the length again here, it should be the same.  We'd use this if we have the ball 
            // at a known, precise distance and then get the focal length that makes the system find that distance.
            b.calibrated_focal_length_ = computeFocalDistanceFromBallData(camera, b.measured_radius_pixels_, distance_direct_to_ball);
            GS_LOG_MSG(info, "Calibrated focal length for distance " + std::to_string(distance_direct_to_ball) + " and Radius: " + std::to_string(b.measured_radius_pixels_) +
                        " mm is " + std::to_string(b.calibrated_focal_length_) + ".");

            return true;
        }
        else {
            distance_direct_to_ball = ComputeDistanceToBallUsingRadius(camera, b);
            b.distance_to_z_plane_from_lens_ = distance_direct_to_ball;
        }

        // Make sure all the related ball elements are set consistently
        b.set_circle(b.ball_circle_);

        cv::Vec2d camera_angles = camera.camera_hardware_.camera_angles_;

        // The golf ball may not be centered in the frame of the camera.  Determine the angle at which
        // the ball sits so that it can be taken into account for, e.g., ball rotation perspectives

        if (!ComputeXyzDistanceFromOrthoCamPerspective(camera, b, b.distances_ortho_camera_perspective_)) {
            GS_LOG_MSG(error, "Could not calculate ComputeXyzDistanceFromOrthoCamPerspective");
            return false;
        }
        if (!ComputeBallXYAnglesFromCameraPerspective(b.distances_ortho_camera_perspective_, b.angles_camera_ortho_perspective_)) {
            GS_LOG_MSG(error, "Could not calculate ComputeBallXYAnglesFromCameraPerspective");
            return false;
        }

        GetBallColorInformation(rgbImg, b);

        b.distance_at_calibration_ = distance_direct_to_ball;
        // The measured radius may change later, so save the current one now
        b.radius_at_calibration_pixels_ = (float)b.measured_radius_pixels_;

        b.calibrated = true;

        GS_LOG_TRACE_MSG(trace, "Calibrated Ball Results: " + b.Format());

        return true;
    }


    void GolfSimCamera::GetBallColorInformation(const cv::Mat& color_image, GolfBall& b) {
        std::vector<GsColorTriplet> stats = CvUtils::GetBallColorRgb(color_image, b.ball_circle_);
        b.average_color_ = stats[0];
        b.median_color_ = stats[1];
        b.std_color_ = stats[2];
        b.ball_color_ = GolfBall::BallColor::kCalibrated;

        std::vector<GsColorTriplet> hsvRange = GetBallHSVRange(b.average_color_);
        b.ball_hsv_range_.min = hsvRange[0];
        b.ball_hsv_range_.max = hsvRange[1];
    }

    bool GolfSimCamera::ReverseBallAngleDeltas(GolfBall& ball) {
        // TBD - Just started work on this.  Not sure we need to negate ALL of the angles
        // If this is wrong, it can scew up the spin analysis.
        // ball.position_deltas_ball_perspective_ = -ball.position_deltas_ball_perspective_;
        ball.angles_ball_perspective_ = -ball.angles_ball_perspective_;
        return true;
    }

    bool GolfSimCamera::ComputeBallDeltas(GolfBall& ball1, GolfBall& ball2, const GolfSimCamera& first_camera, const GolfSimCamera& second_camera) {

        if (!ComputeSingleBallXYZOrthoCamPerspective(first_camera, ball1)) {
            GS_LOG_MSG(error, "ComputeBallDeltas: Could not ComputeSingleBallXYZOrthoCamPerspective for ball1");
            return false;
        }

        // The second ball is assumed always to be related to camera 2, so use kCamera2Angles
        if (!ComputeSingleBallXYZOrthoCamPerspective(second_camera, ball2)) {
            GS_LOG_MSG(error, "ComputeBallDeltas: Could not ComputeSingleBallXYZOrthoCamPerspective for ball2");
            return false;
        }

        GS_LOG_TRACE_MSG(trace, "GolfSimCamera::ComputeBallDeltas - ball1 is:\n" + ball1.Format());
        GS_LOG_TRACE_MSG(trace, "GolfSimCamera::ComputeBallDeltas - ball2 is:\n" + ball2.Format());

        // At this point, we know the distances and angles of each ball relative to the camera
        // Next, find the delta differences in distance and angles as between the two balls

        if (!ComputeXyzDeltaDistances(ball1, ball2, ball2.position_deltas_ball_perspective_, ball2.distance_deltas_camera_perspective_)) {
            GS_LOG_MSG(error, "Could not calculate ComputeXyzDeltaDistances");
            return false;
        }


        // If the images were taken by different cameras at some distance from each other, we will account for that here
        // For example, if the second camera is to the right of the first (looking at the ball), then that right-direction
        // distance on the X axis should be added to the distance delta in the X-axis of the ball.

        if (first_camera.camera_hardware_.camera_number_ != second_camera.camera_hardware_.camera_number_) {  
            // The first camera is camera_1, so add the offset to camera_2
            ball2.distance_deltas_camera_perspective_ += kCamera2OffsetFromCamera1OriginMeters;
            ball2.position_deltas_ball_perspective_[0] += kCamera2OffsetFromCamera1OriginMeters[2];
            ball2.position_deltas_ball_perspective_[1] += kCamera2OffsetFromCamera1OriginMeters[1];
            ball2.position_deltas_ball_perspective_[2] += kCamera2OffsetFromCamera1OriginMeters[0];
        }

        if (!getXYDeltaAnglesBallPerspective(ball2.position_deltas_ball_perspective_, ball2.angles_ball_perspective_)) {
            GS_LOG_MSG(error, "Could not calculate getXYDeltaAnglesBallPerspective");
            return false;
        }


        GS_LOG_TRACE_MSG(trace, "Calculated X,Y angles (ball perspective) (in degrees) are: " + std::to_string(ball2.angles_ball_perspective_[0]) + ", " +
            std::to_string(ball2.angles_ball_perspective_[1]));

        GS_LOG_TRACE_MSG(trace, "Calculated DELTA X,Y, Z distances (ball perspective) are: " + std::to_string(ball2.position_deltas_ball_perspective_[0]) + ", " +
            std::to_string(ball2.position_deltas_ball_perspective_[1]) + ", " + std::to_string(ball2.position_deltas_ball_perspective_[2]));

        GS_LOG_TRACE_MSG(trace, "Calculated currentDistance is: " + std::to_string(ball2.distance_to_z_plane_from_lens_) + " meters = " +
            std::to_string(12*CvUtils::MetersToFeet(ball2.distance_to_z_plane_from_lens_)) + " inches from the lens.");

        return true;
    }


    // TBD - Make sure we know if the 
    bool GolfSimCamera::ComputeSingleBallXYZOrthoCamPerspective(const GolfSimCamera& camera, GolfBall& ball1 ) {

        ball1.distance_to_z_plane_from_lens_ = ComputeDistanceToBallUsingRadius(camera, ball1);

        // The golf ball may not be centered in the frame of the camera.  Determine the distances and angle at which
        // the ball sits so that it can be taken into account for, e.g., ball rotation perspectives
        if (!ComputeXyzDistanceFromOrthoCamPerspective(camera, ball1, ball1.distances_ortho_camera_perspective_)) {
            GS_LOG_MSG(error, "Could not calculate ComputeXyzDistanceFromOrthoCamPerspective");
            return false;
        }

        if (!ComputeBallXYAnglesFromCameraPerspective(ball1.distances_ortho_camera_perspective_, ball1.angles_camera_ortho_perspective_)) {
            GS_LOG_MSG(error, "Could not calculate ComputeBallXYAnglesFromCameraPerspective");
            return false;
        }


        /* DEBUG
        GS_LOG_TRACE_MSG(trace, "Calculated X,Y angles (camera perspective) (in degrees) are: " + std::to_string(angles_camera_perspective[0]) + ", " +
            std::to_string(angles_camera_perspective[1]));

        GS_LOG_TRACE_MSG(trace, "Calculated X,Y angles (ball perspective) (in degrees) are: " + std::to_string(angles_ball_perspective[0]) + ", " +
            std::to_string(angles_ball_perspective[1]));

        GS_LOG_TRACE_MSG(trace, "Calculated currentDistance is: " + std::to_string(ball1.distance_to_z_plane_from_lens_) + " meters = " +
            std::to_string(12*CvUtils::MetersToFeet(ball1.distance_to_z_plane_from_lens_)) + " inches from the lens.");
        */

        return true;
    }



        // returns a new golf ball object with the ball's current information
        // Returns true iff the new ball was successfully located
        // The first, calibrated ball is used to help find the "found" ball.
        // For example, the radius (and possibly color) of the first calibrated ball
        // is used to help narrow the image processing for the "found" ball.

        bool GolfSimCamera::GetCurrentBallLocation(const GolfSimCamera& camera, 
                                                   const cv::Mat& rgbImg,
                                                   const GolfBall& calibrated_ball, 
                                                   GolfBall& foundBall) {
                
            GS_LOG_TRACE_MSG(trace, "GetCurrentBallLocation(ball).  calibrated_ball = " + calibrated_ball.Format());

            if (!calibrated_ball.calibrated ) {

                GS_LOG_MSG(error, "GetCurrentBallLocation called without a properly calibrated ball.");
                return false;
            }

            // TBD - will copy work on a ball yet ?
            foundBall = calibrated_ball;

            BallImageProc *ip = get_image_processor();

            LoggingTools::DebugShowImage("GolfSimCamera::GetCurrentBallLocation input: ", rgbImg);

            // Find where the ball currently is based on where we expected it from the prior information

            double distance_at_calibration_ = calibrated_ball.distance_at_calibration_;

            double radius_at_calibration_pixels_ = calibrated_ball.radius_at_calibration_pixels_;
            ip->min_ball_radius_ = int(radius_at_calibration_pixels_ * kMinMovedBallRadiusRatio);
            ip->max_ball_radius_ = int(radius_at_calibration_pixels_ * kMaxMovedBallRadiusRatio);

            GS_LOG_TRACE_MSG(trace, "Original radius at calibration-time distance of " + std::to_string(distance_at_calibration_) + " was: " + std::to_string(radius_at_calibration_pixels_) + ". Looking for a ball with min/max radius (pixels) of: " +
                std::to_string(ip->min_ball_radius_) + ", " + std::to_string(ip->max_ball_radius_));

            // This is more useful when using the Hough Circle search technique
            bool useLargestFoundBall = true;

            cv::Rect emptyROI; 
            cv::Mat nullAreaMaskImage;
            ip->area_mask_image_ = nullAreaMaskImage;

            std::vector<GolfBall> return_balls;
            bool result = ip->GetBall(rgbImg, foundBall, return_balls, emptyROI, BallImageProc::BallSearchMode::kFindPlacedBall, useLargestFoundBall);

            if (!result || return_balls.empty()) {
                GS_LOG_MSG(error, "GetBall() failed to get a ball.");
                return false;
            }

            // Transfer the new ball information to the output ball
            foundBall = return_balls.front();

            if (!ComputeSingleBallXYZOrthoCamPerspective(camera, foundBall)) {
                GS_LOG_MSG(error, "GolfSimCamera::GetCurrentBallLocation failed to ComputeSingleBallXYZOrthoCamPerspective.");
                return false;
            }

            return true;
        }

        cv::Vec2d GolfSimCamera::computeCameraAnglesToBallPlane(cv::Vec3d& camera_positions_from_origin) {
            cv::Vec2d angles;

            double camera_height_above_ball = camera_positions_from_origin[1];
            double zDistanceToBall = camera_positions_from_origin[2];

            if (camera_height_above_ball < 0.0 || std::abs(zDistanceToBall) <= 0.001) {
                LoggingTools::Warning("GolfSimCamera::computeCameraAnglesToBallPlane called, but camera_height_above_ball_ or zDistanceToBall <= 0 (and likely not set)");
            }

            angles[1] = CvUtils::RadiansToDegrees(atan(camera_height_above_ball / zDistanceToBall));

            return angles;
        }



        bool GolfSimCamera::analyzeShotImages(  const GolfSimCamera& camera, 
                                                const cv::Mat& rgbImg1,
                                                const cv::Mat& rgbImg2,
                                                long timeDelayuS,
                                                const std::vector<cv::Vec3d>& camera_positions_from_origin,
                                                GolfBall& result_ball,
                                                const cv::Vec2i& expectedBallCenter) {

            if (timeDelayuS == 0) {
                GS_LOG_MSG(error, "In analyzeShotImages, timeDelayuS was 0.");
            }

            GolfBall ball1;

            // Get the ball data.  We will calibrate based on the first ball and then get the second one
            // using that calibrated data from the first ball.

            // The Vec2i is a hack to deal with the ball in the test images not being in the center (where it would be expected)
            bool success = GetCalibratedBall(camera, rgbImg1, ball1, expectedBallCenter);

            if (!success) {
                GS_LOG_TRACE_MSG(trace, "Could not find the first ball to calibrate!");
                return false;
            }

            GS_LOG_TRACE_MSG(trace, "Ball1 (calibrated):" + ball1.Format());

            if (GolfSimOptions::GetCommandLineOptions().system_mode_ == SystemMode::kCamera1Calibrate ||
                GolfSimOptions::GetCommandLineOptions().system_mode_ == SystemMode::kCamera2Calibrate) {

                ball1.calibrated_focal_length_ = computeFocalDistanceFromBallData(camera, ball1.measured_radius_pixels_, ball1.distance_to_z_plane_from_lens_);

                return true;
            }


            // Using the first ball for reference, determine where the second one is in relation to the first
            success = GetCurrentBallLocation(camera, rgbImg2, ball1, result_ball);

            if (!success) {
                GS_LOG_TRACE_MSG(trace, "Could not find 2nd ball");
                return false;
            }

            GS_LOG_TRACE_MSG(trace, "Ball2 :" + result_ball.Format());

            // Now figure out the rotational speeds
            cv::Mat grayImg1, grayImg2;
            cv::cvtColor(rgbImg1, grayImg1, cv::COLOR_BGR2GRAY);
            cv::cvtColor(rgbImg2, grayImg2, cv::COLOR_BGR2GRAY);

            cv::Vec3d rotationResults = BallImageProc::GetBallRotation(grayImg1, ball1, grayImg2, result_ball);

            CalculateBallSpinRates(result_ball, rotationResults, timeDelayuS);

            return true;
        }


        void GolfSimCamera::CalculateBallVelocity(GolfBall& b, long time_delay_us) {

            // TBD - streamline the math
            b.velocity_ = GetTotalDistance(b.position_deltas_ball_perspective_);
            b.velocity_ /= (double)(time_delay_us);
            b.velocity_ *= (double)1000000;
        }

        void GolfSimCamera::CalculateBallSpinRates(GolfBall& b, const cv::Vec3d& rotation_results, long time_delay_us){

            b.ball_rotation_angles_camera_ortho_perspective_ = rotation_results;
            b.rotation_speeds_RPM_[0] = 60. * ((rotation_results[0] / 360.) / (double)(time_delay_us)) * 1000000.;
            b.rotation_speeds_RPM_[1] = 60. * ((rotation_results[1] / 360.) / (double)(time_delay_us)) * 1000000.;
            b.rotation_speeds_RPM_[2] = 60. * ((rotation_results[2] / 360.) / (double)(time_delay_us)) * 1000000.;
        }


        double GolfSimCamera::GetTotalDistance(cv::Vec3d& distance_deltas) {
            return sqrt(pow(distance_deltas[0], 2) + pow(distance_deltas[1], 2) + pow(distance_deltas[2], 2));
        }

        // Determine the focal length based on a distance and measured radius (in pixels)
        double GolfSimCamera::computeFocalDistanceFromBallData(const GolfSimCamera& camera, double ball_radius_pixels, double ball_distance_meters) {
            
            // Could reasonably do this with either height or width parameters for the sensors that we are using,
            // but for at least the GS camera, the "correct" divisor is the X axis, not Y.
            return ( ball_distance_meters * camera.camera_hardware_.sensor_width_ * ((2.0 * ball_radius_pixels) / camera.camera_hardware_.resolution_x_ ) / (2.0*GolfBall::kBallRadiusMeters));
        }

        double GolfSimCamera::convertXDistanceToMeters(const GolfSimCamera& camera, double zDistanceMeters, double xDistancePixels) {
            // Note that we are NOT using the calibrated_focal_length
            double halfWidthMeters = (zDistanceMeters / camera.camera_hardware_.focal_length_) * (camera.camera_hardware_.sensor_width_ / 2.0);
            double xDistanceMeters = halfWidthMeters * (xDistancePixels / (camera.camera_hardware_.resolution_x_ / 2.0));
            return (xDistanceMeters);
        }

        double GolfSimCamera::convertYDistanceToMeters(const GolfSimCamera& camera, double zDistanceMeters, double yDistancePixels) {
            // Note that we are NOT using the calibrated_focal_length
            double halfHeightMeters = (zDistanceMeters / camera.camera_hardware_.focal_length_) * (camera.camera_hardware_.sensor_height_/2.0);
            double yDistanceMeters = halfHeightMeters * (yDistancePixels / (camera.camera_hardware_.resolution_y_ / 2.0));
            return (yDistanceMeters);
        }

        double GolfSimCamera::ComputeDistanceToBallUsingRadius(const GolfSimCamera& camera, const GolfBall& ball) {
            // compute and return the distance from the object to the camera in meters
            // (based on triangle similarity, e.g., https://pyimagesearch.com/2015/01/19/find-distance-camera-objectmarker-using-python-opencv/) is

            double chosenRadiusPixels;

            double effectiveSensorWidth;
            double effectiveCameraResolution;

            if (ball.ball_ellipse_.size.width > 0 && ball.ball_ellipse_.size.height > 0) {

                // TBD - Currently Deprecated
                

                // If we have ellipse representation, then use it - it's probably more reliable than a strict circle, but
                // we need to figure out WHICH radius of the ellipse to use
                
                // TBD -- Seems to work correctly only if we use the (smaller) width.
                // We could also use the largest radius in the hope that it will be more accurate, percentage-wise
                // This should presumably be the height
                chosenRadiusPixels = std::min(ball.ball_ellipse_.size.width, ball.ball_ellipse_.size.height) / 2.0;

                // The ellipse may be at an angle.  
                // Use the effective number of pixels on the sensor at that angle as a measuring stick to determine the real-world distance
                double ellipseAngleDegrees = ball.ball_ellipse_.angle;

                // From vertical
                double ellipseAngleAtSensorCorner = CvUtils::RadiansToDegrees(atan(camera.camera_hardware_.sensor_height_ / camera.camera_hardware_.sensor_width_));


                // See notebook for details of this algorithm
                // Note - see https://namkeenman.wordpress.com/2015/12/21/opencv-determine-orientation-of-ellipserotatedrect-in-fitellipse/
                // for details of rotatedRect angles.  They are non-intuitive.  Ellipse angle is to the right from vertical
                if ((ellipseAngleDegrees > ellipseAngleAtSensorCorner && ellipseAngleDegrees < 180 - ellipseAngleAtSensorCorner) ||
                    (ellipseAngleDegrees > (180 + ellipseAngleAtSensorCorner) && ellipseAngleDegrees < (360 - ellipseAngleAtSensorCorner))
                    ) {
                    effectiveSensorWidth = std::abs(camera.camera_hardware_.sensor_width_ / cos(CvUtils::DegreesToRadians(90 - ellipseAngleDegrees)));
                    effectiveCameraResolution = std::abs(camera.camera_hardware_.resolution_x_ / cos(CvUtils::DegreesToRadians(90 - ellipseAngleDegrees)));
                }
                else {
                    effectiveSensorWidth = std::abs((double)camera.camera_hardware_.sensor_height_ / cos(CvUtils::DegreesToRadians(ellipseAngleDegrees)));  // 90-ellipse angle
                    effectiveCameraResolution = std::abs((double)camera.camera_hardware_.resolution_y_ / cos(CvUtils::DegreesToRadians(ellipseAngleDegrees)));
                }

            }
            else {
                // Use the information from the circle to determine the radiue
                chosenRadiusPixels = CvUtils::CircleRadius(ball.ball_circle_);

                effectiveSensorWidth = camera.camera_hardware_.sensor_width_;
                effectiveCameraResolution = camera.camera_hardware_.resolution_x_;
            }

            // Use similar triangles should also work
            // double ballRadiusMeters = (effectiveCameraResolution / (2.0 * chosenRadiusPixels)) * (2.0 * kBallRadiusMeters) * (camera.focal_length_ / effectiveSensorWidth);

            double distanceToBallMeters = (effectiveCameraResolution / (2.0 * chosenRadiusPixels)) * (2.0 * GolfBall::kBallRadiusMeters) * (camera.camera_hardware_.focal_length_ / effectiveSensorWidth);

            return distanceToBallMeters;

            // TBD - AlternativelyCreate an upright (non-rotated) rectangle that fits around the ellipse, which is itself a rotated rect.
            // Then, use the X and Y widths of the resulting upright rectangle to figure out how wide/high the ellipse is.  
            // Finally, use the pythagorean theory to figure out the diagonal's real-world length.

            std::vector<cv::Point> contours;    // ?? = std::vector<cv:Point>(ball.ball_ellipse_.re);

        }


        bool GolfSimCamera::ComputeXyzDeltaDistances(const GolfBall& b1, const GolfBall& b2, cv::Vec3d& position_deltas_ball_perspective, cv::Vec3d& distance_deltas_camera_perspective) {
            // Axes are as perceived by the camera -- z is close/far, x is left/right, and y is up/down

            // Distance is already in real-world meters
            distance_deltas_camera_perspective[0] = b2.distances_ortho_camera_perspective_[0] - b1.distances_ortho_camera_perspective_[0];
            distance_deltas_camera_perspective[1] = b2.distances_ortho_camera_perspective_[1] - b1.distances_ortho_camera_perspective_[1];
            distance_deltas_camera_perspective[2] = b2.distances_ortho_camera_perspective_[2] - b1.distances_ortho_camera_perspective_[2];

            // Ball X is -Camera Z, Ball Y is Camera Y, Ball Z is Camera X  (TBD - earlier, this was computed from the other two ??
            position_deltas_ball_perspective[0] = -(b2.distances_ortho_camera_perspective_[2] - b1.distances_ortho_camera_perspective_[2]);
            position_deltas_ball_perspective[1] = b2.distances_ortho_camera_perspective_[1] - b1.distances_ortho_camera_perspective_[1];
            position_deltas_ball_perspective[2] = b2.distances_ortho_camera_perspective_[0] - b1.distances_ortho_camera_perspective_[0];

            return true;
        }

        // Camera angles are measured as follows:
        //      Negative X angle is degrees to the left of the camera bore line
        //      Negative Y angle is degrees down from the camera bore line.
        // The camera bore line is assumed to be straigt out from the system hardware
        // toward (and orthogonal to) the ball plane 
        // The adjusted distances will be as follows:
        //      -X is the distance to the left of the camera lens
        //      -Y is the distance down from the camera lens
        // Units of measurement are retained (and not assumed to be any particular
        // units) through this method

        bool GolfSimCamera::AdjustXYZDistancesForCameraAngles(const cv::Vec2d& camera_angles, 
                                                              const cv::Vec3d& original_distances, 
                                                              cv::Vec3d& adjusted_distances) {
            if (original_distances[kZ_index] == 0) {
                GS_LOG_MSG(error, "GolfSimCamera::AdjustXYZDistancesForCameraAngles received original Z distance of 0");
                return false;
            }

            GS_LOG_TRACE_MSG(trace, "X,Y camera angles (degrees) = " + std::to_string(camera_angles[kX_index]) + ", " + std::to_string(camera_angles[kY_index]));
            GS_LOG_TRACE_MSG(trace, "X,Y distances (meters) = " + std::to_string(original_distances[kX_index]) + ", " + std::to_string(original_distances[kY_index]));

            double camera_X_offset_for_tilt;
            double camera_Y_offset_for_tilt;

            SystemMode mode = GolfSimOptions::GetCommandLineOptions().system_mode_;

            if (mode == SystemMode::kCamera1 ||
                mode == SystemMode::kCamera1Calibrate || 
                mode == SystemMode::kCamera1TestStandalone ||
                mode == SystemMode::kCamera1BallLocation) {
                camera_X_offset_for_tilt = kCamera1XOffsetForTilt;
                camera_Y_offset_for_tilt = kCamera1YOffsetForTilt;
            }
            else {
                camera_X_offset_for_tilt = kCamera2XOffsetForTilt;
                camera_Y_offset_for_tilt = kCamera2YOffsetForTilt;
            }


            // X adjustment.  See Salmon notebook for diagram
            /*  This initial cut was a big fail
            double hypotenuse = sqrt( pow(original_distances[kX_index],2.) + pow(original_distances[kZ_index], 2.));

            double b_angle_radians = asin(original_distances[kX_index] / original_distances[kZ_index]);
            double a_prime_angle_radians = (kPi/2.) - (CvUtils::DegreesToRadians(camera_angles[kX_index]) + b_angle_radians);

            adjusted_distances[kZ_index] = hypotenuse * sin(a_prime_angle_radians) * cos(CvUtils::DegreesToRadians(camera_angles[kY_index]));
            adjusted_distances[kX_index] = hypotenuse * cos(a_prime_angle_radians) * cos(CvUtils::DegreesToRadians(camera_angles[kY_index]));

            GS_LOG_MSG(info, "X hypotenuse = " + std::to_string(hypotenuse) + ", b_angle_radians(X) = " +
                std::to_string(b_angle_radians) + ", a_prime_angle_radians(X) = " + std::to_string(a_prime_angle_radians));

            adjusted_distances[kX_index] += camera_X_offset_for_tilt;

            GS_LOG_MSG(info, "X = " + std::to_string(adjusted_distances[kX_index]));
            GS_LOG_MSG(info, "Z = " + std::to_string(adjusted_distances[kZ_index]));

            // Y adjustment
            hypotenuse = sqrt(pow(original_distances[kY_index], 2.) + pow(original_distances[kZ_index], 2.));

            b_angle_radians = atan(original_distances[kY_index] / original_distances[kZ_index]);
            a_prime_angle_radians = (kPi / 2.) + (CvUtils::DegreesToRadians(camera_angles[kY_index]) + b_angle_radians);

            GS_LOG_MSG(info, "Y hypotenuse = " + std::to_string(hypotenuse) + ", b_angle_radians(Y) = " + 
                        std::to_string(b_angle_radians) + ", a_prime_angle_radians(Y) = " + std::to_string(a_prime_angle_radians));


            adjusted_distances[kY_index] = hypotenuse * cos(a_prime_angle_radians);

            adjusted_distances[kY_index] += camera_Y_offset_for_tilt;

            GS_LOG_MSG(info, "Y = " + std::to_string(adjusted_distances[kY_index]) );
            */
            
            // Switch the coordinate system so taht the angles here are the angles AROUND the axis, not 
            // the angle IN the axis.  The configuation has X as left/right pan and Y as up/down tilt
            double camera_angle_y_radians = CvUtils::DegreesToRadians(camera_angles[kX_index]);
            double camera_angle_x_radians = CvUtils::DegreesToRadians(camera_angles[kY_index]);

            // Perform X-Axis rotation
            adjusted_distances[kY_index] = (original_distances[kY_index] * cos(camera_angle_x_radians)) -
                (original_distances[kZ_index] * sin(camera_angle_x_radians));

            adjusted_distances[kZ_index] = (original_distances[kY_index] * sin(camera_angle_x_radians)) +
                (original_distances[kZ_index] * cos(camera_angle_x_radians));

            // Perform Y-Axis rotation - NOTE - this re-uses and ajusts the Z distance already calculated just above
            adjusted_distances[kX_index] = (original_distances[kX_index] * cos(camera_angle_y_radians)) +
                (adjusted_distances[kZ_index] * sin(camera_angle_y_radians));

            adjusted_distances[kZ_index] = (adjusted_distances[kZ_index] * cos(camera_angle_y_radians)) -
                (original_distances[kX_index] * sin(camera_angle_y_radians));

            // TBD - Not certain this is useful - we can make up for the offset of the tilted camera from the
            // center of the system in other ways
            adjusted_distances[kX_index] += camera_X_offset_for_tilt;
            adjusted_distances[kY_index] += camera_Y_offset_for_tilt;

            return true;
        }



        // The ball's direct distance to the lens, as well as the x,y coordinates from the picture center
        // origin both have to be set BEFORE calling this method.
        // Axes are as perceived by the camera -- z is close/far, x is left/right, and y is up/down
        // NOTE that the Z distance is the line-of-sight distance from the lens to the ball.
        bool GolfSimCamera::ComputeXyzDistanceFromOrthoCamPerspective(const GolfSimCamera& camera, const GolfBall& b1, cv::Vec3d& distances) {

            if (std::abs(b1.distance_to_z_plane_from_lens_) <= 0.0001) {
                LoggingTools::Warning("ComputeXyzDistanceFromOrthoCamPerspective called without setting the ball line-of-sight-distance");
                return false;
            }

            // First calculate the distances as if the camera was facing straight ahead toward 
            // the ball flight plane

            double xFromCameraCenter = b1.x() - std::round(camera.camera_hardware_.resolution_x_ / 2.0);
            double yFromCameraCenter = b1.y() - std::round(camera.camera_hardware_.resolution_y_ / 2.0);

            cv::Vec3d camera_perspective_distances;

            // Direct-to-ball-PLANE distance is already in real-world meters.   
            // However, we do not have the exact direct-to-ball distance due to the lens.
            // We will figure out the Z axis distance (which will generally be a little shorter) first.
            double xDistanceFromCamCenter = convertXDistanceToMeters(camera, b1.distance_to_z_plane_from_lens_, xFromCameraCenter);
            camera_perspective_distances[0] = xDistanceFromCamCenter;  // X distance, negative means to the left of the camera
            
            double yDistanceFromCamCenter = convertYDistanceToMeters(camera, b1.distance_to_z_plane_from_lens_, yFromCameraCenter);

            camera_perspective_distances[1] = -yDistanceFromCamCenter;  // Y distance, positive is upward (smaller Y values)  // TBD - sqrt(pow(b1.distance_to_z_plane_from_lens_, 2) - pow(yDistanceFromCamCenter, 2));  // Y distance.  Positive values are above the camera center

            camera_perspective_distances[2] = b1.distance_to_z_plane_from_lens_;// FOR NON_DIRECT sqrt(pow(b1.distance_to_z_plane_from_lens_, 2) - pow(xDistanceFromCamCenter, 2));  // Z distance.  Only positive values in front of camera

            GS_LOG_TRACE_MSG(trace, "GolfSimCamera::ComputeXyzDistanceFromOrthoCamPerspective computed camera_perspective_distances of: " +
                std::to_string(camera_perspective_distances[0]) + ", " +
                std::to_string(camera_perspective_distances[1]));

            // If the camera were pointed straight out, the above is all we would need to have in 
            // order to compute the x,y,z position of the ball.  The ball would be at the same z-distance,
            // and the x and y distances would just have to be added/subtracted to the point in space
            // directly out from the camera.
            // 
            // However, because the camera is at an angle, we need to convert the x,y,z distances from the
            // camera's perspective into x,y,z from a perspective that is orthogonal to the launch monitor.
            // This will entail a polar (or spherical) coordinate system to a cartesian (x,y,z) conversion
            // So, Convert the distances from the camera into a set of angles from the camera's perspective

            // Using the adjusted X and Y distances (lined up with the real world up/down and left/right),
            // determine the angles of the ball from the camera perspective
            // Positive X degrees is to the left looking out the camera
            // Negative Y degrees is tilting down looking out the camera
            cv::Vec2d deltaAnglesCameraPerspective;
            deltaAnglesCameraPerspective[0] = -CvUtils::RadiansToDegrees(atan(camera_perspective_distances[0] / b1.distance_to_z_plane_from_lens_));
            deltaAnglesCameraPerspective[1] = CvUtils::RadiansToDegrees(atan(camera_perspective_distances[1] / b1.distance_to_z_plane_from_lens_));

            // Account for the angle of the camera, which will adjust the camera perspective angles
            // to the real-world orthogonal-to-the-LM-perspective polar coordinates.
            // X angle here is positive in a counter-clockwise movement looking down at the LM from above
            // Y angle is negative as the azimuth angle goes down from horizontal
            cv::Vec2d deltaAnglesLMPerspective;
            deltaAnglesLMPerspective[0] = camera.camera_hardware_.camera_angles_[0] + deltaAnglesCameraPerspective[0] ;
            deltaAnglesLMPerspective[1] = camera.camera_hardware_.camera_angles_[1] + deltaAnglesCameraPerspective[1];

            GS_LOG_TRACE_MSG(trace, "GolfSimCamera::ComputeXyzDistanceFromOrthoCamPerspective computed (LM-perspective) X,Y angles of: " + 
                                        std::to_string(deltaAnglesLMPerspective[0]) + ", " +
                                        std::to_string(deltaAnglesLMPerspective[1]));

            // Second, figure out the X, Y, and Z distances from the LM's perspective
            // Theta is the rotation in the floor plane
            // Phi is the rotation down/away from the vertical
            // This is essentially a polar-coordinate system to cartesian system conversion
            // See https://math.libretexts.org/Courses/Mount_Royal_University/MATH_2200%3A_Calculus_for_Scientists_II/7%3A_Vector_Spaces/5.7%3A_Cylindrical_and_Spherical_Coordinates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,y2%2Bz2).

            double phi_radians = CvUtils::DegreesToRadians( 90. + deltaAnglesLMPerspective[1] );
            double p_rho = camera_perspective_distances[2];
            double theta_radians = CvUtils::DegreesToRadians(deltaAnglesLMPerspective[0]);
            // Intermediate results for precision testing - ignore
            double sin_phi = sin(phi_radians);
            double cos_theta = cos(theta_radians);
            double sin_theta = sin(theta_radians);

            double cartesian_x = p_rho * sin(phi_radians) * cos(theta_radians);
            double cartesian_y = p_rho * sin(phi_radians) * sin(theta_radians);
            double cartesian_z = p_rho * cos(phi_radians);

            // Convert from the model cartesian system into the one used by the launch monitor
            distances[0] = -cartesian_y;
            distances[1] = -cartesian_z;
            distances[2] = cartesian_x;

            return true;
        }

        // The delta angles are the angles between the two balls, in either the camera's position,
        // or, alternatively, the ball's position (i.e., looking down-range)
        bool GolfSimCamera::getXYDeltaAnglesBallPerspective(const cv::Vec3d& position_deltas_ball_perspective,
            cv::Vec2d& deltaAnglesBallPerspective) {

            // Deal with case where the ball may not have moved (or some other problem occurred).  
            // In this case, just return 0's.
            if (std::abs(position_deltas_ball_perspective[2]) <= 0.001) {
                GS_LOG_MSG(error, "getXYDeltaAnglesBallPerspective:  b2.distance_to_z_plane_from_lens_ was 0!");
                deltaAnglesBallPerspective = (0, 0);
                return true;   // Don't error out on this
            }

            // TBD - determine the angles from the perspective of the camera?
            // Determine from perspective of the camera x-axis, looking in the positive direction (the ball's
            // most natural perspective).

            // Negative degrees means clockwise looking down the z axis

            // X angle (up/down) = arctan(z/x) from ball perspective
            deltaAnglesBallPerspective[0] = CvUtils::RadiansToDegrees(atan(position_deltas_ball_perspective[0] / position_deltas_ball_perspective[2]));
            // Y angle (left/right) = arctan(y/xf)
            deltaAnglesBallPerspective[1] = CvUtils::RadiansToDegrees(atan((position_deltas_ball_perspective[1] / position_deltas_ball_perspective[2])));

            return true;
        }


        bool GolfSimCamera::ComputeBallXYAnglesFromCameraPerspective(const cv::Vec3d& distances_camera_perspective,
            cv::Vec2d& deltaAnglesCameraPerspective) {

            if (distances_camera_perspective[2] < 0.0001) {
                GS_LOG_MSG(error, "ComputeBallXYAnglesFromCameraPerspective:  b2.distance_to_z_plane_from_lens_ was 0!");
                return false;
            }

            /* First version is for when the distances_camera_perspective[2] was the direct-to-ball distance instead of just the z plane
            // Positive X angle is counter-clockwise looking down on the camera/ball from above
            deltaAnglesCameraPerspective[0] = -CvUtils::RadiansToDegrees(asin(distances_camera_perspective[0] / distances_camera_perspective[2]));
            double directDistance = sqrt(pow(distances_camera_perspective[2], 2) + pow(distances_camera_perspective[0], 2));
            deltaAnglesCameraPerspective[1] = -CvUtils::RadiansToDegrees(atan(-distances_camera_perspective[1] / directDistance));
            */

            // Positive X angle is counter-clockwise looking down on the camera/ball from above
            // Positive Y angle is looking up from level to the ball
            deltaAnglesCameraPerspective[0] = CvUtils::RadiansToDegrees(atan(distances_camera_perspective[0] / distances_camera_perspective[2]));
            deltaAnglesCameraPerspective[1] = -CvUtils::RadiansToDegrees(atan(-distances_camera_perspective[1] / distances_camera_perspective[2]));

            return true;
        }

        bool  GolfSimCamera::prepareToTakeVideo() {
            return camera_hardware_.prepareToTakeVideo();
        }

        bool  GolfSimCamera::prepareToTakePhoto() {
            camera_hardware_.prepareToTakePhoto();
            return true;
        }

        cv::Mat  GolfSimCamera::getNextFrame() {
            return camera_hardware_.getNextFrame();
        }

        bool GolfSimCamera::ShowAndLogBalls(const std::string& title, 
                                            const cv::Mat& img, 
                                            std::vector<GolfBall>& balls, 
                                            bool log_image_to_file,
                                            const int middle_ball_index, 
                                            const int second_ball_index ) {

            // It's expensive to clone an image, so make sure we're here to do at least something
            if (!log_image_to_file && 
                !GolfSimOptions::GetCommandLineOptions().show_images_ && 
                GolfSimOptions::GetCommandLineOptions().artifact_save_level_ != ArtifactSaveLevel::kAll) {
                return true;
            }

            cv::Mat ball_image = img.clone();

            // Outline the final candidates for this image 
            for (size_t i = 0; i < balls.size(); i++) {
                GolfBall& b = balls[i];
                GsCircle& c = b.ball_circle_;

                std::string label;

                if (i == (size_t)middle_ball_index) {
                    label = std::to_string(i) + "(Mid)";
                }
                else if (i == (size_t)second_ball_index) {
                    label = std::to_string(i) + "(2nd)";
                } else {
                    label = std::to_string(i);
                }

                LoggingTools::DrawCircleOutlineAndCenter(ball_image, c, label);
            }

            LoggingTools::DebugShowImage(title, ball_image);

            if (log_image_to_file && GolfSimOptions::GetCommandLineOptions().artifact_save_level_ == ArtifactSaveLevel::kAll) {
                LoggingTools::LogImage("", ball_image, std::vector < cv::Point >{}, true, title + ".png");
            }

            return true;
        }

        void GolfSimCamera::SortBallsByXPosition(std::vector<GolfBall>& balls) {

            if (GolfSimOptions::GetCommandLineOptions().golfer_orientation_ == GolferOrientation::kRightHanded) {
                std::sort(balls.begin(), balls.end(), [](const GolfBall& a, const GolfBall& b)
                    { return (a.x() < b.x()); });
            }
            else {
                std::sort(balls.begin(), balls.end(), [](const GolfBall& a, const GolfBall& b)
                    { return (a.x() > b.x()); });
            }

        }

        int GolfSimCamera::GetMostCenteredBallIndex(const std::vector<GolfBall>& balls, const int ball_to_ignore_index) {

            if (balls.size() < 1) {
                GS_LOG_TRACE_MSG(warning, "GetMostCenteredBallIndex - initial_balls vector was empty.  Exiting function.");
                return -1; 
            }

            // Randomly pick one ball as the current, initial candidate
            int most_centered_ball_index = -1;
            int smallest_distance_from_center = 10 * camera_hardware_.resolution_x_;   // Ensure first ball will be closer to the center

            // Loop through the balls, but ignore the ball_to_ignore if it is set (will otherwise be -1)
            for (size_t i = 0; i < balls.size(); i++) {

                if (i == (size_t)ball_to_ignore_index) {
                    continue;
                }

                const GolfBall& b = balls[i];

                int x_distance = (int)(std::abs(CvUtils::CircleX(b.ball_circle_) - (camera_hardware_.resolution_x_ / 2.)));
                int y_distance = (int)(std::abs(CvUtils::CircleY(b.ball_circle_) - (camera_hardware_.resolution_y_ / 2.)));

                int distance_from_center = (int)std::round(std::sqrt(x_distance * x_distance + y_distance * y_distance));


                if (distance_from_center < smallest_distance_from_center) {
                    most_centered_ball_index = (int)i;
                    smallest_distance_from_center = distance_from_center;

                    GS_LOG_TRACE_MSG(trace, "GetMostCenteredBallIndex - Best current candidate with distance from center of " +
                        std::to_string(distance_from_center) + " was: \n" + b.Format());
                }
            }

            return most_centered_ball_index;
        }


        bool GolfSimCamera::GetBallDistancesAndRatios(const std::vector<GolfBall>& balls,
                                                            std::vector<double>& distances,
                                                            std::vector<double>& distance_ratios) {

            if (balls.size() < 1) {
                GS_LOG_TRACE_MSG(warning, "GetBallDistancesAndRatios - balls vector was empty.  Exiting function.");
                return false;
            }

            // First get the inter-ball distances.  There will be one less distance element
            // than the number of balls.
            // "size()-1" because we need at least two balls for a single inter-ball distance
            for (size_t ball_index = 0; ball_index < balls.size() - 1; ball_index++) {

                const GolfBall& left_ball =  balls[ball_index];
                const GolfBall& right_ball = balls[ball_index + 1];

                double distance = left_ball.PixelDistanceFromBall(right_ball);

                distances.push_back(distance);
            }

            // There will be one less distance ratio than distances in a perfect world.
            // But there may be times when one of the circles is dropped and we have a lot fewer
            // distances
            for (size_t distance_index = 0; distance_index < distances.size() - 1; distance_index++) {

                double left_distance =  distances[distance_index];
                double right_distance = distances[distance_index + 1];

                // Account for friction forces that would tend to decrease the ideal distance
                // that would have occured with a constant-velocity assumption
                right_distance = AdjustDistanceForSlowing(right_distance);

                if (left_distance <= 1.0) {
                    LoggingTools::Warning("Found invalid (<1.0) distance");
                    return false;
                }
                double distance_ratio = right_distance / left_distance;

                distance_ratios.push_back(distance_ratio);
            }

            return true;
        }

        // Look at the balls around the two identified balls to determine (if possible) which
        // of the two balls is most likely to be on the track-line (really more of an arc) that appears
        // to be defined by the rest of the balls.  The found ball may be a false positive that
        // just happened not to be filtered by other techniques.
        // If true is returned, then off_track_ball_index will point to the ball that is least likely
        // to be part of the line of flight.
        // The balls must be sorted from left to right by their x coordinate, with higher indexes
        // pointing to balls with greater-or-equal x positions than lower indexes.
        // candidate_ball_index_1 must be < candidate_ball_index_2
        bool GolfSimCamera::FindBestBallOnLineOfFlight(const std::vector<GolfBall>& balls,
                                                       const int candidate_ball_index_left,
                                                       const int candidate_ball_index_right,
                                                       double& ball_1_distance,
                                                       double& ball_2_distance,
                                                       const GolfBall& line_ball1, 
                                                       const GolfBall& line_ball2) {


            /* This was the original code that used the balls around the ball being analyzed to determine the line
            if (balls.size() <= 3) {
                // Definitely not enough balls to figure out the line of flight
                return false;
            }
            int right_point_index = -1;
            int left_point_index = -1;

            // Determine the end points of the line of flight if we can.
            if (candidate_ball_index_left == 0) {
                // Left ball is all the way to the left of the ball vector (first index)
                // We can't find a ball to the left, so maybe we can find two
                // balls to the right to define the line of flight

                if (candidate_ball_index_right < (int)balls.size() - 2) {
                    // At least two balls exist to the right, so we can use those
                    // balls as anchors on the line of flight
                    left_point_index = candidate_ball_index_right + 1;
                    right_point_index = candidate_ball_index_right + 2;
                }
            }
            else if (candidate_ball_index_right == (int)balls.size() - 1) {
                // Right ball is all the way to the right of the ball vector (last index)
                // We can't find two balls to the right, so maybe we can find two
                // balls to the left to define the line of flight

                if (candidate_ball_index_left > 1) {
                    // At least two balls exist to the left, so we can use those
                    // balls as anchors on the line of flight
                    left_point_index = candidate_ball_index_left - 2;
                    right_point_index = candidate_ball_index_left - 1;
                }
            }
            else if (candidate_ball_index_left > 0 && candidate_ball_index_right < balls.size() - 1) {
                left_point_index = candidate_ball_index_left - 1;
                right_point_index = candidate_ball_index_right + 1;
            }

            if (candidate_ball_index_left < 0 || candidate_ball_index_right < 0 ) {
                // Were not able to find two anchor balls
                return false;
            }

            // We have enough points to define a line-of-flight
            const GolfBall& ball1 = balls[candidate_ball_index_left];
            const GolfBall& ball2 = balls[candidate_ball_index_right];
            const GolfBall& left_line_ball = balls[left_point_index];
            const GolfBall& right_line_ball = balls[right_point_index];

            ball_1_distance = GetPerpendicularDistanceFromLine(ball1.x(), ball1.y(), left_line_ball.x(), left_line_ball.y(), right_line_ball.x(), right_line_ball.y());
            ball_2_distance = GetPerpendicularDistanceFromLine(ball2.x(), ball2.y(), left_line_ball.x(), left_line_ball.y(), right_line_ball.x(), right_line_ball.y());
            */

            // We have enough points to define a line-of-flight

            // The new code defines the trajectory as being between the two best balls
            const GolfBall& ball1 = balls[candidate_ball_index_left];
            const GolfBall& ball2 = balls[candidate_ball_index_right];

            ball_1_distance = GetPerpendicularDistanceFromLine(ball1.x(), ball1.y(), line_ball1.x(), line_ball1.y(), line_ball2.x(), line_ball2.y());
            ball_2_distance = GetPerpendicularDistanceFromLine(ball2.x(), ball2.y(), line_ball1.x(), line_ball1.y(), line_ball2.x(), line_ball2.y());

            return true;
        }

        // xc, yc is designates the target point and xa, ya to xb, yb designates the 
        // line segment that goes through x1, y1, and x2, y2.
        double GolfSimCamera::GetPerpendicularDistanceFromLine(double xc, double yc, double xa, double ya, double xb, double yb) {

            // See, e.g., https://math.stackexchange.com/questions/2757318/distance-between-a-point-and-a-line-defined-by-2-points
            // The following was only for a line SEGMENT: https://stackoverflow.com/questions/849211/shortest-distance-between-a-point-and-a-line-segment
            
            // If the line is vertical, then the distance is just the x difference to the line
            if (std::abs(xb - xa) < 0.0001) {
                return (std::abs(xc - xb));
            }

            // If the line is horizontal, then the distance is just the y difference to the line
            if (std::abs(yb - ya) < 0.0001) {
                return (std::abs(yc - yb));
            }

            double nA = xb - xa;
            double nB = yc - ya;
            double nC = yb - ya;
            double nD = xc - xa;

            double numerator = std::abs(nA * nB - nC * nD);

            double dA = xb - xa;
            double dB = yb - ya;

            double denominator = sqrt(dA * dA + dB * dB);

            return numerator / denominator;
        }

        void GolfSimCamera::RemoveLowScoringBalls(std::vector<GolfBall>& balls, const int max_balls_to_retain) {

            int adjusted_max_balls_to_retain = max_balls_to_retain;

            if (adjusted_max_balls_to_retain >= (int)balls.size()) {
                GS_LOG_TRACE_MSG(trace, "RemoveLowScoringBalls asked to remove more balls than were identified.  max_balls_to_retain= " + 
                                    std::to_string(max_balls_to_retain) + ", but only have " + std::to_string(balls.size()) + " balls.");
                return;
            }

            int original_number_balls = (int)balls.size();
            int ball_to_delete = original_number_balls - 1;
            for (int i = 0; i < original_number_balls - adjusted_max_balls_to_retain; i++) {
                balls.erase(balls.begin() + ball_to_delete);
                ball_to_delete--;
            }
        }


        void GolfSimCamera::RemoveUnlikelyRadiusChangeBalls(std::vector<GolfBall>& initial_balls, 
                                                            const double max_change_percent,
                                                            const double max_overlapped_ball_radius_change_ratio,
                                                            const bool preserve_high_quality_balls) {

            if (initial_balls.size() < 3) {
                GS_LOG_TRACE_MSG(trace, "GolfSimCamera::RemoveUnlikelyRadiusChangeBalls found too few (< 3) balls.  Not processing anything.");
                return;
            }

            // We should never drop the <n> best balls
            uint kNumberHighQualityBallsToRetain_ = 2;

            // Identify any balls that are outside the expected radius range by retaining them only in the initial ball vector
            for (int i = (int)initial_balls.size() - 3; i >= 0; i--) {
                double b1_radius = initial_balls[i].measured_radius_pixels_;
                double b2_radius = initial_balls[i + 1].measured_radius_pixels_;
                double b3_radius = initial_balls[i + 2].measured_radius_pixels_;

                double middle_to_right_ball_proximity_pixels = initial_balls[i + 1].PixelDistanceFromBall(initial_balls[i + 2]);
                double middle_to_left_ball_proximity_pixels = initial_balls[i].PixelDistanceFromBall(initial_balls[i + 1]);

                double  middle_to_right_distance_adjustment = (middle_to_right_ball_proximity_pixels / 150.0) / 100.0;
                double  middle_to_left_distance_adjustment = (middle_to_left_ball_proximity_pixels / 150.0) / 100.0;

                if ((b2_radius > (b1_radius * (1.0 + max_change_percent/ 100. + middle_to_left_distance_adjustment)) &&
                    b2_radius > (b3_radius * (1.0 + max_change_percent / 100. + middle_to_right_distance_adjustment)))    ||
                    (b2_radius < (b1_radius * (1.0 - max_change_percent / 100. - middle_to_left_distance_adjustment)) &&
                        b2_radius < (b3_radius * (1.0 - max_change_percent / 100. - middle_to_right_distance_adjustment))) ) {

                    if (initial_balls[i + 1].quality_ranking >= kNumberHighQualityBallsToRetain_) {
                        GS_LOG_TRACE_MSG(trace, "RemoveUnlikelyRadiusChangeBalls removing ball " + std::to_string(i + 1) + " because it was too much smaller/larger than both adjacent balls.");
                        initial_balls.erase(initial_balls.begin() + i + 1);
                    }
                    else {
                        GS_LOG_TRACE_MSG(trace, "RemoveUnlikelyRadiusChangeBalls NOT removing ball " + std::to_string(i + 1) + " because although it was larger than both adjacent balls, it was a high-quality circle.");
                    }
                    // Also, if the middle ball is already overlapping with the ball to the left,
                    // then it's likely that ALL the balls from the middle ball to the left-most
                    // are all overlapped
                    // TBDXXX - Consider getting rid of everything to the left??
                }
                else {
                    // If not, is the outer of the three balls different enough to discard
                    double left_radius_change = std::abs(b2_radius - b1_radius);
                    double right_radius_change = std::abs(b3_radius - b2_radius);

                    // Are the rightmost two balls really close when the others are not
                    if (middle_to_right_ball_proximity_pixels < b3_radius  &&
                        middle_to_right_ball_proximity_pixels < middle_to_left_ball_proximity_pixels / 2) {

                        // The right-most ball shouldn't have changed in size this much when
                        // it hasn't moved very far.  Likely it's a mis-identification
                        if (right_radius_change > max_overlapped_ball_radius_change_ratio * left_radius_change) {
                            if (initial_balls[i + 2].quality_ranking >= kNumberHighQualityBallsToRetain_ ||
                                preserve_high_quality_balls == false) {
                                GS_LOG_TRACE_MSG(trace, "RemoveUnlikelyRadiusChangeBalls removing ball " + std::to_string(i + 2) + " because it was much larger/smaller than the ball it overlaps.");
                                initial_balls.erase(initial_balls.begin() + i + 2);
                            }
                        }
                    }


                    // Are the leftmost two balls really close?
                    if (middle_to_left_ball_proximity_pixels < b1_radius &&
                        middle_to_left_ball_proximity_pixels < middle_to_right_ball_proximity_pixels / 2) {

                        // The left-most ball shouldn't have changed in size this much when
                        // it hasn't moved very far.  Likely it's a mis-identification
                        if (left_radius_change > max_overlapped_ball_radius_change_ratio * right_radius_change) {
                            if (initial_balls[i].quality_ranking > kNumberHighQualityBallsToRetain_ - 1 ||
                                preserve_high_quality_balls == false) {
                                GS_LOG_TRACE_MSG(trace, "RemoveUnlikelyRadiusChangeBalls removing ball " + std::to_string(i) + " because it was much larger/smaller than the ball it overlaps.");
                                initial_balls.erase(initial_balls.begin() + i);
                            }
                        }
                    }
                }
            }
        }


        void GolfSimCamera::RemoveOffTrajectoryBalls(std::vector<GolfBall>& initial_balls, 
                                                     const double max_distance_from_trajectory, 
                                                     const GolfBall& best_ball,
                                                     const GolfBall& second_best_ball ) {

            if (initial_balls.size() < 1) {
                GS_LOG_TRACE_MSG(warning, "RemoveOffTrajectoryBalls - balls vector was empty.  Exiting function.");
                return;
            }

            // Identify any balls that are far from the projected trajectory
            for (int i = (int)initial_balls.size() - 1; i >= 0; i--) {
                GolfBall& b = initial_balls[i];

                // Don't both examining the two balls we're using to draw the trajectory line
                if (b.quality_ranking == best_ball.quality_ranking ||
                    b.quality_ranking == second_best_ball.quality_ranking ) {
                    continue;
                }

                double ball_distance = GetPerpendicularDistanceFromLine(b.x(), b.y(), best_ball.x(), best_ball.y(), second_best_ball.x(), second_best_ball.y());

                if (ball_distance > max_distance_from_trajectory) {
                    // GS_LOG_TRACE_MSG(trace, "Not analyzing ball " + std::to_string(i) + " due to it having off - trajectory distance of : " + std::to_string(ball_distance));
                    initial_balls.erase(initial_balls.begin() + i);
                }
            }
        }


        void GolfSimCamera::RemoveNearbyPoorQualityBalls(std::vector<GolfBall>& initial_balls,
                                                         const double max_ball_proximity,
                                                         const int max_quality_difference) {

            if (initial_balls.size() < 1) {
                GS_LOG_TRACE_MSG(warning, "RemoveNearbyPoorQualityBalls - balls vector was empty.  Exiting function.");
                return;
            }

            // Examine each of the search balls and remove any other balls that are both
            // much worse in quality and nearby the search ball

            std::vector<GolfBall> balls_copy = initial_balls;

            for (size_t outer_index = 0; outer_index < balls_copy.size(); outer_index++) {

                GolfBall& current_ball = balls_copy[outer_index];

                for (int i = (int)initial_balls.size() - 1; i > (int)outer_index; i--) {
                    GolfBall& b = initial_balls[i];

                    double ball_distance = current_ball.PixelDistanceFromBall(b);
                    int quality_difference = b.quality_ranking - current_ball.quality_ranking;

                    if (ball_distance < max_ball_proximity && quality_difference > max_quality_difference) {
                        GS_LOG_TRACE_MSG(trace, "Not analyzing ball " + std::to_string(i) + " due to its proximity of : " 
                                    + std::to_string(ball_distance) + " and poor quality of " + std::to_string(b.quality_ranking));
                        initial_balls.erase(initial_balls.begin() + i);
                    }
                }
            }
        }

        uint GolfSimCamera::RemoveOverlappingBalls(const std::vector<GolfBall>& initial_balls, 
                                                   const double ball_proximity_margin_percent,
                                                   const bool attempt_removal_of_off_trajectory_balls,
                                                   std::vector<GolfBall>& return_balls, 
                                                   const GolfBall& best_ball, 
                                                   const GolfBall& second_best_ball,
                                                   const bool preserve_high_quality_balls) {

            if (initial_balls.size() < 1) {
                GS_LOG_TRACE_MSG(warning, "RemoveOverlappingBalls - balls vector was empty.  Exiting function.");
                return -1;
            }

            uint number_removed = 0;

            // We assume that the strobe intervals either constant or increasing in time/distance.
            // Start with the ball that is most likely to be in the clear, and then go toward the tee
            // until the intervals are so short that the ball images overlap.
            // The loop iterates right-to-left in the right-hand case.
            // TBD - What about left-handed??
            for (int i = (int)initial_balls.size() - 1; i >= 0; i--) {
                const GolfBall& ball = initial_balls[i];

                if (i == 0) {
                    // We have reached the closest ball to the tee in the vector
                    // There are no more balls to compare X-position with,
                    // and the loop did not drop out on the last iteration, so there was no overlap with this ball,
                    // so retain the current ball and the one to it's left and stop the iteration
                    return_balls.push_back(ball);
                    break;
                }

                const  GolfBall& next_closer_ball = initial_balls[i - 1];
                double ball_proximity_pixels = ball.PixelDistanceFromBall(next_closer_ball);
                double proximity_limit = ((1. - ball_proximity_margin_percent / 100.) * (next_closer_ball.measured_radius_pixels_ + ball.measured_radius_pixels_));

                if (ball_proximity_pixels < proximity_limit) {

                    if (attempt_removal_of_off_trajectory_balls) {

                        // The next ball closer to the tee is too close to the ball we are examining
                        // Thus, BOTH balls (including the 'current' ball) are overlapping and may have to be 
                        // ignored for the purpose of for example, spin analysis

                        // However, if we can determine that one of the balls is clearly a false positive, such
                        // as because that ball is clearly off the line-of-flight defined by the other balls, then
                        // we can just drop the false positive and keep the other ball.
                        double ball_1_distance = -1;
                        double ball_2_distance = -1;

                        FindBestBallOnLineOfFlight(initial_balls, i - 1, i, ball_1_distance, ball_2_distance, best_ball, second_best_ball);

                        // If both balls are on the trajectory (or really close), then assume they were both valid and remove both of them.
                        // Otherwise, assume one was a mis-identification and remove only it
                        // TBD - We might even want to increase the maximum off-trajectory now that we're doing 
                        // quite a bit of trajectory checks before this?
                        int kMaximumOffTrajectoryDistance_ = 8;

                        // The ground can cause a lot of bounch up & down on the balls, so
                        // make sure we don't get rid of a good ball just because it moved a bit.
                        if (GolfSimClubs::GetCurrentClubType() == GolfSimClubs::kPutter) {
                            kMaximumOffTrajectoryDistance_ = 23;
                        }

                        uint kNumberHighQualityBallsToRetain_ = 2;

                        if (ball_1_distance < kMaximumOffTrajectoryDistance_ && ball_2_distance < kMaximumOffTrajectoryDistance_) {
                            // This appears to be an overlap of two actual balls
                            // Effectively get rid of both the current (overlapped) ball and the one to the left
                            // by skipping to the next ball to the left (if it exists).  They are both unlikely to be
                            // useful for spin analysis (and possibly position) because of the overlap

                            // However, do not get rid of any high-ranked ball

                            if (ball.quality_ranking < kNumberHighQualityBallsToRetain_ &&
                                preserve_high_quality_balls == true) {
                                // Leave the right-most ball (index i) alone and move ahead
                                // to the next one to the left
                                return_balls.push_back(ball);
                                i--;
                                number_removed++;                                
                                continue;
                            }
                            else if (next_closer_ball.quality_ranking < kNumberHighQualityBallsToRetain_ &&
                                preserve_high_quality_balls == true) {
                                // Preserve the left-most ball by simply skipping inserting the right-most
                                // ball in the return vector.  Assume the right-most is not a 'real' ball.
                                continue;
                            }
                            else {
                                // Get rid of both balls
                                i--;
                                number_removed += 2;

                                // special case - if we got rid of both balls and there's only one more ball
                                // that we would be looking at, there's no way to compare that ball to the
                                // ones we have just removed.  But, knowing that the spacing is even closer
                                // as we move to the left, we'll just effectively remove that last ball as well
                                // since it likely overlapped with the current left-side ball.
                                if (i == 1) {
                                    break;
                                }
                                else {
                                    continue;
                                }
                            }
                        }
                        else {
                            // At least one of the balls is a misidentified ball.  Assume one ball is real.
                            // Get rid of the ball that was furthest from the assumed line of flight
                            // unless that ball is one of the highest-ranked, in which case, lose the other one.
                            // The off-track ball is the one that is furthest from the line defined by the end points determined earlier
                            if (ball_1_distance > ball_2_distance) {
                                // The next ball to the left was the ball that is furthest from the line of flight
                                // Save the current ball (to the right of the other) and effectively skip the other
                                // We think that we only removed ONE real ball, however

                                return_balls.push_back(ball);
                                i--;
                                number_removed++;
                                continue;
                            }
                            else {
                                // The next ball to the left was the ball that is closest to the line of flight
                                // Effectively skip the current ball and move on to looking at the next ball to the left
                                // In this case, we don't believe we've removed a real ball, so don't count it
                                continue;
                            }
                        }
                    }
                    else {
                        // we are not allowing for avoiding removing a ball if it is overlapped 
                        // with an off-trajectory ball.  So just get rid of both
                        i--;
                        number_removed += 2;
                        // See speciai case comment above for an explanation for potentially breaking out of the loop here
                        if (i == 1) {
                            break;
                        }
                        else {
                            continue;
                        }
                    }
                }

                // The current ball was (visually) free and clear.  So retain it on the final ball list.
                return_balls.push_back(ball);
            }

            // The balls went in furthest-from-tee first, so resort the opposite way
            SortBallsByXPosition(return_balls);

            return number_removed;
        }

        // DEPRECATED
        void GolfSimCamera::RemoveTooSmallOrBigBalls(std::vector<GolfBall>& initial_balls,
                                                     const GolfBall &expected_best_ball) {

            if (initial_balls.size() < 1) {
                GS_LOG_TRACE_MSG(warning, "RemoveTooSmallOrBigBalls - balls vector was empty.  Exiting function.");
                return;
            }

            // Other, valid, strobed balls should have similar radii
            // TBD - What about very hooked/sliced shots?  Would their radii change more?
            const double kMinStrobedBallRadiusRation = 0.80;
            const double kMaxStrobedBallRadiusRation = 1.20;

            int min_strobed_ball_radius = int(expected_best_ball.measured_radius_pixels_ * kMinStrobedBallRadiusRation);
            int max_strobed_ball_radius = int(expected_best_ball.measured_radius_pixels_ * kMaxStrobedBallRadiusRation);

            // Identify any balls that are outside the expected radius range by retaining them only in the initial ball vector
            for (int i = (int)initial_balls.size() - 1; i >= 0 ;i--) {
                GolfBall& b = initial_balls[i];

                double radius = b.measured_radius_pixels_;

                if (radius < min_strobed_ball_radius ||
                    radius > max_strobed_ball_radius) {
                    GS_LOG_TRACE_MSG(trace, "  Not analyzing found ball due to it having radius = {" + std::to_string(radius));
                    initial_balls.erase(initial_balls.begin() + i);
                }
            }
        }

        void GolfSimCamera::DetermineSecondBall(std::vector<GolfBall>& return_balls, 
                                                const int most_centered_ball_index,
                                                int &second_ball_index) {

            GolfBall& face_ball = return_balls[most_centered_ball_index];
            
            // One question is how to determine which OTHER ball should be used to compare with the face_ball
            // Should it be the nearest or the furthest?  Closest to the center (other than the middle ball)?
            // Answer:  We will focus on the spin analysis
            // Most centered will be better to compare for spin, as the face-on angle will be the
            // most similar.  For high speed spins, the closer the ball images, the higher
            // the recoverable speed, because the ball doesn't have as much time to spin.

            second_ball_index = GetMostCenteredBallIndex(return_balls, most_centered_ball_index);
            return;
        }

        void GolfSimCamera::RemoveUnlikelyAngleLowerQualityBalls(std::vector<GolfBall>& initial_balls) {

            // Note - the balls must have been ordered in quality order before calling this method.

            GS_LOG_TRACE_MSG(trace, "GolfSimCamera::RemoveUnlikelyAngleLowerQualityBalls");

            if (initial_balls.size() < 2) {
                GS_LOG_TRACE_MSG(warning, "initial_balls vector was empty or had only 1 ball.  Exiting function.");
                return;
            }

            size_t number_exposures_to_analyze = kNumberAngleCheckExposures;
            // Make sure we're not trying to check more exposures than we have
            if (number_exposures_to_analyze >= initial_balls.size() - 1) {
                number_exposures_to_analyze = initial_balls.size() - 1;
            }

            // Examine each of the search balls and remove any near-by balls that are at an unreasonable angle.
            // This process takes care of the (likely) situation when the top (position 0) quality ball is
            // near another high-quality ball (e.g., position 1), but the second ball is a mistake and is
            // at a weird angle below/above the higher-quality ball.

            std::vector<GolfBall> balls_copy = initial_balls;

            // This index should point to the highest-quality ball
            size_t outer_index = 0;

            while ( (outer_index < initial_balls.size() - 1) && (initial_balls.size() > 0) ) {

                GolfBall& current_ball = initial_balls[outer_index];

                for (size_t i = initial_balls.size() - 1; (initial_balls.size() > 0) && (i > outer_index); i--) {
                    GolfBall& b = initial_balls[i];

                    double ball_angle_degrees = 0;

                    // TBD - This is only an approximation.  It might not work at very high
                    // camera in(de)clinations

                    int x_distance_pixels = std::abs(b.x() - current_ball.x());

                    if (x_distance_pixels > kUnlikelyAngleMinimumDistancePixels) {
                        // The balls are too far apart to want to check for unlikely angles
                        continue;
                    }
                    else if (x_distance_pixels == 0 && b.y() == current_ball.y()) {
                        // The balls are concentric, so don't do anything
                        continue;
                    }
                    else if (x_distance_pixels < 0.001) {
                        // GS_LOG_TRACE_MSG(trace, "RemoveUnlikelyAngleLowerQualityBalls not analyzing ball " + std::to_string(i) + " because its X coordinate is too far from ball number " + std::to_string(outer_index));
                        // If the balls are right above/below each other, just pick a very big angle to avoid doing a divide by zero
                        // The large angle should ensure that the 'bad' ball is removed
                        ball_angle_degrees = 89;
                    }
                    else {
                        // Calculate angle so that it doesn't matter which ball is to the left
                        ball_angle_degrees = CvUtils::RadiansToDegrees(atan((double)(b.y() - current_ball.y()) /
                            (double)std::abs(b.x() - current_ball.x())));;
                    }

                    if (b.x() > current_ball.x()) {
                        // The ball to be compared to the outer loop ball is to the right of the outer loop
                        ball_angle_degrees = -ball_angle_degrees;
                    }
                    else {
                        // The ball to be compared to the outer loop ball is to the left of the outer loop
                        // Leave the angles alone
                    }

                    // The angles are opposite if the ball is moving right to left
                    if (GolfSimOptions::GetCommandLineOptions().golfer_orientation_ == GolferOrientation::kLeftHanded) {
                        ball_angle_degrees = -ball_angle_degrees;
                    }

                    double min_angle = 0;
                    double max_angle = 0;

                    // We will generally allow much smaller angles if we're putting
                    if (GolfSimClubs::GetCurrentClubType() == GolfSimClubs::kPutter) {
                        min_angle = kMinPuttingQualityExposureLaunchAngle;
                        max_angle = kMaxPuttingQualityExposureLaunchAngle;
                    }
                    else {
                        min_angle = kMinQualityExposureLaunchAngle;
                        max_angle = kMaxQualityExposureLaunchAngle;
                    }

                    if (ball_angle_degrees < min_angle || ball_angle_degrees > max_angle) {
                        GS_LOG_TRACE_MSG(trace, "Not analyzing ball " + std::to_string(i) + " due to its unlikely angle of "
                            + std::to_string(ball_angle_degrees) + " degrees with respect to ball number " + std::to_string(outer_index));

                        initial_balls.erase(initial_balls.begin() + i);
                    }
                }

                outer_index++;
            }
        }



        void GolfSimCamera::RemoveWrongColorBalls(const cv::Mat& rgbImg, 
                                                    std::vector<GolfBall>& initial_balls,
                                                    const GolfBall& expected_best_ball,
                                                    const double max_strobed_ball_color_difference) {

            GS_LOG_TRACE_MSG(trace, "GolfSimCamera::RemoveWrongColorBalls");

            if (initial_balls.size() < 1) {
                GS_LOG_TRACE_MSG(warning, "RemoveWrongColorBalls - balls vector was empty.  Exiting function.");
                return;
            }

            // Get the color and std of the ball that is the most likely to be a real ball
            std::vector<GsColorTriplet> statistics = CvUtils::GetBallColorRgb(rgbImg, expected_best_ball.ball_circle_);
            GsColorTriplet expectedBallRGBAverage{ statistics[0] };
            GsColorTriplet expectedBallRGBMedian{ statistics[1] };
            GsColorTriplet expectedBallRGBStd{ statistics[2] };

            // Expect that the expected_best_ball will not be removed from the vector, as it's differences 
            // should be zero.

            for (int i = (int)initial_balls.size() - 1; i >= 0; i--) {
                GolfBall& b = initial_balls[i];

                std::vector<GsColorTriplet> statistics = CvUtils::GetBallColorRgb(rgbImg, b.ball_circle_);
                GsColorTriplet avg_RGB{ statistics[0] };
                GsColorTriplet median_RGB{ statistics[1] };
                GsColorTriplet std_RGB{ statistics[2] };

                // Save the information for later - TBD - Centralize this earlier somewhere
                b.average_color_ = avg_RGB;
                b.std_color_ = std_RGB;

                // Draw the outer circle if in debug
                GS_LOG_TRACE_MSG(trace, "\n\nExamining circle No. " + std::to_string(i) + ".  Radius " + std::to_string(b.measured_radius_pixels_) +
                    " pixels. Average RGB is{ " + LoggingTools::FormatGsColorTriplet(avg_RGB)
                    + ". Average HSV is{ " + LoggingTools::FormatGsColorTriplet(CvUtils::ConvertRgbToHsv(avg_RGB)));

                // Determine how "different" the average color is from the expected ball color
                // If we don't have an expected ball color, than we use the RGB center from the  
                // current mask
                float rgb_avg_diff = CvUtils::ColorDistance(avg_RGB, expectedBallRGBAverage);
                float rgb_median_diff = CvUtils::ColorDistance(median_RGB, expectedBallRGBMedian);   // TBD
                float rgb_std_diff = CvUtils::ColorDistance(std_RGB, expectedBallRGBStd);   // TBD

                // Even if a potential ball has a really close median color, if the STD is even a little off, we want to down - grade it
                // The following works to mix the three statistics together appropriately
                // Will also penalize balls that are found toward the tail end of the list
                //  NOMINAL - large StdDiff was throwing off? float calculated_color_difference = rgb_avg_diff + (float)(100. * pow(rgb_std_diff, 2.));
                // TBD - this needs to be optimized and should probably be different than the code in the BallImageProc class.
                //                    double calculated_color_difference = pow(rgb_avg_diff,2) + (float)(2. * pow(rgb_std_diff, 2.)) + (float)(125. * pow(i, 4.));
                // NOTE - if the flash-times are different for the ball we are using for the color, this is likely to pick the wrong thing.

                // We are primarily concerned about situations where the median RGB went UP, because that's usually what happens when a ball overlaps
                // with another ball(s).  We are going to weigh that situation more heavily
                double calculated_color_difference = 0.;
                double rgb_difference_component = 0.;
                double std_difference_component = 0.;
                std::string brightness = "darker";

                if (CvUtils::IsDarker(avg_RGB, expectedBallRGBMedian)) {
                    brightness = "darker";
                    rgb_difference_component = (double)(kColorDifferenceRgbPostMultiplierForDarker * pow(1.0 * rgb_avg_diff, 2.));
                    std_difference_component = (double)(kColorDifferenceStdPostMultiplierForDarker * pow(2.3 * rgb_std_diff, 2.));

                    calculated_color_difference = rgb_difference_component + std_difference_component;
                } 
                else {
                    brightness = "lighter";
                    rgb_difference_component = (double)(kColorDifferenceRgbPostMultiplierForLighter * pow(1.0 * rgb_avg_diff, 2.));
                    std_difference_component = (double)(kColorDifferenceStdPostMultiplierForLighter * pow(2.0 * rgb_std_diff, 2.));

                    calculated_color_difference = rgb_difference_component + std_difference_component;
                }

                GS_LOG_TRACE_MSG(trace, "Found " + brightness + " circle number " + std::to_string(i) + "(x,y) = (" + std::to_string(b.x()) + ", " + std::to_string(b.y()) + "). radius = " + std::to_string(b.measured_radius_pixels_) +
                    " rgb_avg_diff = " + std::to_string(rgb_avg_diff) +
                    " CALCDiff = " + std::to_string(calculated_color_difference) + " rgbDiff = " + std::to_string(rgb_avg_diff) +
                    " rgb_median_diff = " + std::to_string(rgb_median_diff) + " rgb_std_diff = " + std::to_string(rgb_std_diff));

                // Identify any balls that are outside the expected radius range by retaining them only in the initial ball vector
                if (calculated_color_difference > max_strobed_ball_color_difference) {
                    GS_LOG_TRACE_MSG(trace, "  Not analyzing found ball No. " + std::to_string(i) + " due to it having too different a color ( difference was " +
                        std::to_string(calculated_color_difference) + "), and the max was " + std::to_string(max_strobed_ball_color_difference) + ".\n");
                    GS_LOG_TRACE_MSG(trace, " rgb_difference_component was " + std::to_string(rgb_difference_component) + "), and std_difference_component was " + std::to_string(std_difference_component) + ".\n\n");
                    initial_balls.erase(initial_balls.begin() + i);
                }

            }

        }


        void GolfSimCamera::RemoveWrongRadiusBalls(std::vector<GolfBall>& initial_balls,
                                                   const GolfBall& expected_best_ball ) {

            GS_LOG_TRACE_MSG(trace, "GolfSimCamera::RemoveWrongRadiusBalls");

            double nominal_radius = expected_best_ball.measured_radius_pixels_;
               
            // Expect that the expected_best_ball will not be removed from the vector, as it's differences 
            // should be zero.

            for (int i = (int)initial_balls.size() - 1; i > 0; i--) {
                GolfBall& b = initial_balls[i];

                double radius_difference = std::abs(nominal_radius - b.measured_radius_pixels_);
                double max_radius_different = nominal_radius * (kMaxRadiusDifferencePercentageFromBest / 100.0);

                // Remove any balls that are too far away from the expected radius range
                if (radius_difference > max_radius_different) {
                    GS_LOG_TRACE_MSG(trace, "  Not analyzing found ball No. " + std::to_string(i) + " due to it having too different a radius from best ball ( difference was " +
                        std::to_string(radius_difference) + "), and the max was " + std::to_string(max_radius_different));
                    initial_balls.erase(initial_balls.begin() + i);
                }
            }
        }

        void GolfSimCamera::ReportBallSearchError(const int number_balls_found) {
            std::string root_cause_str;

            if (number_balls_found == 0) {
                root_cause_str = "Unable to find ANY ball exposures after ball hit.  Did ball move inadvertently?";
            }
            else if (number_balls_found == 1) {
                root_cause_str = "Unable to find at least two ball exposures after ball hit.  It's possible the ball was hit faster or slower than the system can handle.";
            }
            else {
                root_cause_str = "An error occurred while processing the post-hit ball image.  Please check logs.";
            }

            LoggingTools::current_error_root_cause_ = root_cause_str;
            GS_LOG_MSG(error, root_cause_str);
        }

        bool GolfSimCamera::AnalyzeStrobedBalls( const cv::Mat& strobed_balls_color_image,
                                                 const cv::Mat& strobed_balls_gray_image,
                                                 const GolfBall& calibrated_ball,
                                                 GsBallsAndTimingVector& return_balls_and_timings,
                                                 GsBallsAndTimingVector& non_overlapping_balls_and_timing,
                                                 GolfBall& face_ball,
                                                 GolfBall& ball2,
                                                 long& time_between_ball_images_uS  ) {

            GS_LOG_TRACE_MSG(trace, "AnalyzeStrobedBalls(ball).  calibrated_ball = " + calibrated_ball.Format());

            if (!calibrated_ball.calibrated) {

                GS_LOG_MSG(error, "AnalyzeStrobedBall called without a properly calibrated ball.");
                return false;
            }

            if (GolfSimClubs::GetCurrentClubType() == GolfSimClubs::kPutter) {
                GS_LOG_MSG(info, "In putting mode.");
            }
            else {
                GS_LOG_MSG(info, "In driving mode.");
            }


            BallImageProc* ip = get_image_processor();

            LoggingTools::DebugShowImage("GolfSimCamera::TestAnalyzeStrobedBall COLOR input: ", strobed_balls_color_image);
            LoggingTools::DebugShowImage("GolfSimCamera::TestAnalyzeStrobedBall GRAY input: ", strobed_balls_gray_image);

            // Find where the ball currently is based on where we expected it from the prior information

            double distance_at_calibration_ = calibrated_ball.distance_at_calibration_;

            // Approximate the new distance based just on the X/Z plane distance, assuming
            // the ball will be hit straight
            double expected_camera2_distance = calibrated_ball.distances_ortho_camera_perspective_[2];
            if (expected_camera2_distance < 0.0001) {
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
