ronheywood/PiTrac/Software/LMSourceCode/ImageProcessing/ball_image_proc.h

/* SPDX-License-Identifier: GPL-2.0-only */
/*
 * Copyright (C) 2022-2025, Verdant Consultants, LLC.
 */

// Performs image processing such as finding a ball in a picture.
// TBD - The separation of responsibilities with the golf_sim_camera needs to be clarified.

#pragma once


#include <iostream>
#include <filesystem>

#include <opencv2/core.hpp>
#include <opencv2/imgcodecs.hpp>
#include <opencv2/imgproc.hpp>
#include <opencv2/highgui.hpp>

#include "logging_tools.h"
#include "gs_camera.h"
#include "colorsys.h"
#include "golf_ball.h"


namespace golf_sim {

// When comparing what are otherwise b/w images, this value indicates that
// the comparison should not be performed on the particular pixel
const uchar kPixelIgnoreValue = 128;

// Holds one potential rotated golf ball candidate image and associated data
struct RotationCandidate {
    short index = 0;
    cv::Mat img;
    int x_rotation_degrees = 0; // All Rotations are in degrees
    int y_rotation_degrees = 0;
    int z_rotation_degrees = 0;
    int pixels_examined = 0;
    int pixels_matching = 0;
    double score = 0;
};

class BallImageProc
{
public:

    // The following are constants that control how the ball spin algorithm and the
    // ball (circle) identification works.  They are set from the configuration .json file
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
